Aleesca/Practica_GLP/Proyecto/Datos.md

# Grupo G1-1

## Datos comunes

| Campo | Dato |
|---|---|
| Zona climatica | Leon |
| Temperatura exterior de calculo | Pendiente de fijar con referencia tecnica valida |
| Ubicacion | Parcela catastral `8638004TN8183N` |
| Plano base | `01_Planos/instalacion_GLP.dwg` |
| Enunciado | `00_Info_proporcionada/TAREA 3 calculo instalación GLP.pdf` |

## Consumidores del grupo

| Consumidor | Potencia de calculo | Horas de funcionamiento | Distancias a medir |
|---|---:|---:|---|
| Consumidor 1: Horno secado | 60 kW | 12 h/d | Medir segun parcela y trazado real |
| Consumidor 2: Horno de secado | 60 kW | 12 h/d | Medir segun parcela y trazado real |
| Consumidor 3: Caldera vapor | 500 kW | 10 h/d | Medir segun parcela y trazado real |
| Consumidor 4: Caldera agua caliente | 300 kW | 8 h/d | Medir segun parcela y trazado real |
| Consumidor 5: Horno fusion | 700 kW | 4 h/d | Medir segun parcela y trazado real |
| Consumidor 6: Horno decapado | 1000 kW | 6 h/d | Medir segun parcela y trazado real |

## Uso operativo

- Este documento actua como fuente primaria de datos del grupo.
- La version normalizada para skills se mantiene en `.agents/skills/doc_tecnica_glp/references/datos_grupo_G1-1.md`.
- Las hipotesis derivadas de estos datos deben consolidarse en `Proyecto/Especificaciones/datos-partida.md`.
