Aleesca/Practica_GLP/ZZ_Normativa/normativa_requerida.md

# Normativa Identificada en el Modelo de Proyecto de GLP

A continuación se detallan las normas y reglamentos citados en el documento de referencia para la instalación de almacenamiento de GLP en depósitos fijos.

## 1. Instalaciones de Gas y GLP
*   **Real Decreto 191/2006**: Reglamento técnico de distribución y utilización de combustibles gaseosos.
    *   **ITC-ICG-03**: Instalaciones de almacenamiento de gases licuados del petróleo (GLP) en depósitos fijos.
*   **Norma UNE 60.250 (Abril 2004)**: Instalaciones de suministro de gases licuados del petróleo (GLP) en depósitos fijos para su consumo en instalaciones receptoras.

## 2. Edificación y Estructuras
*   **Real Decreto 314/2006**: Código Técnico de la Edificación (CTE).
    *   **DB-SI**: Seguridad en caso de Incendio.
    *   **DB-HS-3**: Calidad de aire interior.
    *   **DB-SU-8**: Seguridad frente al riesgo relacionado con la acción del rayo.
*   **Real Decreto 2661/1998**: Instrucción de Hormigón Estructural (EHE).

## 3. Instalaciones Eléctricas y Seguridad
*   **Real Decreto 848/2002**: Reglamento Electrotécnico para Baja Tensión (REBT) e Instrucciones Técnicas Complementarias (ITC).
*   **Norma UNE-EN 60.079(10)**: Material eléctrico para atmósferas de gas explosivas.
*   **Real Decreto 486/1997**: Disposiciones mínimas de seguridad y salud en los lugares de trabajo (Iluminación y condiciones ambientales).

## 4. Protección contra Incendios
*   **Real Decreto 1942/1993**: Reglamento de Instalaciones de Protección contra Incendios (RIPCI).
*   **Apartado 7.8 de la ITC-ICG-03**: Requerimientos específicos de protección contra incendios para GLP.

## 5. Otras Normativas
*   **Ley de Catastro Inmobiliario**: Modificación de diciembre de 2006 (BOE 286, de 30/11/2006) relativa a las referencias catastrales en proyectos.
