Aleesca/Practica_GLP/Proyecto/Anotaciones/autonomia_30_dias.md

# Autonomia de 30 dias

Esta nota fija el criterio para dimensionar el almacenamiento de GLP garantizando 30 días de suministro ininterrumpido para el Grupo G1-1.

## Criterio de Diseño
Aunque la recomendación técnica para instalaciones industriales suele ser de 15 días, el enunciado de la **TAREA 3** exige explícitamente una autonomía de **30 días**.

## Datos de Consumo (Grupo G1-1)
- **Energía diaria total:** 17.640 kWh/día.
- **Consumo másico diario:** 17.640 / 13,95 = **1.264,52 kg/día**.
- **Consumo volumétrico (Líquido a 20ºC):** 1.264,52 / 506 = **2,499 m³/día**.

## Cálculo del Volumen Útil y Geométrico
Para asegurar el suministro durante 30 días con una fracción útil del 65% (85% llenado máximo - 20% reserva):

- **Volumen útil necesario:** 2,499 m³/día x 30 días = **74,97 m³**.
- **Volumen geométrico mínimo:** 74,97 / 0,65 = **115,34 m³**.

## Conclusión
El volumen requerido (115,34 m³) obliga a la instalación de una **batería de depósitos**, ya que supera la capacidad individual de los modelos estándar de gran volumen.

---
**Véase también:**
- [Cálculo del volumen del depósito](calculo_volumen_deposito.md)
- [Caudales de consumidores](caudales_consumidores.md)
- [Selección del depósito](seleccion_deposito.md)
- [Distancias de seguridad](distancias_seguridad.md)
- [Memoria: Autonomía de almacenamiento](../Especificaciones/autonomia.md)
- [Memoria: Demanda y caudales de cálculo](../Especificaciones/demanda-consumo.md)
- [Memoria: Selección y dimensionado del depósito](../Especificaciones/deposito.md)
