Aleesca/Practica_GLP/Proyecto/Anotaciones/caudales_consumidores.md

# Caudales de consumidores

Esta nota define el procedimiento para pasar de potencia y régimen de uso a demanda de cálculo de la instalación para el Grupo G1-1.

## Metodología
Se utiliza la potencia nominal de cada equipo y sus horas de funcionamiento previstas para determinar la energía diaria necesaria.

## Tabla Maestra de Consumidores
| Consumidor | Potencia (kW) | Horas (h/d) | Energía (kWh/d) |
|---|---:|---:|---:|
| Horno secado 1 | 60 | 12 | 720 |
| Horno secado 2 | 60 | 12 | 720 |
| Caldera vapor | 500 | 10 | 5000 |
| Caldera agua caliente | 300 | 8 | 2400 |
| Horno fusion | 700 | 4 | 2800 |
| Horno decapado | 1000 | 6 | 6000 |
| **Total** | **2620** | - | **17640** |

## Salidas para el Proyecto
1.  **Potencia Máxima Simultánea:** 2.620 kW (base para el [trazado de red](trazado_red.md)).
2.  **Energía Diaria Total:** 17.640 kWh/d (base para el [cálculo del volumen](calculo_volumen_deposito.md)).

---
**Véase también:**
- [Cálculo del volumen del depósito](calculo_volumen_deposito.md)
- [Trazado de red](trazado_red.md)
- [Vaporización natural](vaporizacion_natural.md)
- [Dimensionado de tuberías GLP](dimensionado_tuberias_glp.md)
- [Memoria: Hipótesis y datos de partida](../Especificaciones/datos-partida.md)
- [Memoria: Demanda y caudales de cálculo](../Especificaciones/demanda-consumo.md)
- [Memoria: Red de distribución y regulación](../Especificaciones/red-distribucion.md)
- [Memoria: Autonomía de almacenamiento](../Especificaciones/autonomia.md)
