Aleesca/Practica_GLP/Proyecto/Anotaciones/criterios_normativos.md

# Criterios normativos

Esta nota recopila la normativa aplicable al proyecto de GLP del Grupo G1-1.

## Normativa Principal
- **UNE 60250:** Almacenamiento de GLP en depósitos fijos.
- **RD 919/2006:** Reglamento técnico de distribución y utilización de combustibles gaseosos.
- **CTE (Código Técnico de la Edificación):** Específicamente DB-SI y DB-SUA.

## Aplicación
Estos criterios justifican las [distancias de seguridad](distancias_seguridad.md) y los cálculos del [trazado de red](trazado_red.md).

---
**Véase también:**
- [Distancias de seguridad](distancias_seguridad.md)
- [Trazado de red](trazado_red.md)
- [Selección del depósito](seleccion_deposito.md)
- [Dimensionado de tuberías GLP](dimensionado_tuberias_glp.md)
- [Memoria: Hipótesis y datos de partida](../Especificaciones/datos-partida.md)
- [Memoria: Implantación y distancias de seguridad](../Especificaciones/implantacion-seguridad.md)
- [Memoria: Instalaciones auxiliares y de seguridad de la estación](../Especificaciones/instalaciones-auxiliares.md)
- [Cálculos justificados: Cálculos de seguridad y auxiliares](../Especificaciones/calculos-auxiliares.md)
