Aleesca/Practica_GLP/Proyecto/Anotaciones/pliego_condiciones_equipos_glp.md

# Pliego de Condiciones Técnicas: Adquisición de Equipos Principales GLP

## 1. Objeto del Documento
El presente pliego establece las condiciones técnicas, normativas y de suministro que regirán la adquisición de la batería de depósitos de Gases Licuados del Petróleo (GLP) y su sistema de vaporización asociado, destinados a la instalación receptora del Grupo G1-1.

## 2. Alcance del Suministro
El adjudicatario / fabricante deberá suministrar, transportar y garantizar los siguientes equipos principales:

1.  **Un (1) Depósito Principal Especial:** Modelo base Lapesa LP46A-22 (Aéreo Horizontal) de 46.200 litros (46,2 m³), modificado en fábrica para incorporar un serpentín de vaporización interna (modelo VIA 150 o equivalente validado).
2.  **Tres (3) Depósitos de Apoyo:** Modelo estándar Lapesa LP26A-22 (Aéreos Horizontales) de 26.300 litros (26,3 m³) cada uno.
3.  **Un (1) Armario de Calefacción:** Modelo Lapesa VPC30C, dimensionado para operar en conjunto con el serpentín interno del depósito principal, garantizando una capacidad de vaporización forzada no inferior a 227 kg/h.
4.  **Valvulería Asociada de Serie:** Todas las válvulas de seguridad (alivio), de llenado, extracción de fase líquida/gas y nivel magnético correspondientes a la homologación de cada depósito.

## 3. Condiciones Técnicas de los Equipos

### 3.1. Depósitos Estáticos (LP46A-22 Especial y LP26A-22)
- **Tipo de Gas:** Propano comercial / GLP.
- **Instalación:** Aérea, sobre cunas de hormigón armado.
- **Presión de Diseño:** Mínimo 20 bar.
- **Materiales:** Chapa de acero al carbono soldada según procedimientos homologados.
- **Tratamiento Exterior:** Granallado SA 2-1/2, imprimación anticorrosiva epoxi-poliamida de alto espesor y acabado exterior con esmalte de poliuretano color blanco, altamente reflectante.
- **Particularidad LP46A-22:** Deberá integrar de fábrica las bridas de conexión y la inserción del intercambiador de calor (serpentín VIA) en la generatriz inferior, asegurando el sellado y certificación conjunta del recipiente a presión.

### 3.2. Sistema de Vaporización (Serpentín VIA + Armario VPC30C)
- **Fluido Caloportador:** Agua glicolada (o fluido térmico especificado por el fabricante) calentada por el armario VPC30C y circulada mediante bomba hasta el serpentín interno.
- **Armario de Calefacción:** Deberá incluir caldera, bomba aceleradora, vaso de expansión, valvulería de corte, termostatos de control y seguridad, y armario de protección intemperie (ATEX si se ubica en Zona 2).
- **Rendimiento:** El sistema en conjunto debe ser capaz de vaporizar en continuo el caudal punta de diseño independientemente de la temperatura ambiente (hasta -10ºC exterior).

## 4. Normativa y Certificaciones Exigibles
El fabricante deberá entregar con el suministro la siguiente documentación, asegurando el cumplimiento normativo:
- **Directiva 2014/68/UE:** Certificado de Evaluación de Conformidad (Marcado CE) para Equipos a Presión.
- **Normas de Diseño:** UNE-EN 12542 (o ASME VIII Div. 1 según proceda por el fabricante).
- **Válvulas de Alivio:** Taradas a 20 bar (±10%), certificadas bajo UNE-EN 14129, incluyendo certificados de precinto.
- Dossier de calidad que incluya certificados de materiales (3.1 según EN 10204), radiografiado de soldaduras y acta de la prueba hidrostática o neumática realizada en fábrica.

## 5. Pruebas y Ensayos
### 5.1. En Fábrica (FAT - Factory Acceptance Tests)
El fabricante realizará las pruebas hidrostáticas a la presión de timbre exigida por la normativa vigente. En el caso del depósito especial LP46A, la prueba de presión deberá realizarse con el serpentín interno ya instalado para garantizar la estanqueidad de las bridas de conexión.

### 5.2. En Obra (SAT - Site Acceptance Tests)
Tras el montaje mecánico, el adjudicatario del montaje (con soporte del fabricante si es necesario) realizará pruebas de estanqueidad con nitrógeno de todo el conjunto y valvulería antes del primer llenado.

## 6. Condiciones de Entrega y Transporte
- **Transporte Especial:** El suministro se considera en condición DDP (Delivered Duty Paid) o franco sobre camión en la obra (Valle de Escombreras / ubicación designada).
- El fabricante será responsable de coordinar el transporte especial por dimensiones (convoy especial) y suministrará los planos de izado (orejetas) con el centro de gravedad marcado para la correcta descarga mediante grúa autopropulsada proporcionada por el contratista principal.
- Los depósitos deberán llegar presurizados con una presión positiva de gas inerte (nitrógeno) para garantizar la ausencia de humedad interna durante el tránsito.

## 7. Garantías
- **Garantía Mecánica y de Estanqueidad:** Mínimo de cinco (5) años contra defectos de fabricación o perforación por corrosión.
- **Garantía de Equipos Auxiliares (Armario VPC):** Mínimo de dos (2) años.
- El fabricante deberá garantizar la compatibilidad absoluta y el rendimiento del conjunto Depósito Principal + Serpentín VIA + Armario Calefacción.

---
**Véase también:**
- [Selección del depósito](seleccion_deposito.md)
- [Recopilación de accesorios y costes](recopilacion_accesorios_costes_glp.md)
- [Vaporización forzada](vaporizacion_forzada.md)
- [Potencia del armario de calefacción](potencia_armario_calefaccion.md)
- [Valvulería y accesorios](valvuleria_accesorios.md)
- [Memoria: Selección y dimensionado del depósito](../Especificaciones/deposito.md)
- [Memoria: Vaporización natural vs. vaporización forzada](../Especificaciones/vaporizacion.md)
- [Memoria: Características de los equipos auxiliares del almacenamiento](../Especificaciones/equipos-auxiliares.md)
- [Especificación: Presupuesto y mediciones](../Especificaciones/presupuesto.md)
