Aleesca/Practica_GLP/Proyecto/Especificaciones/anejos.md

# Cálculos justificados: Índice de anexos e inserción de planos

El presente documento recopila la relación y estructura de los anexos reales del proyecto de almacenamiento y distribución de GLP del Grupo G1-1, así como los planos técnicos integrados. Su función es delimitar qué piezas se incorporan como documentación anexa y qué contenidos deben permanecer dentro del capítulo de **Cálculos justificados**.

---

## 3.1. Índice de Anexos

El proyecto técnico se complementa con los siguientes anexos documentales y gráficos que contienen la información comercial de catálogo, los esquemas de funcionamiento y la documentación auxiliar que respalda el proyecto. Los cálculos mecánicos, térmicos e hidráulicos no se tratan como un anejo independiente: su desarrollo, tablas, resultados intermedios y comprobaciones forman parte del capítulo **Cálculos justificados** de la plantilla LaTeX.

*   **Anexo I: Planos Técnicos.**
    Representación gráfica a escala de la implantación, distancias de seguridad y esquema hidráulico (P&ID) de la instalación de GLP.
*   **Anexo II: Comprobaciones y Tablas Auxiliares.**
    Fichas técnicas y especificaciones comerciales del fabricante Lapesa correspondientes a:
    *   Depósitos de almacenamiento modelos LP46A-22 (Modelo Especial) y LP26A-22.
    *   Serpentín del vaporizador forzado interno modelo VIA 150.
    *   Armario de calefacción exterior y caldera modelo VPC30C.

El desarrollo matemático, el control de trazabilidad y las comprobaciones hidráulicas tramo a tramo para la red de distribución aérea en Media Presión B (1,7 bar relativos) se integran en las subsecciones del capítulo **Cálculos justificados**. Si se incorporan tablas auxiliares de gran formato, se insertarán como piezas editoriales del capítulo, no como un anejo de cálculos.

---

## Capítulo de Planos

El conjunto gráfico del proyecto está conformado por tres planos técnicos fundamentales de diseño, insertados de forma consecutiva e independiente al final de la memoria documental:

1.  **Plano nº 1: Situación y Emplazamiento (`situacion-emplazamiento.pdf`).**
    Representación de la ubicación geográfica de la parcela catastral `8638004TN8183N` en el término municipal de León, indicando la orientación y los viales de comunicación circundantes.
2.  **Plano nº 2: Distancias de Seguridad y Acondicionamiento del Recinto (`Plano_distancias_seguridad.pdf`).**
    Plano a escala del recinto vallado del almacenamiento de categoría A-500. Detalla el replanteo de la cuna y losa de hormigón de los cuatro depósitos, la localización de los muros EI-120 de protección y la verificación geométrica de las distancias de seguridad mínimas admisibles en todas las direcciones radiales.
3.  **Plano nº 3: Esquema de Principio (P&ID) y Conducciones (`plano_Esquema_instalacion.pdf`).**
    Diagrama de flujo hidráulico de la instalación. Muestra la boca de carga rápida, el colector común de fase gaseosa y líquida, el conexionado del vaporizador forzado VIA 150 con el armario VPC30C, la valvulería de seguridad y regulación de primer salto (1,7 bar), el trazado de las tuberías de distribución aérea con sus diámetros y el segundo salto de regulación (37 mbar) a la entrada de cada consumidor.

## Referencias relacionadas
- [Especificación: Capítulo de Cálculos justificados](calculos-justificados.md)
- [Memoria: Selección y dimensionado del depósito](deposito.md)
- [Memoria: Implantación y distancias de seguridad](implantacion-seguridad.md)
- [Memoria: Red de distribución y regulación](red-distribucion.md)
- [Cálculos justificados: Cálculos de seguridad y auxiliares](calculos-auxiliares.md)
- [Pliego de condiciones técnicas: adquisición de equipos principales GLP](../Anotaciones/pliego_condiciones_equipos_glp.md)
- [Implantación y distancias de seguridad](../Anotaciones/distancias_seguridad.md)
