Aleesca/Practica_GLP/Proyecto/Especificaciones/equipos-auxiliares.md

# Memoria: Características de los Equipos Auxiliares del Almacenamiento

## 1. Boca de Carga y Limitador de Llenado
La operación de llenado de propano líquido en los depósitos se realiza de forma centralizada en el colector común de fase líquida mediante una boca de carga única exterior, diseñada para soportar las presiones de trasvase del camión cisterna:
*   **Acoplamiento Rápido:** Se adopta un acoplamiento rápido macho de rosca Acme de **$3\text{''}$** (modelo **RegO 7579C** o equivalente) fabricado en latón de alta resistencia al desgaste mecánico.
*   **Seguridades Antirretorno:** Dispone de una **doble válvula de retención integrada (check valve)** en serie para evitar el escape accidental de gas licuado al desconectar la manguera de llenado.
*   **Válvula de Purga y Cierre:** Se monta una válvula de purga de bola manual de $1/4\text{''}$ para despresurizar de forma segura el espacio entre acoplamientos antes de la desconexión física.
*   **Válvula Limitadora de Llenado al $85\%$:** Cada depósito incorpora una válvula interna automática de boya (limitadora de nivel máximo de llenado) que interrumpe mecánicamente el paso de líquido cuando el nivel del propano alcanza el $85\%$ del volumen geométrico del recipiente.

## 2. Equipos de Regulación de Presión y Válvulas de Corte
Para la estabilidad del flujo y aislamiento de componentes en la estación, se disponen los siguientes equipos:
*   **Regulador de Primer Salto (MPB):** Acoplado directamente a la salida del colector común de fase de gas de los depósitos. Se utiliza un regulador de alta capacidad **RegO 1588V** o **Clesse APS** tarado a **$1,7\text{ bar relativos}$**. Incorpora válvula de seguridad de mínima presión por bloqueo de seguridad (UPS) y filtro de partículas metálicas en la entrada.
*   **Válvulas de Corte General:** Válvulas de esfera de paso total de bronce o acero forjado (clase ANSI 300) con accionamiento manual por palanca e indicación de posición abierta/cerrada, situadas a la salida de cada depósito y en la entrada y salida de cada regulador para permitir el aislamiento completo en labores de mantenimiento.

## 3. Equipo de Trasvase (Bomba)
Para la tipología y demandas operativas de esta planta industrial (donde el GLP fluye por diferencia de presiones gaseosas y por gravedad hacia los vaporizadores), **no se requiere la instalación de una bomba activa de trasvase de líquido** en la estación de almacenamiento. Las operaciones de carga de los depósitos se realizan aprovechando la propia bomba de impulsión de fase líquida del camión cisterna y la línea de retorno de fase de gas (línea de equilibrio de presiones) que une la cisterna con el colector de la estación.

## 4. Válvulas de Seguridad por Sobrepresión
Para proteger los depósitos de almacenamiento frente a sobrepresiones excesivas debidas a la radiación solar estacional o al calor de un incendio cercano, cada depósito está equipado con:
*   **Configuración:** **Dos unidades de válvulas de seguridad independientes** de resorte por depósito (taradas a la misma presión de apertura).
*   **Modelo de Válvula:** Válvula de alivio de presión **RegO RS 3145** (o equivalente de Lapesa) fabricada en bronce y acero inoxidable.
*   **Presión de Tarado:** Apertura completa a **$20\text{ bar relativos}$**, presión inferior a la presión de prueba del recipiente ($25\text{ bar}$) para garantizar que no se supera el límite elástico del acero del depósito en caso de emergencia.
*   **Acoplamiento y Colector de Escape:** Las válvulas se montan sobre colectores de desvío de tres vías (**colectores de acoplamiento CD45**), lo que permite desmontar e inspeccionar periódicamente una de las dos válvulas de seguridad sin necesidad de desgasificar o vaciar el depósito de almacenamiento, garantizando que al menos una de las válvulas de alivio permanece en servicio en todo momento. Las descargas se conducen de forma vertical a la atmósfera mediante tubos deflectores que sobresalen por encima del depósito.

## Referencias relacionadas
- [Memoria: Selección y dimensionado del depósito](deposito.md)
- [Memoria: Vaporización natural vs. vaporización forzada](vaporizacion.md)
- [Memoria: Instalaciones auxiliares y de seguridad de la estación](instalaciones-auxiliares.md)
- [Cálculos justificados: Cálculos de seguridad y auxiliares](calculos-auxiliares.md)
- [Valvulería y accesorios comerciales](../Anotaciones/valvuleria_accesorios.md)
- [Pliego de condiciones técnicas: adquisición de equipos principales GLP](../Anotaciones/pliego_condiciones_equipos_glp.md)
- [Vaporización forzada](../Anotaciones/vaporizacion_forzada.md)
