Aleesca/Practica_GLP/Proyecto/Especificaciones/implantacion-seguridad.md

# Memoria: Implantación y Distancias de Seguridad

## 1. Clasificación Reglamentaria de las Instalaciones y Entorno
El almacenamiento conjunto proyectado cuenta con un volumen geométrico total acumulado de **$124,30\text{ m}^3$** de propano comercial líquido. De acuerdo con lo establecido en la norma **UNE 60250:2008** y el *Reglamento técnico de distribución y utilización de combustibles gaseosos* (RD 919/2006, ITC-ICG 03), la estación de almacenamiento se clasifica como una **instalación del Tipo A-500** al cumplir la condición:

$$ 100\text{ m}^3 < V_{total} \le 500\text{ m}^3 $$

Esta clasificación impone los máximos requisitos de distancias de seguridad y protección contra incendios de la normativa para almacenamientos de GLP de consumo industrial.

## 2. Justificación Geométrica de la Implantación de la Batería
La batería de depósitos se sitúa en paralelo en una zona abierta y despejada del exterior de la parcela catastral **8638004TN8183N**, facilitando la ventilación natural y el acceso del camión cisterna de suministro. 

*   **Separación Mínima entre Depósitos de la Batería:**
    Según la norma UNE 60250, para depósitos aéreos de la misma batería, la distancia mínima de separación entre las paredes de dos tanques contiguos debe ser igual a la mitad del diámetro del depósito mayor, con un límite mínimo absoluto de **$1,0\text{ m}$**. Dado que todos los depósitos seleccionados (LP46A y LP26A) tienen un diámetro común exterior de $2.200\text{ mm}$ ($\phi = 2,2\text{ m}$), la separación mínima reglamentaria resulta:
    $$ D_{separacion} \ge \frac{\phi}{2} = \frac{2,2\text{ m}}{2} = 1,10\text{ m} $$
    Para cumplir con este requisito técnico y permitir un paso desahogado para labores de mantenimiento y evacuación de aguas pluviales de los tanques, se adopta una **separación real de $1,10\text{ m}$ en paralelo** entre los ejes de cunas y paredes de los cuatro depósitos de la batería.

## 3. Verificación de Distancias de Seguridad y Medidas Reductoras
La norma UNE 60250 exige mantener unas distancias de seguridad mínimas desde los orificios de los depósitos (válvulas de seguridad, boca de carga y purgas) y desde las paredes exteriores de los tanques hacia elementos externos de la parcela. Para depósitos de Tipo A-500, la distancia de referencia básica es de **$10\text{ metros}$**.

Dada la colindancia de la parcela catastral con límites de propiedad ajena y viales en sus bordes norte y oeste, no es viable cumplir con los $10\text{ metros}$ de separación natural. Se recurre, por tanto, a la aplicación de las **medidas reductoras** contempladas en la normativa (UNE 60250, apartado de muros):
*   **Instalación de Muros Cortafuegos EI-120:**
    Se proyecta la construcción de dos muros de protección cortafuegos con clasificación de resistencia al fuego **$EI-120$** (estable, estanco e islante térmico al fuego durante al menos 120 minutos), fabricados en hormigón armado con un espesor mínimo de $150\text{ mm}$ y una altura que sobresale un metro sobre el punto más alto del depósito (altura del muro: $3,50\text{ metros}$).
*   **Reducción de Distancias al $50\%$:**
    El uso de estos muros cortafuegos EI-120 permite **reducir al $50\%$** la distancia de seguridad exigida hacia límites de propiedad, locales públicos y focos de ignición no clasificados, reduciéndose la distancia mínima a **$5,0\text{ metros}$** de separación medida alrededor del muro (trayectoria de gas).
*   **Verificación Real en Plano:**
    Las distancias reales medidas en el plano de implantación (`Plano_distancias_seguridad.pdf`), considerando la trayectoria de gas bordeando los muros cortafuegos EI-120, superan en todos los puntos críticos los $5,0\text{ metros}$ reglamentarios, demostrando la viabilidad técnica y legal del emplazamiento elegido.

## 4. Vallado y Cerramiento Perimetral de Seguridad
Para evitar el acceso de personal ajeno a la instalación y prevenir riesgos de sabotaje o manipulación accidental de válvulas, el recinto de la estación de almacenamiento común estará delimitado por un **cerramiento de seguridad perimetral**:
*   **Características del Vallado:** Vallado metálico tipo Hércules o de malla de simple torsión con una altura mínima de **$2,0\text{ metros}$** sobre postes de acero anclados en solera de hormigón. La parte inferior del vallado se cerrará con un zócalo continuo de hormigón para evitar entradas de vegetación o animales.
*   **Puertas de Acceso:** Se dispondrán dos puertas metálicas de salida peatonal en extremos opuestos del recinto, equipadas con barra antipánico y sentido de apertura obligatorio hacia el exterior de la estación. Adicionalmente, se dispondrá de una puerta de doble hoja de $4,0\text{ metros}$ de ancho para el acceso y mantenimiento de componentes grandes, abriéndose siempre hacia fuera y permaneciendo cerrada bajo candado de seguridad industrial.
*   **Señalización de Seguridad:** En las paredes exteriores del vallado se dispondrán carteles normalizados legibles de seguridad con las indicaciones: "Peligro: Materia Inflamable - Propano", "Prohibido Fumar o Encender Fuego" y "Prohibido el Paso a Toda Persona Ajena a la Instalación".

## Referencias relacionadas
- [Memoria: Selección y dimensionado del depósito](deposito.md)
- [Memoria: Instalaciones auxiliares y de seguridad de la estación](instalaciones-auxiliares.md)
- [Memoria: Promotor, plazo de ejecución y accesos](promotor-plazo-accesos.md)
- [Cálculos justificados: Cálculos de seguridad y auxiliares](calculos-auxiliares.md)
- [Implantación y distancias de seguridad](../Anotaciones/distancias_seguridad.md)
- [Criterios normativos](../Anotaciones/criterios_normativos.md)
- [Selección del depósito](../Anotaciones/seleccion_deposito.md)
