Aleesca/Practica_GLP/Proyecto/Especificaciones/intro.md

# Memoria: Introducción, Objeto y Antecedentes

## 1. Objeto del Proyecto
El objeto del presente proyecto es definir, justificar y dimensionar la instalación de almacenamiento y la red de distribución de Gases Licuados del Petróleo (GLP), concretamente propano comercial, para dar suministro energético térmico a una planta industrial situada en la provincia de León. 

El alcance del diseño abarca desde la estación de almacenamiento común —constituida por una batería de depósitos aéreos horizontales y su sistema de vaporización asociado— hasta la regulación secundaria e individual a la entrada de cada uno de los seis puntos de consumo (consumidores industriales). El diseño de la instalación se proyecta bajo premisas estrictas de seguridad industrial, optimización vial y eficiencia técnica, garantizando en todo momento el cumplimiento de la reglamentación y normativa española vigente.

## 2. Antecedentes
La planta industrial requiere de un suministro continuo de calor de alta densidad energética y estabilidad térmica para sus procesos de secado, fusión, vaporización y decapado. Ante la inexistencia de una red de distribución de gas natural en las proximidades de la parcela catastral, se realiza un estudio de alternativas energéticas:
*   **Gasoil o combustibles líquidos:** Descartados debido a su mayor impacto de emisiones contaminantes, costes operativos inestables y requerimientos de mantenimiento más exigentes para los quemadores de hornos de precisión.
*   **Electricidad:** Descartada por su inviabilidad económica para potencias de calefacción agregadas del orden de megavatios.
*   **Propano comercial (GLP):** Seleccionado como la alternativa óptima debido a su elevado Poder Calorífico Superior (PCS = $13,95\text{ kWh/kg}$), su combustión limpia, la facilidad de regulación de la temperatura en los quemadores industriales y su estabilidad de suministro mediante transporte por camión cisterna.

La dirección técnica de la planta industrial ha solicitado la redacción de este proyecto con el propósito de legalizar y ejecutar la instalación común de almacenamiento y la posterior distribución interior de propano, cubriendo los siguientes seis consumidores específicos en la fase de diseño:
1.  **Horno de secado 1 (C1):** $60\text{ kW}$ de potencia nominal.
2.  **Horno de secado 2 (C2):** $60\text{ kW}$ de potencia nominal.
3.  **Caldera de vapor (C3):** $500\text{ kW}$ de potencia nominal.
4.  **Caldera de agua caliente (C4):** $300\text{ kW}$ de potencia nominal.
5.  **Horno de fusión (C5):** $700\text{ kW}$ de potencia nominal.
6.  **Horno de decapado (C6):** $1000\text{ kW}$ de potencia nominal.

La redacción de este documento y sus cálculos hidráulicos y de implantación correspondientes servirán como base técnica para la ejecución material de las obras y su posterior tramitación ante los organismos oficiales de Industria de la Junta de Castilla y León.

## Referencias relacionadas
- [Memoria: Hipótesis y datos de partida](datos-partida.md)
- [Memoria: Demanda y caudales de cálculo](demanda-consumo.md)
- [Memoria: Selección y dimensionado del depósito](deposito.md)
- [Memoria: Red de distribución y regulación](red-distribucion.md)
- [Memoria: Implantación y distancias de seguridad](implantacion-seguridad.md)
- [Criterios normativos](../Anotaciones/criterios_normativos.md)
- [Caudales de consumidores](../Anotaciones/caudales_consumidores.md)
