Aleesca/Practica_GLP/Proyecto/Especificaciones/presupuesto.md

# Especificación: Presupuesto y Mediciones (Secciones 4.1 a 4.5)

## Propósito
Detallar los costes económicos de la instalación de GLP, estructurando las mediciones reales de obra, los cuadros de precios unitarios y descompuestos, y el presupuesto de ejecución final.

## Contenido obligatorio

### Sección 4.1 ÍNDICE DE PRESUPUESTO.
- Estructurar el presupuesto en capítulos lógicos de obra:
  - Capítulo 1: Obra Civil (Excavaciones, cunas de hormigón, losa del vaporizador y vallado perimetral).
  - Capítulo 2: Almacenamiento (Depósitos Lapesa LP46A y LP26A, anclajes y cunas).
  - Capítulo 3: Equipos y Valvulería de la Estación (Vaporizador VIA 150, reguladores Clesse, válvulas de seguridad, colector común, boca de carga).
  - Capítulo 4: Red de Distribución (Tuberías de cobre UNE-EN 1057, accesorios de soldadura, soportes y ménsulas).
  - Capítulo 5: Instalaciones de Seguridad y Auxiliares (Puesta a tierra, red de pulverización de agua, extintores portátiles).
  - Capítulo 6: Ensayos y Certificaciones (Pruebas de presión, dirección de obra, puesta en marcha).

### Sección 4.2 CUADRO DE PRECIOS Nº 1.
- Listar los precios unitarios (en euros) de adquisición de todos los materiales, maquinaria y horas de mano de obra en número y letra:
  - Depósito LP46A, Depósito LP26A, Armario de vaporización VPC30C con VIA 150.
  - Tuberías de cobre por metro lineal ($\phi 54$, $\phi 42$, $\phi 35$, $\phi 28$, $\phi 22$).
  - Válvulas de corte, codos, reguladores y picas de tierra.
  - Oficiales de primera, ayudantes e ingenieros de montaje.

### Sección 4.3 CUADRO DE PRECIOS Nº 2.
- Definir los precios de unidades de obra descompuestos, integrando materiales, mano de obra instaladora, medios auxiliares e imprevistos (indicados en número y letra).

### Sección 4.4 MEDICIONES.
- Exponer el recuento físico exacto de todas las unidades de obra medidas sobre los planos de trazado y esquema base:
  - Longitudes reales de conducción de cobre por diámetro tramo a tramo.
  - Conteo exacto de válvulas de corte Giacomini, reguladores de primera y segunda etapa, codos de $90^\circ$ y derivaciones en te.
  - Volumen de excavación y hormigón estructural para cunas y losa.
  - Recuento de picas y conductor desnudo de tierra, número de rociadores.

### Sección 4.5 PRESUPUESTO.
- Consolidar los importes económicos parciales por capítulos.
- Calcular el Presupuesto de Ejecución Material (PEM) como suma de los capítulos.
- Aplicar los coeficientes legales típicos para obtener el Presupuesto de Ejecución por Contrata (PEC):
  - Gastos Generales ($13\%$).
  - Beneficio Industrial ($6\%$).
  - Impuesto sobre el Valor Añadido ($21\%$ IVA).
- Presentar el Presupuesto de Ejecución por Contrata total en letra y número.

## Estilo de redacción
Tono contable, descriptivo, preciso y formal. Presentación estructurada en tablas claras. Longitud orientativa: 2 a 3 páginas.

## Figuras, tablas y resultados
- **Tablas de precios unitarios y descompuestos:** Columnas de Código, Descripción, Unidad, Importe (en cifra) e Importe en letra.
- **Tabla de Mediciones:** Desglosada por tramos de red y capítulos de la estación.
- **Tabla Resumen del Presupuesto:** Por capítulos, PEM, PEC y Liquidación final.

## Conexiones
- **Alcance:** Requisito 5 (Conducción - mediciones) y Requisito 6 (Estación y esquema - recuentos).
- **Anotaciones:** [Recopilación y coste de accesorios por tramo GLP](../Anotaciones/recopilacion_accesorios_costes_glp.md) (evidencia), [Reporte: catálogos y precios de accesorios GLP](../Anotaciones/reporte_accesorios.md) (evidencia), [Trazado de red](../Anotaciones/trazado_red.md) (decisión).

## Referencias relacionadas
- [Memoria: Red de distribución y regulación](red-distribucion.md)
- [Memoria: Selección y dimensionado del depósito](deposito.md)
- [Memoria: Características de los equipos auxiliares del almacenamiento](equipos-auxiliares.md)
- [Memoria: Instalaciones auxiliares y de seguridad de la estación](instalaciones-auxiliares.md)
- [Recopilación y coste de accesorios por tramo GLP](../Anotaciones/recopilacion_accesorios_costes_glp.md)
- [Reporte: catálogos y precios de accesorios GLP](../Anotaciones/reporte_accesorios.md)
- [Pliego de condiciones técnicas: adquisición de equipos principales GLP](../Anotaciones/pliego_condiciones_equipos_glp.md)
- [Dimensionado de tuberías GLP](../Anotaciones/dimensionado_tuberias_glp.md)

## Criterios de aceptación
- [ ] El presupuesto está estructurado en al menos 6 capítulos lógicos.
- [ ] Los cuadros de precios contienen la descripción en número y letra.
- [ ] Las mediciones coinciden exactamente con los recuentos y metros de los archivos de anotaciones.
- [ ] Se detalla el cálculo completo de PEM a PEC aplicando los porcentajes correspondientes.
