Aleesca/Practica_GLP/Proyecto/Especificaciones/promotor-plazo-accesos.md

# Memoria: Promotor, Plazo de Ejecución y Accesos

## 1. Promotor y Proyectistas de la Instalación
La redacción y diseño técnico del presente proyecto se realiza a petición del promotor institucional y académico, la **Universidad de León (ULE)**, a través de la **Escuela de Ingenierías Industrial, Informática y Aeroespacial** (Grado en Ingeniería Mecánica, asignatura de Instalaciones II).

La autoría y responsabilidad de los cálculos, redacción y planos de la instalación de GLP corresponde al equipo de ingenieros proyectistas que integran el **Grupo G1-1**:
*   **Alberto España Carrete**
*   **Carlos Fernández Palanca**
*   **Rubén Modino López**
*   **Juan Diego Niño González**

El desarrollo del proyecto cuenta con la supervisión y tutorización técnica del profesor **Roberto Getino de la Mano**, en calidad de tutor técnico del proyecto.

## 2. Plazo de Ejecución de las Obras
El plazo estimado de ejecución material para la totalidad de las obras e instalaciones, incluyendo las fases de obra civil, montaje mecánico, pruebas y puesta en servicio, se fija en **$3\text{ meses}$** a partir de la concesión de las licencias municipales de obras e industria pertinentes. 

El cronograma de ejecución se distribuye en las siguientes fases clave:
1.  **Mes 1 (Obra Civil y Cimentaciones):**
    *   Excavación y explanación del terreno para la solera del recinto de almacenamiento.
    *   Construcción de losas de hormigón armado, cunas de apoyo para los cuatro depósitos y soleras para el vaporizador exterior.
    *   Construcción de los dos muros cortafuegos de hormigón armado EI-120 (linderos norte y oeste).
    *   Instalación de las canalizaciones subterráneas para la puesta a tierra.
2.  **Mes 2 (Montaje de Depósitos e Instalación Mecánica):**
    *   Transporte, izado y anclaje de los depósitos Lapesa LP46A y LP26A sobre sus cunas de apoyo.
    *   Montaje e interconexión mecánica del serpentín vaporizador VIA 150 en la brida DN400 del depósito principal.
    *   Instalación del armario de calefacción VPC30C y conexión del circuito de agua caliente.
    *   Montaje de las tuberías aéreas de cobre UNE-EN 1057 de la red general, colectores, soportes, liras de dilatación y válvulas de corte y seguridad.
3.  **Mes 3 (Pruebas, Aislamiento y Tramitación):**
    *   Pruebas de resistencia mecánica e hidrostática/neumática de la red general a la presión reglamentaria de $2,5\text{ bar relativos}$ y pruebas de estanqueidad de las uniones soldadas.
    *   Pintado de color amarillo (RAL 1021) de toda la red exterior e instalación del vallado perimetral con doble puerta de salida.
    *   Montaje de armarios de regulación de segundo salto y contadores en los puntos de consumo.
    *   Pruebas de continuidad eléctrica y verificación de resistencia de puesta a tierra ($R < 20\ \Omega$).
    *   Recepción de certificados de fabricación (Directiva PED 2014/68/UE) y emisión del certificado de fin de obra para la legalización industrial.

## 3. Accesos y Maniobrabilidad del Camión Cisterna
La estación de almacenamiento Tipo A-500 requiere de recargas periódicas mediante un **camión cisterna articulado de transporte de GLP** (longitud típica de $16,5\text{ metros}$ y peso máximo autorizado de $40\text{ toneladas}$). Los accesos a la estación de almacenamiento se diseñan conforme a los siguientes requisitos viales y de seguridad:
*   **Vías de Acceso:** La parcela catastral conecta de forma directa con un vial industrial pavimentado de $8\text{ metros}$ de ancho, lo cual permite la libre maniobra y cruce de vehículos pesados sin interferir con el tráfico exterior.
*   **Radio de Giro:** Se ha verificado que el radio de curvatura de la calzada de acceso y del recinto de aproximación de la estación es superior a **$12,5\text{ metros}$** (medidos en el eje interior), permitiendo la entrada directa y salida en marcha hacia adelante del camión cisterna sin necesidad de maniobras de marcha atrás complejas.
*   **Pendiente Vial:** Las rampas y calzadas del entorno del recinto de almacenamiento presentan pendientes longitudinales inferiores al **$5\%$**, cumpliendo holgadamente el límite reglamentario de la norma UNE 60250 para evitar deslizamientos del vehículo pesado durante la descarga de GLP en condiciones invernales de heladas o nieve en León.
*   **Zona de Descarga:** El camión cisterna se posicionará en paralelo al cerramiento de la estación, en una zona llana y delimitada donde se ubican la boca de carga del colector y las conexiones del camión. El conductor mantendrá visibilidad directa continua sobre los manómetros de los depósitos durante toda la operación de descarga.

## Referencias relacionadas
- [Memoria: Introducción, objeto y antecedentes](intro.md)
- [Memoria: Implantación y distancias de seguridad](implantacion-seguridad.md)
- [Especificación: Presupuesto y mediciones](presupuesto.md)
- [Cálculos justificados: Índice de anexos e inserción de planos](anejos.md)
- [Implantación y distancias de seguridad](../Anotaciones/distancias_seguridad.md)
- [Selección del depósito](../Anotaciones/seleccion_deposito.md)
