Aleesca/Practica_GLP/Proyecto/Planificacion/esquema_memoria.md

# Esquema de la memoria

## 1. Introduccion
- Contexto del trabajo.
- Objetivo general y objetivos especificos.
- Alcance del proyecto.

## 2. Metodologia
La redaccion detallada de este bloque se desarrolla en `Proyecto/Especificaciones/metodologia.md` y se apoya en las anotaciones tecnicas de `Proyecto/Anotaciones/`.

### 2.1 Hipotesis y datos de partida
- Condiciones climaticas y de emplazamiento.
- Datos de consumidores y regimen de uso.
- Propiedades y parametros de calculo adoptados.
- Criterios y simplificaciones asumidas.

### 2.2 Desarrollo de los calculos
#### 2.2.1 Demanda y caudal de calculo
- Potencias de los consumidores.
- Simultaneidad y demanda total.
- Caudal de calculo de la instalacion.

#### 2.2.2 Autonomia de almacenamiento
- Consumo diario equivalente.
- Criterio de autonomia de 30 dias.
- Volumen util requerido.

#### 2.2.3 Vaporizacion natural del deposito
- Condiciones exteriores de calculo.
- Criterio de vaporizacion disponible.
- Comprobacion frente a la demanda.

#### 2.2.4 Seleccion y dimensionado del deposito
- Eleccion de la configuracion de almacenamiento.
- Capacidad nominal y equipos asociados.
- Justificacion de la solucion adoptada.

#### 2.2.5 Red de distribucion
- Planteamiento de la red.
- Criterios de dimensionado.
- Verificacion de presiones y perdidas de carga.

#### 2.2.6 Implantacion y distancias de seguridad
- Ubicacion de la estacion de almacenamiento.
- Distancias reglamentarias y condicionantes del emplazamiento.
- Justificacion de seguridad y accesibilidad.

## 3. Conclusiones
- Sintesis de resultados principales.
- Valoracion de la solucion adoptada.
- Cumplimiento de objetivos.

## 4. Limitaciones
- Limitaciones derivadas de los datos de partida.
- Simplificaciones del modelo de calculo.
- Aspectos fuera del alcance.

## 5. Bibliografia
- Normativa aplicable.
- Catalogos y guias tecnicas consultadas.
- Fuentes de datos del proyecto.

## 6. Anejos
- Anejo I: Planos.
- Anejo II: Comprobaciones y tablas auxiliares.

Los cálculos desarrollados no constituyen un anejo independiente. Su desarrollo numérico, tablas de comprobación y bibliografía propia se integran en el capítulo **Cálculos justificados** del cuerpo principal.
