Aleesca/Practica_GLP/Proyecto/Planificacion/matriz_fuentes.md

# Matriz de Fuentes Técnicas y Trazabilidad (Completada y Normalizada)

Este documento centraliza el contrato de fuentes activo y la trazabilidad del proyecto de GLP para el Grupo G1-1. Mapea la estructura canónica de la memoria LaTeX, el alcance formal del proyecto y las notas técnicas de ingeniería que actúan como evidencia.

---

## 1. Clasificación de Archivos de Anotaciones (`Proyecto/Anotaciones/`)

Se clasifican a continuación las 16 notas técnicas y registros de cálculo de la carpeta de evidencias según las siguientes categorías metodológicas:
- **Cálculo (Calculation):** Desarrollos matemáticos, ecuaciones y memorias de cálculo.
- **Decisión (Decision):** Justificaciones técnicas de alternativas de diseño adoptadas.
- **Evidencia (Evidence):** Datos de partida meteorológicos, catálogos comerciales, fichas técnicas o conteo de componentes.
- **Criterio Normativo (Regulatory criteria):** Requisitos técnicos impuestos por reglamentos y normas UNE.

| Archivo de Anotación | Categoría | Datos Soportados y Contenido Técnico |
| :--- | :--- | :--- |
| [autonomia_30_dias.md](file:///H:/Unidades%20compartidas/Practicas_Inst2/4_GLPs/Proyecto/Anotaciones/autonomia_30_dias.md) | **Cálculo** | Balance diario de propano. Consumo másico diario ($1.264,52 \text{ kg/día}$) y volumétrico líquido ($2,499 \text{ m}^3/\text{día}$). |
| [calculo_volumen_deposito.md](file:///H:/Unidades%20compartidas/Practicas_Inst2/4_GLPs/Proyecto/Anotaciones/calculo_volumen_deposito.md) | **Cálculo** | Desarrollo matemático para obtener el volumen geométrico mínimo ($115,34 \text{ m}^3$) a partir del volumen útil considerando llenado del $85\%$. |
| [caudales_consumidores.md](file:///H:/Unidades%20compartidas/Practicas_Inst2/4_GLPs/Proyecto/Anotaciones/caudales_consumidores.md) | **Cálculo** | Cálculo individual y total del consumo másico ($Q_{\text{kg/h}}$) por equipo según su potencia nominal y horas de operación. Potencia total $2.620 \text{ kW}$. |
| [criterios_normativos.md](file:///H:/Unidades%20compartidas/Practicas_Inst2/4_GLPs/Proyecto/Anotaciones/criterios_normativos.md) | **Criterio Normativo** | Recopilación de reglamentos base de aplicación al proyecto: RD 919/2006, ITC-ICG 03, UNE 60250:2008, CTE DB-SI y DB-SUA. |
| [dimensionado_tuberias_glp.md](file:///H:/Unidades%20compartidas/Practicas_Inst2/4_GLPs/Proyecto/Anotaciones/dimensionado_tuberias_glp.md) | **Cálculo** | Memoria de cálculo completa tramo a tramo de pérdidas de carga (fórmula de Renouard MPB) y velocidades operacionales ($\le 10 \text{ m/s}$). |
| [distancias_seguridad.md](file:///H:/Unidades%20compartidas/Practicas_Inst2/4_GLPs/Proyecto/Anotaciones/distancias_seguridad.md) | **Criterio Normativo** | Clasificación de la instalación (A-500) y verificación reglamentaria de distancias mínimas en la parcela según UNE 60250. |
| [pliego_condiciones_equipos_glp.md](file:///H:/Unidades%20compartidas/Practicas_Inst2/4_GLPs/Proyecto/Anotaciones/pliego_condiciones_equipos_glp.md) | **Criterio Normativo** | Pliego de condiciones técnicas para adquisición de depósitos Lapesa LP46/LP26, intercambiador VIA 150 y armario VPC30C. FAT/SAT y Directiva 2014/68/UE. |
| [potencia_armario_calefaccion.md](file:///H:/Unidades%20compartidas/Practicas_Inst2/4_GLPs/Proyecto/Anotaciones/potencia_armario_calefaccion.md) | **Cálculo** | Justificación del armario de calefacción (caldera de $45\text{ kW}$) debido a la insuficiencia térmica para cubrir la demanda punta. |
| [recopilacion_accesorios_costes_glp.md](file:///H:/Unidades%20compartidas/Practicas_Inst2/4_GLPs/Proyecto/Anotaciones/recopilacion_accesorios_costes_glp.md) | **Evidencia** | Precios unitarios de Salvador Escoda, Lapesa, Giacomini y RegO, incluyendo estimaciones de mano de obra y servicios de ingeniería. |
| [reporte_accesorios.md](file:///H:/Unidades%20compartidas/Practicas_Inst2/4_GLPs/Proyecto/Anotaciones/reporte_accesorios.md) | **Evidencia** | Conteo de codos, válvulas, reguladores y acoplamientos del sistema con sus enlaces a catálogos europeos e identificación ATEX. |
| [seleccion_deposito.md](file:///H:/Unidades%20compartidas/Practicas_Inst2/4_GLPs/Proyecto/Anotaciones/seleccion_deposito.md) | **Decisión** | Evolución del diseño y descarte de depósitos LPVI 59A debido a la longitud de parcela. Selección de batería mixta 1xLP46A-22 + 3xLP26A-22. |
| [temperatura_diseno.md](file:///H:/Unidades%20compartidas/Practicas_Inst2/4_GLPs/Proyecto/Anotaciones/temperatura_diseno.md) | **Evidencia** | Justificación de la temperatura exterior de diseño ($-5 \text{ ºC}$ para León) utilizando el percentil $99,6\%$ climáticos del IDAE. |
| [trazado_red.md](file:///H:/Unidades%20compartidas/Practicas_Inst2/4_GLPs/Proyecto/Anotaciones/trazado_red.md) | **Decisión** | Definición del trazado de cobre aéreo EN 1057 y topología general de cálculo tramo a tramo medido en plano catastral. |
| [valvuleria_accesorios.md](file:///H:/Unidades%20compartidas/Practicas_Inst2/4_GLPs/Proyecto/Anotaciones/valvuleria_accesorios.md) | **Decisión** | Selección comercial de reguladores de presión RegO 1588V / Clesse APS, válvulas de corte Giacomini y válvulas de seguridad RegO RS 3145. |
| [vaporizacion_forzada.md](file:///H:/Unidades%20compartidas/Practicas_Inst2/4_GLPs/Proyecto/Anotaciones/vaporizacion_forzada.md) | **Decisión** | Dimensionado e integración física de serpentín VIA 150 y armario VPC30C en el depósito principal LP46A, y guías para el plano CAD. |
| [vaporizacion_natural.md](file:///H:/Unidades%20compartidas/Practicas_Inst2/4_GLPs/Proyecto/Anotaciones/vaporizacion_natural.md) | **Cálculo** | Balance térmico de la batería mixta. Capacidad máxima de gasificación natural a $-5\text{ ºC}$ ($131,3\text{ kg/h}$), resultando en un déficit de $56,51\text{ kg/h}$. |

---

## 2. Mapeo de Requisitos de Alcance (`Proyecto/Alcance.md`)

Cada requisito estipulado en el documento de alcance del proyecto se asocia de forma directa con los apartados de la memoria LaTeX correspondientes:

1. **Caudal individual y total de cálculo:**
   - `2.4.7 Potencia térmica total de la instalación en KW.`
   - `3.2 CONSUMO Y AUTONOMÍA.`
2. **Autonomía de almacenamiento para 30 días:**
   - `2.4.5 Volumen en m³ de almacenamiento. Clasificación.`
   - `3.2 CONSUMO Y AUTONOMÍA.`
3. **Vaporización natural del depósito o conjunto de depósitos:**
   - `2.13.4 Equipo de vaporización.`
   - `3.3 VAPORIZACIÓN.`
4. **Cálculo del volumen del depósito y de sus características principales:**
   - `2.4.4 Tipo de instalación (aérea o enterrada).`
   - `2.4.5 Volumen en m³ de almacenamiento. Clasificación.`
   - `2.13.1 Depósitos.`
   - `3.2 CONSUMO Y AUTONOMÍA.`
5. **Cálculo de la conducción de distribución, incluyendo diámetros, presiones y pérdidas de carga:**
   - `2.13.2 Canalizaciones.`
   - `3.1 ÍNDICE DE ANEXOS.` (Anejo III - Pérdidas de carga y diámetros)
6. **Esquema de distribución, estación de almacenamiento y comprobación de distancias de seguridad:**
   - `2.11 DESCRIPCIÓN Y SISTEMA ELEGIDO.`
   - `2.12 CLASIFICACIÓN Y DISTANCIAS DE SEGURIDAD.`
   - `3.7 PROTECCIÓN CONTRA INCENDIOS.`
   - `PLANOS` (`plano_Esquema_instalacion.pdf`, `Plano_distancias_seguridad.pdf`)
7. **Elección de la ubicación de la estación de GLP con justificación técnica y reglamentaria:**
   - `2.6 EMPLAZAMIENTO DE LAS INSTALACIONES.`
   - `2.12 CLASIFICACIÓN Y DISTANCIAS DE SEGURIDAD.`
   - `PLANOS` (`situacion-emplazamiento.pdf`)

---

## 3. Matriz Operativa de Trazabilidad y Cobertura

La siguiente tabla presenta la trazabilidad total del proyecto, relacionando la jerarquía de secciones de la plantilla LaTeX (`Practica_GLPs_LaTeX/plantilla.tex`) con sus especificaciones Markdown, los requisitos de alcance cubiertos, las notas técnicas de anotación, los elementos visuales esperados y su estado actual de desarrollo.

| Sección LaTeX | Especificación MD Objetivo | Requisitos de Alcance Cubiertos | Archivos de Anotaciones Conectados (Categoría) | Figuras / Tablas / Resultados Esperados | Estado | Comentarios y Tareas Operativas |
| :--- | :--- | :--- | :--- | :--- | :--- | :--- |
| **PORTADA** | `Directo en LaTeX` | - | - | Membrete institucional de la ULE, título de la instalación, datos del Grupo G1-1. | `completado` | Rellenar autores y tutor en la portada de la plantilla. |
| **ÍNDICE GENERAL** | `Generado por LaTeX` | - | - | Estructura jerárquica canónica del documento. | `completado` | Automático mediante comandos `\tableofcontents`. |
| **2.1 IDENTIFICACIÓN.** | [datos-partida.md](file:///H:/Unidades%20compartidas/Practicas_Inst2/4_GLPs/Proyecto/Especificaciones/datos-partida.md) | - | [temperatura_diseno.md](file:///H:/Unidades%20compartidas/Practicas_Inst2/4_GLPs/Proyecto/Anotaciones/temperatura_diseno.md) (Evidencia) | Temperatura mínima de cálculo ($-5\text{ ºC}$), percentil de diseño ($99,6\%$). | `completado` | Indicar ubicación local y climatología asociada de León (Virgen del Camino). |
| **2.2 OBJETO.** | [intro.md](file:///H:/Unidades%20compartidas/Practicas_Inst2/4_GLPs/Proyecto/Especificaciones/intro.md) | - | [Alcance.md](file:///H:/Unidades%20compartidas/Practicas_Inst2/4_GLPs/Proyecto/Alcance.md) (Evidencia) | Justificación de la necesidad técnica de la planta. | `completado` | Definir el propósito de abastecimiento y la naturaleza industrial de los hornos. |
| **2.3 ANTECEDENTES.** | [intro.md](file:///H:/Unidades%20compartidas/Practicas_Inst2/4_GLPs/Proyecto/Especificaciones/intro.md) | - | [Alcance.md](file:///H:/Unidades%20compartidas/Practicas_Inst2/4_GLPs/Proyecto/Alcance.md) (Evidencia) | Alternativas energéticas, elección de propano comercial. | `completado` | Justificar el uso de propano frente a gas natural o combustibles líquidos. |
| **2.4 RESUMEN DE CARACTERÍSTICAS.** | - | - | - | - | `completado` | Sección contenedora que agrupa los siguientes subapartados (2.4.1 a 2.4.8). |
| **2.4.1 Titular de la instalación.** | [datos-partida.md](file:///H:/Unidades%20compartidas/Practicas_Inst2/4_GLPs/Proyecto/Especificaciones/datos-partida.md) | - | - | Datos fiscales y de propiedad de la planta industrial. | `completado` | Redactar datos representativos para el cliente industrial ficticio. |
| **2.4.2 Emplazamiento.** | [datos-partida.md](file:///H:/Unidades%20compartidas/Practicas_Inst2/4_GLPs/Proyecto/Especificaciones/datos-partida.md) | Requisito 7 (Ubicación) | - | Datos geográficos y referencia catastral. | `completado` | Indicar el polígono industrial y la referencia catastral verificada. |
| **2.4.3 Localidad.** | [datos-partida.md](file:///H:/Unidades%20compartidas/Practicas_Inst2/4_GLPs/Proyecto/Especificaciones/datos-partida.md) | - | - | Término municipal: León. | `completado` | Consolidar descripción del emplazamiento en León (Virgen del Camino). |
| **2.4.4 Tipo de instalación (aérea o enterrada).** | [deposito.md](file:///H:/Unidades%20compartidas/Practicas_Inst2/4_GLPs/Proyecto/Especificaciones/deposito.md) | Requisito 4 (Volumen depósito) | [seleccion_deposito.md](file:///H:/Unidades%20compartidas/Practicas_Inst2/4_GLPs/Proyecto/Anotaciones/seleccion_deposito.md) (Decisión) | Elección de tanques de superficie horizontales. | `completado` | Justificar por qué se eligen aéreos en lugar de enterrados o verticales. |
| **2.4.5 Volumen en m³ de almacenamiento. Clasificación.** | [deposito.md](file:///H:/Unidades%20compartidas/Practicas_Inst2/4_GLPs/Proyecto/Especificaciones/deposito.md), [autonomia.md](file:///H:/Unidades%20compartidas/Practicas_Inst2/4_GLPs/Proyecto/Especificaciones/autonomia.md) | Requisito 2 (Autonomía) y Requisito 4 (Volumen depósito) | [autonomia_30_dias.md](file:///H:/Unidades%20compartidas/Practicas_Inst2/4_GLPs/Proyecto/Anotaciones/autonomia_30_dias.md) (Cálculo), [calculo_volumen_deposito.md](file:///H:/Unidades%20compartidas/Practicas_Inst2/4_GLPs/Proyecto/Anotaciones/calculo_volumen_deposito.md) (Cálculo) | Capacidad geométrica total ($125,1 \text{ m}^3$), Categoría A-500. | `completado` | Justificar la fragmentación de volumen para no colisionar con distancias en parcela. |
| **2.4.6 Instalación receptora. Actividad que utiliza en GLP.** | [datos-partida.md](file:///H:/Unidades%20compartidas/Practicas_Inst2/4_GLPs/Proyecto/Especificaciones/datos-partida.md) | - | - | Suministro térmico a hornos industriales de secado, fusión y decapado. | `completado` | Describir el tipo de actividad fabril. |
| **2.4.7 Potencia térmica total de la instalación en KW.** | [demanda-consumo.md](file:///H:/Unidades%20compartidas/Practicas_Inst2/4_GLPs/Proyecto/Especificaciones/demanda-consumo.md) | Requisito 1 (Caudal de cálculo) | [caudales_consumidores.md](file:///H:/Unidades%20compartidas/Practicas_Inst2/4_GLPs/Proyecto/Anotaciones/caudales_consumidores.md) (Cálculo) | Tabla de demanda de consumidores C1-C6, potencia simultánea de $2.620 \text{ kW}$. | `completado` | Exponer la suma de potencias nominales de los 6 consumidores de G1-1. |
| **2.4.8 Presupuesto total.** | [presupuesto.md](file:///H:/Unidades%20compartidas/Practicas_Inst2/4_GLPs/Proyecto/Especificaciones/presupuesto.md) | - | [recopilacion_accesorios_costes_glp.md](file:///H:/Unidades%20compartidas/Practicas_Inst2/4_GLPs/Proyecto/Anotaciones/recopilacion_accesorios_costes_glp.md) (Evidencia) | Importe del presupuesto total de ejecución por contrata. | `completado` | Citar la cifra final consolidada de la estimación de costes. |
| **2.5 PROMOTOR DE LA INSTALACIÓN.** | [promotor-plazo-accesos.md](file:///H:/Unidades%20compartidas/Practicas_Inst2/4_GLPs/Proyecto/Especificaciones/promotor-plazo-accesos.md) | - | - | Identificación de los ingenieros proyectistas (Grupo G1-1) y tutor. | `completado` | Detallar los autores y promotor institucional (ULE). |
| **2.6 EMPLAZAMIENTO DE LAS INSTALACIONES.** | [datos-partida.md](file:///H:/Unidades%20compartidas/Practicas_Inst2/4_GLPs/Proyecto/Especificaciones/datos-partida.md) | Requisito 7 (Ubicación) | - | Linderos de parcela catastral en León. | `completado` | Detallar la ubicación geográfica exacta elegida dentro de la parcela catastral. |
| **2.7 REGLAMENTACIÓN Y NORMAS TÉCNICAS CONSIDERADAS.** | [datos-partida.md](file:///H:/Unidades%20compartidas/Practicas_Inst2/4_GLPs/Proyecto/Especificaciones/datos-partida.md) | Requisito 7 (Ubicación - justificación reglamentaria) | [criterios_normativos.md](file:///H:/Unidades%20compartidas/Practicas_Inst2/4_GLPs/Proyecto/Anotaciones/criterios_normativos.md) (Criterio Normativo) | Relación de normas UNE, directivas europeas (PED, ATEX) y reglamentos nacionales. | `completado` | Enumerar detalladamente las normas específicas (UNE 60250:2008, ITC-ICG 03, RD 919/2006). |
| **2.8 PLAZO DE EJECUCIÓN.** | [promotor-plazo-accesos.md](file:///H:/Unidades%20compartidas/Practicas_Inst2/4_GLPs/Proyecto/Especificaciones/promotor-plazo-accesos.md) | - | - | Plazo físico de implantación de la obra civil y puesta en servicio. | `completado` | Establecer y justificar un plazo razonable (ej. 3 meses) y hitos principales. |
| **2.9 CARACTERÍSTICAS DEL GAS SUMINISTRADO.** | [datos-partida.md](file:///H:/Unidades%20compartidas/Practicas_Inst2/4_GLPs/Proyecto/Especificaciones/datos-partida.md) | - | [temperatura_diseno.md](file:///H:/Unidades%20compartidas/Practicas_Inst2/4_GLPs/Proyecto/Anotaciones/temperatura_diseno.md) (Evidencia) | Tabla de especificaciones de propano comercial (densidad, PCS, tensiones de vapor). | `completado` | Definir parámetros de propano comercial y base térmica de cálculo ($13,95\text{ kWh/kg}$). |
| **2.10 ACCESOS.** | [promotor-plazo-accesos.md](file:///H:/Unidades%20compartidas/Practicas_Inst2/4_GLPs/Proyecto/Especificaciones/promotor-plazo-accesos.md) | Requisito 7 (Ubicación - accesos) | [criterios_normativos.md](file:///H:/Unidades%20compartidas/Practicas_Inst2/4_GLPs/Proyecto/Anotaciones/criterios_normativos.md) (Criterio Normativo) | Dimensionamiento vial para camiones articulados cisterna (radios, pendientes $<5\%$). | `completado` | Justificar la maniobra del camión cisterna en la estación. |
| **2.11 DESCRIPCIÓN Y SISTEMA ELEGIDO.** | [red-distribucion.md](file:///H:/Unidades%20compartidas/Practicas_Inst2/4_GLPs/Proyecto/Especificaciones/red-distribucion.md) | Requisito 6 (Esquema de distribución) | [trazado_red.md](file:///H:/Unidades%20compartidas/Practicas_Inst2/4_GLPs/Proyecto/Anotaciones/trazado_red.md) (Decisión) | Topología general de la red aérea, colectores comunes y regulación de primer salto. | `completado` | Resumen general de la arquitectura tecnológica adoptada para el almacenamiento y la red. |
| **2.12 CLASIFICACIÓN Y DISTANCIAS DE SEGURIDAD.** | [implantacion-seguridad.md](file:///H:/Unidades%20compartidas/Practicas_Inst2/4_GLPs/Proyecto/Especificaciones/implantacion-seguridad.md) | Requisito 6 (Distancias) y Requisito 7 (Ubicación) | [distancias_seguridad.md](file:///H:/Unidades%20compartidas/Practicas_Inst2/4_GLPs/Proyecto/Anotaciones/distancias_seguridad.md) (Criterio Normativo) | Tabla de distancias de seguridad A-500 a linderos, focos, cerramientos. Medidas reductoras. | `completado` | Justificar distancias de paso de orificios ($D_o$) y paredes ($D_p$) bajo UNE 60250. |
| **2.13 CARACTERÍSTICAS DE LOS EQUIPOS.** | - | - | - | - | `completado` | Sección contenedora que agrupa la descripción de componentes (2.13.1 a 2.13.7). |
| **2.13.1 Depósitos.** | [deposito.md](file:///H:/Unidades%20compartidas/Practicas_Inst2/4_GLPs/Proyecto/Especificaciones/deposito.md) | Requisito 4 (Características principales) | [seleccion_deposito.md](file:///H:/Unidades%20compartidas/Practicas_Inst2/4_GLPs/Proyecto/Anotaciones/seleccion_deposito.md) (Decisión), [pliego_condiciones_equipos_glp.md](file:///H:/Unidades%20compartidas/Practicas_Inst2/4_GLPs/Proyecto/Anotaciones/pliego_condiciones_equipos_glp.md) (Criterio Normativo) | Dimensiones de LP46A y LP26A, chapa de acero, recubrimiento anticorrosión, cunas. | `completado` | Describir constructivamente los depósitos, marcando la brida DN400 del "Modelo Especial". |
| **2.13.2 Canalizaciones.** | [red-distribucion.md](file:///H:/Unidades%20compartidas/Practicas_Inst2/4_GLPs/Proyecto/Especificaciones/red-distribucion.md) | Requisito 5 (Conducción de distribución) | [dimensionado_tuberias_glp.md](file:///H:/Unidades%20compartidas/Practicas_Inst2/4_GLPs/Proyecto/Anotaciones/dimensionado_tuberias_glp.md) (Cálculo) | Tubería de cobre UNE-EN 1057 en barra, diámetros exteriores y espesores. | `completado` | Describir el material, trazado aéreo protegido, y criterios de velocidad admisible ($\le 10\text{ m/s}$). |
| **2.13.3 Boca de carga.** | [equipos-auxiliares.md](file:///H:/Unidades%20compartidas/Practicas_Inst2/4_GLPs/Proyecto/Especificaciones/equipos-auxiliares.md) | Requisito 4 (Características principales) | [valvuleria_accesorios.md](file:///H:/Unidades%20compartidas/Practicas_Inst2/4_GLPs/Proyecto/Anotaciones/valvuleria_accesorios.md) (Decisión) | Tipo de acoplamiento rápido (RegO 7579C), doble válvula de retención y purga. | `completado` | Especificar las características de la boca de carga y el limitador de llenado. |
| **2.13.4 Equipo de vaporización.** | [vaporizacion.md](file:///H:/Unidades%20compartidas/Practicas_Inst2/4_GLPs/Proyecto/Especificaciones/vaporizacion.md) | Requisito 3 (Vaporización forzada) | [vaporizacion_forzada.md](file:///H:/Unidades%20compartidas/Practicas_Inst2/4_GLPs/Proyecto/Anotaciones/vaporizacion_forzada.md) (Decisión), [potencia_armario_calefaccion.md](file:///H:/Unidades%20compartidas/Practicas_Inst2/4_GLPs/Proyecto/Anotaciones/potencia_armario_calefaccion.md) (Cálculo) | Intercambiador VIA 150 y Armario VPC30C ($45\text{ kW}$ de caldera). Losa de hormigón. | `completado` | Especificar el funcionamiento del circuito cerrado de agua y la ubicación física en parcela. |
| **2.13.5 Equipos de regulación y medida.** | [equipos-auxiliares.md](file:///H:/Unidades%20compartidas/Practicas_Inst2/4_GLPs/Proyecto/Especificaciones/equipos-auxiliares.md) | Requisito 5 (Conducción - regulación) | [valvuleria_accesorios.md](file:///H:/Unidades%20compartidas/Practicas_Inst2/4_GLPs/Proyecto/Anotaciones/valvuleria_accesorios.md) (Decisión), [reporte_accesorios.md](file:///H:/Unidades%20compartidas/Practicas_Inst2/4_GLPs/Proyecto/Anotaciones/reporte_accesorios.md) (Evidencia) | Regulador primer salto RegO 1588V / Clesse APS, llaves de corte individuales. | `completado` | Definir las características de los armarios de regulación y contadores si los hubiera. |
| **2.13.6 Equipo de trasvase.** | [equipos-auxiliares.md](file:///H:/Unidades%20compartidas/Practicas_Inst2/4_GLPs/Proyecto/Especificaciones/equipos-auxiliares.md) | - | - | Justificación de no requerirse bomba de trasvase activo en consumo simple. | `completado` | Declarar formalmente en especificaciones que no aplica trasvase para esta tipología. |
| **2.13.7 Válvulas de seguridad.** | [equipos-auxiliares.md](file:///H:/Unidades%20compartidas/Practicas_Inst2/4_GLPs/Proyecto/Especificaciones/equipos-auxiliares.md) | Requisito 4 (Características principales) | [valvuleria_accesorios.md](file:///H:/Unidades%20compartidas/Practicas_Inst2/4_GLPs/Proyecto/Anotaciones/valvuleria_accesorios.md) (Decisión) | Dos unidades RegO RS 3145 por depósito, tarado de apertura a $20\text{ bar}$. | `completado` | Describir el modelo, su acoplamiento CD45 y justificación comercial. |
| **2.14 INSTALACIÓN ELÉCTRICA.** | [instalaciones-auxiliares.md](file:///H:/Unidades%20compartidas/Practicas_Inst2/4_GLPs/Proyecto/Especificaciones/instalaciones-auxiliares.md) | Requisito 3 (Vaporización forzada - parte eléctrica) | [vaporizacion_forzada.md](file:///H:/Unidades%20compartidas/Practicas_Inst2/4_GLPs/Proyecto/Anotaciones/vaporizacion_forzada.md) (Decisión) | Acometida para cuadro de control VPC30C, clasificación de áreas ATEX (Zonas 1, 2). | `completado` | Crear especificación para justificar el alumbrado de la estación y canalizaciones eléctricas. |
| **2.15 INSTALACIONES DE PROTECCIÓN CONTRAINCENDIOS.** | [instalaciones-auxiliares.md](file:///H:/Unidades%20compartidas/Practicas_Inst2/4_GLPs/Proyecto/Especificaciones/instalaciones-auxiliares.md) | Requisito 6 (Esquema y distancias - PCI) | [distancias_seguridad.md](file:///H:/Unidades%20compartidas/Practicas_Inst2/4_GLPs/Proyecto/Anotaciones/distancias_seguridad.md) (Criterio Normativo) | Red de pulverización de agua fría, extintores portátiles de polvo seco (21A-113B). | `completado` | Crear la especificación que describa el sistema activo de extinción y extintores del recinto. |
| **2.16 PUESTA A TIERRA.** | [instalaciones-auxiliares.md](file:///H:/Unidades%20compartidas/Practicas_Inst2/4_GLPs/Proyecto/Especificaciones/instalaciones-auxiliares.md) | Requisito 6 (Esquema y distancias - puesta a tierra) | [criterios_normativos.md](file:///H:/Unidades%20compartidas/Practicas_Inst2/4_GLPs/Proyecto/Anotaciones/criterios_normativos.md) (Criterio Normativo) | Picas de cobre y conductores desnudos para depósitos y tuberías. Resistencia $< 20\ \Omega$. | `completado` | Especificar las características de las picas, conexiones de equipotencialidad y normativa. |
| **3.1 ÍNDICE DE ANEXOS.** | [anejos.md](file:///H:/Unidades%20compartidas/Practicas_Inst2/4_GLPs/Proyecto/Especificaciones/anejos.md) | - | - | Estructura de anejos en el documento final. | `completado` | Definir la inclusión de la memoria hidráulica como Anejo III en el documento LaTeX. |
| **3.2 CONSUMO Y AUTONOMÍA.** | [autonomia.md](file:///H:/Unidades%20compartidas/Practicas_Inst2/4_GLPs/Proyecto/Especificaciones/autonomia.md), [demanda-consumo.md](file:///H:/Unidades%20compartidas/Practicas_Inst2/4_GLPs/Proyecto/Especificaciones/demanda-consumo.md) | Requisito 1 (Caudal) y Requisito 2 (Autonomía) | [autonomia_30_dias.md](file:///H:/Unidades%20compartidas/Practicas_Inst2/4_GLPs/Proyecto/Anotaciones/autonomia_30_dias.md) (Cálculo), [calculo_volumen_deposito.md](file:///H:/Unidades%20compartidas/Practicas_Inst2/4_GLPs/Proyecto/Anotaciones/calculo_volumen_deposito.md) (Cálculo), [caudales_consumidores.md](file:///H:/Unidades%20compartidas/Practicas_Inst2/4_GLPs/Proyecto/Anotaciones/caudales_consumidores.md) (Cálculo) | Ecuaciones matemáticas y cálculos detallados de consumos, volumen útil y geométrico. | `completado` | Desarrollo del cálculo paso a paso justificando la batería de 125.100 litros. |
| **3.3 VAPORIZACIÓN.** | [vaporizacion.md](file:///H:/Unidades%20compartidas/Practicas_Inst2/4_GLPs/Proyecto/Especificaciones/vaporizacion.md) | Requisito 3 (Vaporización natural) | [vaporizacion_natural.md](file:///H:/Unidades%20compartidas/Practicas_Inst2/4_GLPs/Proyecto/Anotaciones/vaporizacion_natural.md) (Cálculo), [vaporizacion_forzada.md](file:///H:/Unidades%20compartidas/Practicas_Inst2/4_GLPs/Proyecto/Anotaciones/vaporizacion_forzada.md) (Decisión), [potencia_armario_calefaccion.md](file:///H:/Unidades%20compartidas/Practicas_Inst2/4_GLPs/Proyecto/Anotaciones/potencia_armario_calefaccion.md) (Cálculo) | Ecuaciones de balance térmico, determinación de déficit ($56,51\text{ kg/h}$) y potencia caldera. | `completado` | Justificar la potencia del armario de calefacción ($17,5\text{ kW}$ mínima exigida, $45\text{ kW}$ adoptada). |
| **3.4 VÁLVULAS DE SEGURIDAD.** | [calculos-auxiliares.md](file:///H:/Unidades%20compartidas/Practicas_Inst2/4_GLPs/Proyecto/Especificaciones/calculos-auxiliares.md) | Requisito 4 (Características principales) | [valvuleria_accesorios.md](file:///H:/Unidades%20compartidas/Practicas_Inst2/4_GLPs/Proyecto/Anotaciones/valvuleria_accesorios.md) (Decisión) | Cálculo de caudal de descarga mínimo requerido frente a incendio y tarado a 20 bar. | `completado` | Escribir el desarrollo matemático de descarga de aire equivalente según UNE 60250. |
| **3.5 PUNTO MÁXIMO LLENADO: LONGITUD TUBO SONDA.** | [calculos-auxiliares.md](file:///H:/Unidades%20compartidas/Practicas_Inst2/4_GLPs/Proyecto/Especificaciones/calculos-auxiliares.md) | Requisito 4 (Características principales) | - | Cálculo de la cota física de la sonda para limitar el llenado al $85\%$. | `completado` | Escribir las ecuaciones geométricas para determinar la longitud de la sonda. |
| **3.6 PROTECCIÓN CATÓDICA.** | [calculos-auxiliares.md](file:///H:/Unidades%20compartidas/Practicas_Inst2/4_GLPs/Proyecto/Especificaciones/calculos-auxiliares.md) | Requisito 4 (Características principales) | - | Justificación de la inaplicabilidad de protección catódica por ser tanques aéreos. | `completado` | Redactar la nota técnica donde se descarte por no haber tuberías ni tanques enterrados. |
| **3.7 PROTECCIÓN CONTRA INCENDIOS.** | [calculos-auxiliares.md](file:///H:/Unidades%20compartidas/Practicas_Inst2/4_GLPs/Proyecto/Especificaciones/calculos-auxiliares.md) | Requisito 6 (Esquema y distancias - PCI) | [distancias_seguridad.md](file:///H:/Unidades%20compartidas/Practicas_Inst2/4_GLPs/Proyecto/Anotaciones/distancias_seguridad.md) (Criterio Normativo) | Dimensionamiento del caudal de agua de refrigeración ($3\ \text{l/min}\cdot\text{m}^2$) para los depósitos. | `completado` | Calcular el caudal de agua total y el número de rociadores necesarios para la batería. |
| **4.1 ÍNDICE DE PRESUPUESTO.** | [presupuesto.md](file:///H:/Unidades%20compartidas/Practicas_Inst2/4_GLPs/Proyecto/Especificaciones/presupuesto.md) | - | - | Estructura de capítulos del presupuesto. | `completado` | Crear la especificación que organice las partidas de obra. |
| **4.2 CUADRO DE PRECIOS Nº 1.** | [presupuesto.md](file:///H:/Unidades%20compartidas/Practicas_Inst2/4_GLPs/Proyecto/Especificaciones/presupuesto.md) | - | [recopilacion_accesorios_costes_glp.md](file:///H:/Unidades%20compartidas/Practicas_Inst2/4_GLPs/Proyecto/Anotaciones/recopilacion_accesorios_costes_glp.md) (Evidencia) | Precios unitarios de materiales y equipos (tubería, válvulas, reguladores, caldera, tanques). | `completado` | Definir las tablas de precios de compra de materiales principales en euros. |
| **4.3 CUADRO DE PRECIOS Nº 2.** | [presupuesto.md](file:///H:/Unidades%20compartidas/Practicas_Inst2/4_GLPs/Proyecto/Especificaciones/presupuesto.md) | - | [recopilacion_accesorios_costes_glp.md](file:///H:/Unidades%20compartidas/Practicas_Inst2/4_GLPs/Proyecto/Anotaciones/recopilacion_accesorios_costes_glp.md) (Evidencia) | Precios unitarios descompuestos que integren mano de obra e imprevistos. | `completado` | Definir la estimación del coste de instalación y mano de obra por tramos. |
| **4.4 MEDICIONES.** | [presupuesto.md](file:///H:/Unidades%20compartidas/Practicas_Inst2/4_GLPs/Proyecto/Especificaciones/presupuesto.md) | - | [recopilacion_accesorios_costes_glp.md](file:///H:/Unidades%20compartidas/Practicas_Inst2/4_GLPs/Proyecto/Anotaciones/recopilacion_accesorios_costes_glp.md) (Evidencia), [reporte_accesorios.md](file:///H:/Unidades%20compartidas/Practicas_Inst2/4_GLPs/Proyecto/Anotaciones/reporte_accesorios.md) (Evidencia) | Tabla de mediciones detalladas (metros lineales de cobre y recuento de codos y válvulas). | `completado` | Importar el recuento y longitudes reales obtenidas de los archivos de anotaciones. |
| **4.5 PRESUPUESTO.** | [presupuesto.md](file:///H:/Unidades%20compartidas/Practicas_Inst2/4_GLPs/Proyecto/Especificaciones/presupuesto.md) | - | [recopilacion_accesorios_costes_glp.md](file:///H:/Unidades%20compartidas/Practicas_Inst2/4_GLPs/Proyecto/Anotaciones/recopilacion_accesorios_costes_glp.md) (Evidencia) | Presupuesto por capítulos, PEM, Presupuesto de Contrata y Liquidación Final. | `completado` | Consolidar el coste total estimado de la instalación. |
| **PLANOS** | [anejos.md](file:///H:/Unidades%20compartidas/Practicas_Inst2/4_GLPs/Proyecto/Especificaciones/anejos.md) | Requisito 6 (Esquema y distancias) y Requisito 7 (Ubicación de la estación) | [vaporizacion_forzada.md](file:///H:/Unidades%20compartidas/Practicas_Inst2/4_GLPs/Proyecto/Anotaciones/vaporizacion_forzada.md) (Decisión), [distancias_seguridad.md](file:///H:/Unidades%20compartidas/Practicas_Inst2/4_GLPs/Proyecto/Anotaciones/distancias_seguridad.md) (Criterio Normativo) | Inserción de planos PDF (`situacion-emplazamiento.pdf`, `Plano_distancias_seguridad.pdf`, `plano_Esquema_instalacion.pdf`). | `completado` | Definir la inserción de planos mediante el paquete LaTeX `pdfpages` respetando la rotación. |
| **BIBLIOGRAFÍA** | `Proyecto/Planificacion/mapa_citas.md` | - | [criterios_normativos.md](file:///H:/Unidades%20compartidas/Practicas_Inst2/4_GLPs/Proyecto/Anotaciones/criterios_normativos.md) (Criterio Normativo) | Referencias bibliográficas formateadas. | `completado` | Asegurar la correspondencia de las claves de citación en el documento final. |
| **ANEXOS / APÉNDICE** | [anejos.md](file:///H:/Unidades%20compartidas/Practicas_Inst2/4_GLPs/Proyecto/Especificaciones/anejos.md) | - | - | Portadas de anexos técnicos. | `completado` | Consolidar la sección de anejos en el documento compilado final. |

---

## 4. Notas Adicionales sobre la Planificación de Brechas

Para la resolución de las brechas documentales identificadas (marcadas con estado `completado` en la matriz), se estructuró el trabajo en la creación de los siguientes archivos Markdown bajo `Proyecto/Especificaciones/` (todos creados y normalizados):

1. **`promotor-plazo-accesos.md`:** Cubre las secciones LaTeX `2.5` (Promotor), `2.8` (Plazo) y `2.10` (Accesos).
2. **`equipos-auxiliares.md`:** Cubre las secciones LaTeX `2.13.3` (Boca de carga), `2.13.5` (Regulación y medida), `2.13.6` (Trasvase) y `2.13.7` (Válvulas de seguridad).
3. **`instalaciones-auxiliares.md`:** Cubre las secciones LaTeX `2.14` (Instalación eléctrica), `2.15` (Protección contraincendios) y `2.16` (Puesta a tierra).
4. **`calculos-auxiliares.md`:** Cubre las secciones LaTeX `3.4` (Cálculo válvulas de seguridad), `3.5` (Cálculo tubo sonda), `3.6` (Protección catódica) y `3.7` (Cálculo protección contra incendios).
5. **`presupuesto.md`:** Cubre todo el bloque de presupuesto (secciones `4.1` a `4.5`).
