Aleesca/Practica_GLP/Proyecto/Planificacion/manifiesto_figuras_memoria.md

# Manifiesto de figuras y planos

## Inventario base

| Artefacto | Tipo | Apartado | Uso | Estado |
| --- | --- | --- | --- | --- |
| `Proyecto/image.png` | Imagen base del enunciado | `Proyecto/Alcance.md` | Apoyo visual del alcance actual | `existente` |
| `01_Planos/instalacion_GLP.dwg` | Plano CAD | `2.2.5`, `2.2.6`, `6` | Soporte de trazado e implantacion | `existente` |
| Plano general de implantacion exportado | Plano derivado | `6` | Anejo I | `pendiente` |
| Esquema de distribucion | Esquema derivado | `2.2.5`, `6` | Explicacion de la red | `pendiente` |
| Cuadro de distancias de seguridad | Tabla/figura derivada | `2.2.6`, `6` | Verificacion reglamentaria | `pendiente` |
