Aleesca/Practica_GLP/Proyecto/Planificacion/manifiesto_tablas_metodologia.md

# Manifiesto de tablas de metodologia

## Inventario base

| Apartado | Tabla esperada | Archivo objetivo | Estado |
| --- | --- | --- | --- |
| `2.1` | Datos de partida y simbolos | `Proyecto/Especificaciones/datos-partida.md` | `pendiente` |
| `2.2.1` | Consumidores, demanda y caudal de calculo | `Proyecto/Especificaciones/demanda-consumo.md` | `pendiente` |
| `2.2.2` | Consumo diario y autonomia | `Proyecto/Especificaciones/autonomia.md` | `pendiente` |
| `2.2.3` | Demanda frente a vaporizacion natural | `Proyecto/Especificaciones/vaporizacion.md` | `pendiente` |
| `2.2.4` | Alternativas y seleccion de deposito | `Proyecto/Especificaciones/deposito.md` | `pendiente` |
| `2.2.5` | Tramos, diametros, perdidas y presiones | `Proyecto/Especificaciones/red-distribucion.md` | `pendiente` |
| `2.2.6` | Distancias reglamentarias verificadas | `Proyecto/Especificaciones/implantacion-seguridad.md` | `pendiente` |
