Aleesca/Practica_GLP/Proyecto/Planificacion/mapa_citas.md

# Mapa de Citas y Bibliografia Operativa

Este documento cierra la trazabilidad `fuente externa -> clave bibliografica -> seccion de memoria` para la bibliografia operativa del proyecto.

## Nucleo bibliografico activo

| Fuente externa | Clave | Secciones donde debe citarse | Uso principal |
| :--- | :--- | :--- | :--- |
| `00_Info_proporcionada/TAREA 3 calculo instalación GLP.pdf` | `ule-glp-enunciado` | `1`, `2.1`, `2.2.1` a `2.2.6` | Enunciado y alcance del caso |
| `00_Info_proporcionada/DATOS GRUPOS-2026.xlsx` | `ule-glp-datos-grupos` | `2.1`, `2.2.1`, `2.2.2` | Datos de consumidores y grupo |
| `00_Info_proporcionada/Modelo proyecto depositos fijos GLP.doc` | `ule-glp-modelo-proyecto` | `1`, `2`, `6` | Referencia de estructura y entregable esperado |
| `01_Planos/instalacion_GLP.dwg` | `plano-glp-base` | `2.2.5`, `2.2.6`, `6` | Trazado, distancias y soporte grafico |
| `.agents/skills/doc_tecnica_glp/references/formulario.md` | `glp-formulario-base` | `2.1`, `2.2.1` a `2.2.6` | Formulario y criterios base de calculo |
| `.agents/skills/doc_tecnica_glp/references/doc_map.md` | `glp-doc-map` | `2`, `5` | Mapa de fuentes tecnicas del proyecto |
| `.agents/skills/doc_tecnica_glp/references/datos_grupo_G1-1.md` | `glp-g11-datos-normalizados` | `2.1`, `2.2.1`, `2.2.2` | Datos del grupo en formato operativo |
| `ZZ_Normativa/normativa_requerida.md` | `glp-normativa-indice` | `2.1`, `2.2.4`, `2.2.6`, `5` | Indice y seleccion normativa del proyecto |

## Convencion minima de citacion

- Cada seleccion de equipo debe citar su catalogo o guia tecnica.
- Cada criterio normativo no obvio debe enlazarse con su documento de referencia.
- Cada tabla derivada de datos del grupo debe citar su fuente original o su version normalizada operativa.
- Las figuras y tablas auxiliares heredaran la cita de su fuente madre; no crean una clave independiente salvo necesidad expresa.
