Aleesca/Practica_GLP/Proyecto/skills/doc_tecnica_glp/skill.md

---
name: doc_tecnica_glp
description: "Espejo temporal de la skill tecnica de GLP. No debe gobernar el sistema activo."
---

# Espejo temporal: Documentacion Tecnica de GLP

Este directorio replica la estructura de `.agents/skills/doc_tecnica_glp/` como apoyo documental. La ubicacion operativa real permanece en `.agents/skills/doc_tecnica_glp/`.
