Aleesca/Practica_GLP/.agents/skills/doc_tecnica_glp/references/datos_grupo_G1-1.md

# Datos normalizados del grupo G1-1

## Datos comunes

- Zona climatica de referencia: Leon.
- Temperatura exterior de calculo: pendiente de fijar con referencia tecnica valida.
- Parcela catastral: `8638004TN8183N`.

## Consumidores

| Consumidor | Potencia de calculo | Horas de funcionamiento |
| --- | ---: | ---: |
| Horno secado 1 | 60 kW | 12 h/d |
| Horno secado 2 | 60 kW | 12 h/d |
| Caldera vapor | 500 kW | 10 h/d |
| Caldera agua caliente | 300 kW | 8 h/d |
| Horno fusion | 700 kW | 4 h/d |
| Horno decapado | 1000 kW | 6 h/d |

## Observaciones

- Las distancias exactas de red y seguridad deben medirse sobre el plano y la parcela.
- Este documento normaliza la informacion de `Proyecto/Datos.md` para uso operativo de skills.
