Aleesca/Practica_GLP/Proyecto/skills/doc_tecnica_glp/references/datos.md

# Espejo temporal de datos normalizados del grupo G1-1

La fuente operativa real de este contenido es `.agents/skills/doc_tecnica_glp/references/datos_grupo_G1-1.md`.
