Aleesca/Practica_GLP/Proyecto/skills/doc_tecnica_glp/references/doc_map.md

# Espejo temporal del mapa de documentacion tecnica GLP

La fuente operativa real de este contenido es `.agents/skills/doc_tecnica_glp/references/doc_map.md`.
