Aleesca/Practica_GLP/00_Info_proporcionada/Teoria/3_Depositos_GLP-II.pdf

Universidad de León

# BLOQUE V.GLP

## Depósitos GLP-2

Alberto España Carrete

Escuela de Ingenierías Industrial Informática y Aeroespacial

Alberto España Carrete | BLOQUE V.GLP | 1 / 105

# NOMOGRAMAS

### 1.3.7.3 Nomograma para GLP en fase líquida

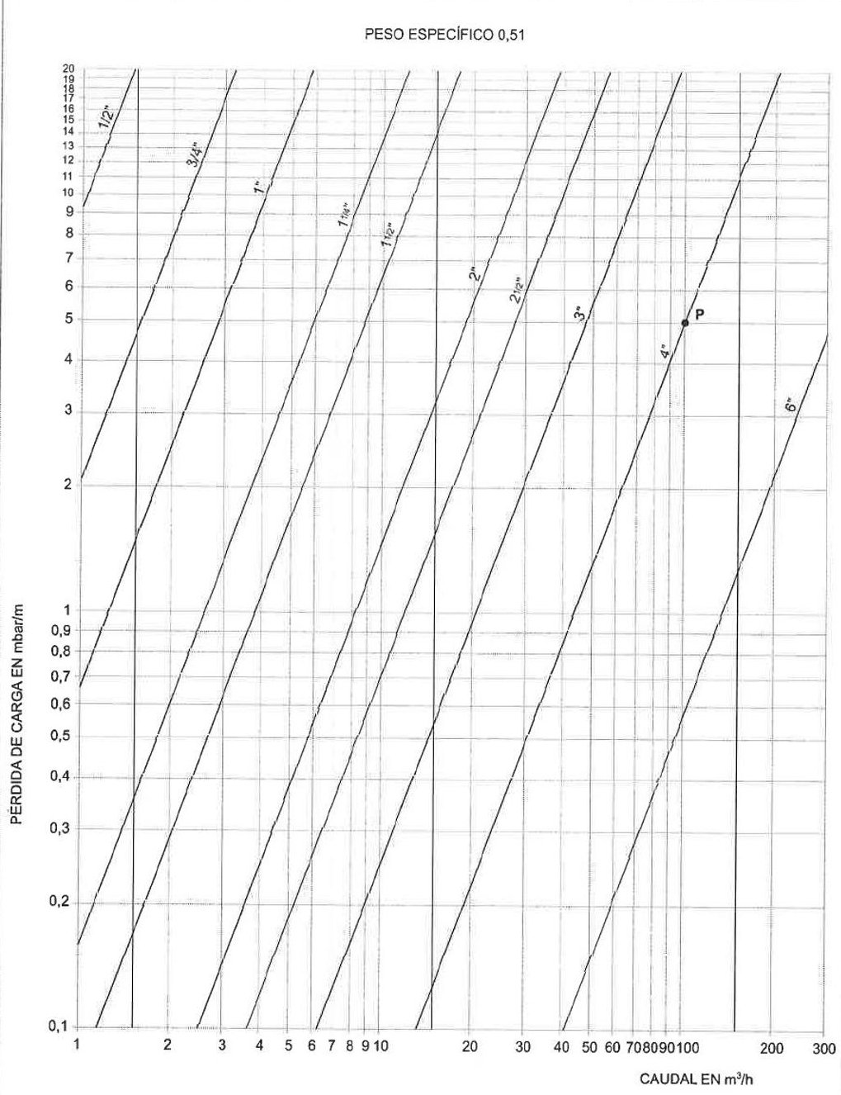
[picture p26: figure]

Ejemplo de lectura: Para un caudal de 100 m³/h y una tubería de 4 pulgadas (4”), la pérdida de carga es de 5 mbar/m (por metro de conducción).

### 1.3.7.4 Nomograma para GLP en instalaciones de botellas de propano con

presión inicial de 0,8 bar y presión final de 0,6 bar

Tratándose de instalaciones de botellas en caseta exterior, en donde el inversor automático tiene una presión de reserva de 0,8 bar y el segundo regulador tiene una presión mínima de 0,6 bar.

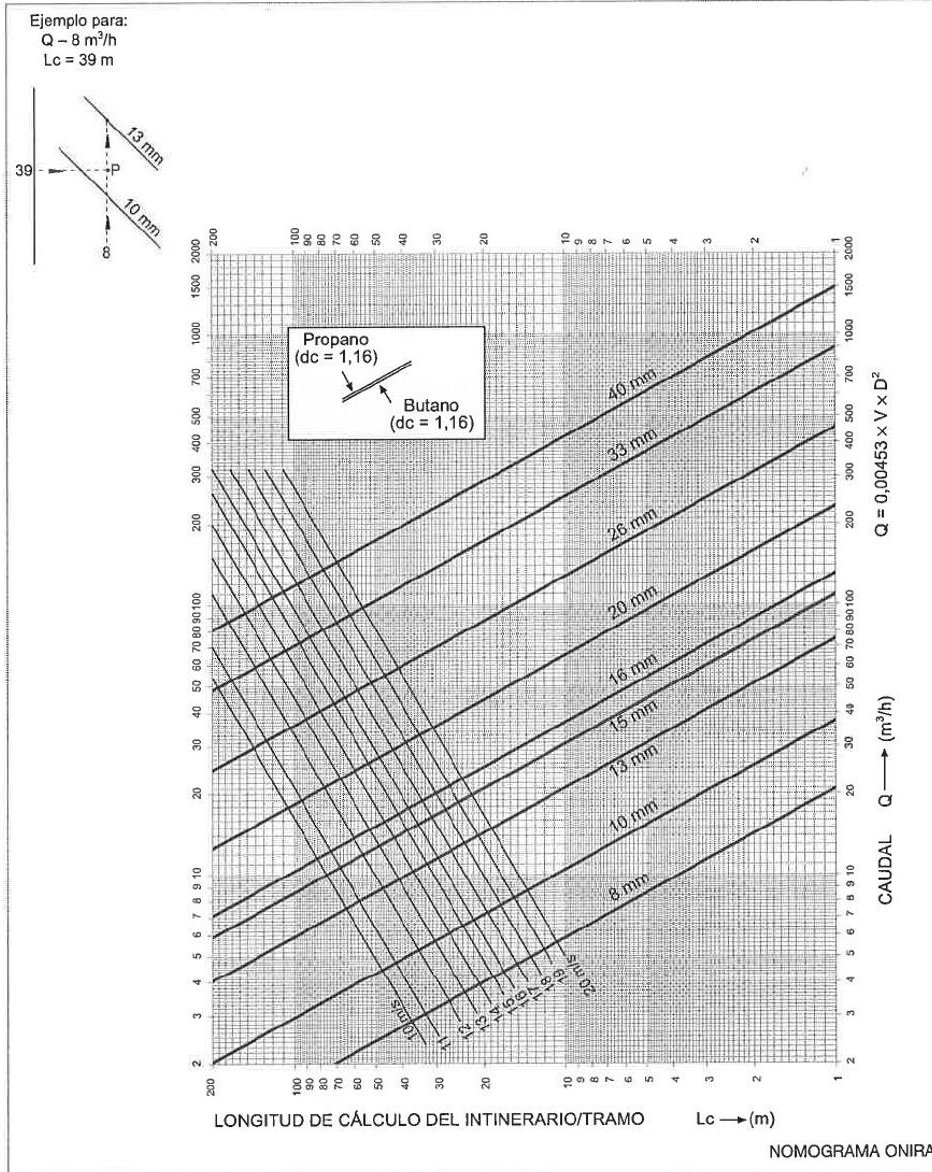
[picture p27: figure]

Ejemplo de cálculo: Sea un tramo Lc = 39 m y Q = 8 m³/h. En el punto A (tubo teórico < 13 mm) → se elige el inmediato superior: 13 mm. Con el tubo de 13 mm se puede atender un tramo de hasta 54 m de longitud de cálculo.

TABLAS PARA OBTENCION DE DI ´ | AMETROS (I) ´

### 1.3.7.5 Tablas para la obtención de diámetros interiores (BP)

Tablas para obtener los diámetros interiores de conducciones de butano y propano a BP. Se deberán aplicar solo en tramos simples (los que empiezan en el regulador y terminan en el aparato de consumo).

BUTANO BP: 28 mbar
Lc\Q | 1 | 2 | 3 | 4 | 5 | 7 | 9 | 11 | 14 | 18 | 20
2 | 10 | 15 | 15 | 20 | 20 | 20 | 25 | 25 | 30 | 30 | 30
4 | 15 | 15 | 20 | 20 | 20 | 25 | 25 | 30 | 30 | 30 | 40
6 | 15 | 20 | 20 | 20 | 25 | 25 | 30 | 30 | 30 | 40 | 40
8 | 15 | 20 | 20 | 25 | 25 | 30 | 30 | 40 | 40 | 40 | 40
10 | 15 | 20 | 20 | 25 | 25 | 30 | 30 | 40 | 40 | 40 | 50
15 | 15 | 20 | 25 | 25 | 30 | 30 | 40 | 40 | 40 | 50 | 50
20 | 20 | 20 | 25 | 30 | 30 | 40 | 40 | 40 | 50 | 50 | 50
25 | 20 | 25 | 25 | 30 | 30 | 40 | 40 | 40 | 50 | 50 | 50
30 | 20 | 25 | 25 | 30 | 40 | 40 | 40 | 50 | 50 | 50 | 65
35 | 20 | 25 | 30 | 30 | 40 | 40 | 40 | 50 | 50 | 65 | 65

PROPANO BP: 37 mbar
Lc\Q | 1 | 2 | 3 | 4 | 5 | 7 | 9 | 11 | 14 | 18 | 20
2 | 10 | 15 | 15 | 15 | 20 | 20 | 20 | 25 | 25 | 30 | 30
4 | 10 | 15 | 15 | 20 | 20 | 25 | 25 | 25 | 30 | 30 | 40
6 | 15 | 15 | 20 | 20 | 20 | 25 | 25 | 30 | 30 | 40 | 40
8 | 15 | 15 | 20 | 20 | 25 | 25 | 30 | 30 | 40 | 40 | 40
10 | 15 | 20 | 20 | 20 | 25 | 25 | 30 | 30 | 40 | 40 | 40
15 | 15 | 20 | 20 | 25 | 25 | 30 | 30 | 40 | 40 | 40 | 40
20 | 15 | 20 | 25 | 25 | 25 | 30 | 40 | 40 | 40 | 50 | 50
25 | 15 | 20 | 25 | 25 | 30 | 30 | 40 | 40 | 40 | 50 | 50
30 | 20 | 20 | 25 | 30 | 30 | 40 | 40 | 40 | 50 | 50 | 50
40 | 20 | 25 | 25 | 30 | 30 | 40 | 40 | 50 | 50 | 50 | 50

TABLAS PARA OBTENCION DE DI ´ | AMETROS (II) ´

Ejemplo de lectura: Se trata de una instalación de propano a 37 mbar. La longitud de cálculo de la conducción es de 9 m. El caudal es de 4, 6 m³/h. En la columna de longitudes se elige la línea de 10 m y en la de caudales se elige 5 m³/h. El tubo a seleccionar es el de 25 mm.

PROPANO BP: 50 mbar

Lc\Q | 1 | 2 | 3 | 4 | 5 | 7 | 9 | 11 | 14 | 18 | 20
2 | 10 | 15 | 15 | 15 | 20 | 20 | 20 | 25 | 25 | 25 | 30
4 | 10 | 15 | 15 | 20 | 20 | 20 | 25 | 25 | 30 | 30 | 30
6 | 15 | 15 | 20 | 20 | 20 | 25 | 25 | 30 | 30 | 40 | 40
8 | 15 | 15 | 20 | 20 | 25 | 25 | 30 | 30 | 30 | 40 | 40
10 | 15 | 20 | 20 | 20 | 25 | 25 | 30 | 30 | 40 | 40 | 40
15 | 15 | 20 | 20 | 25 | 25 | 30 | 30 | 40 | 40 | 40 | 40
20 | 15 | 20 | 25 | 25 | 25 | 30 | 30 | 40 | 40 | 40 | 50
25 | 15 | 20 | 25 | 25 | 30 | 30 | 40 | 40 | 40 | 50 | 50
30 | 15 | 20 | 25 | 25 | 30 | 40 | 40 | 40 | 40 | 50 | 50
35 | 20 | 20 | 25 | 30 | 30 | 40 | 40 | 40 | 50 | 50 | 50

CALCULO DE LA VAPORIZACI ´ | ON´

### 1.4 Cálculos de vaporización. Fórmulas y tablas

Los GLP se transportan y almacenan en recipientes, en estado líquido, pues en este estado ocupan un volumen unas 250 veces menor que en el gaseoso. En los recipientes, la fase líquida ocupa la parte inferior y el vapor, la superior a modo de burbuja, coexistiendo en equilibrio de presiones.
Como el consumo de GLP se hace, en general, en estado gaseoso, es necesario que los GLP pasen al estado de vapor antes de que lleguen al aparato. La vaporización puede ser natural o forzada:
1 | Vaporización natural: Cuando el gas sale directamente del recipiente que lo contiene, al abrir la llave que éste lleva en su parte superior.
2 | Vaporización forzada: Se produce cuando se calienta de forma artificial la fase líquida para provocar la vaporización. La vaporización forzada puede ser necesaria en algunos casos: Cuando el caudal de gas requerido en la instalación es superior al que se puede obtener con vaporización natural. Cuando las temperaturas ambientales son muy bajas, lo que impide que se vaporice lo suficiente. Cuando se requiere una mezcla constante del GLP, ya que en la vaporización natural se provoca un cierto enriquecimiento de las fracciones pesadas (C4) en la parte que va quedando en el depósito.

CALCULO DE LA VAPORIZACI ´ | ON´

Vaporización natural. En un depósito coexisten como se ha dicho, las dos fases o estados, esto es, líquido y vapor. Cuando del depósito vamos extrayendo gas para su consumo, se va reduciendo la presión de la fase vapor rompiéndose el equilibrio entre las dos fases. Como consecuencia de ello, se produce la vaporización natural de la base líquida para tender a recuperar el equilibrio perdido.
La presión de equilibrio es la llamada tensión de vapor, expresada en bar abs., por debajo de la cual el líquido se evapora (al realizarse una toma o al enfriarse) y por encima, el gas se condensa y se vuelve líquido (al calentarse o aumentar la presión). La tensión de vapor varía directamente con la temperatura a la que se encuentra el gas.
Para que se produzca la vaporización del líquido se necesita calor. A ese calor se le llama calor latente de vaporización (CLV).
La vaporización natural del GLP en el recipiente se produce primero absorbiendo calor del propio líquido y del exterior después, a través de las paredes del propio envase y precisamente de las paredes mojadas por el líquido. Al enfriarse el líquido, éste roba calor a las paredes que moja.
Realizándose una toma de gas moderada, el líquido mantiene su temperatura pues todo el calor necesario para la vaporización se va tomando del exterior. En el caso de que se solicitara del recipiente un caudal excesivo, el enfriamiento del líquido no podrá ser compensado por el calor procedente del exterior que resultará insuficiente. Si la toma de gas es de larga duración, la fase líquida puede enfriarse tanto que la presión del gas que salga del recipiente, resulte inferior a la presión mínima del regulador situado a la salida del mismo, y como consecuencia de ello se producirá un mal funcionamiento de la instalación.

LA VAPORIZACION NATURAL DEPENDE DE: ´

La superficie exterior del depósito, aumentando a mayor superficie.

La superficie mojada por el líquido, aumentando a mayor superficie.

CALCULO DE LA VAPORIZACI ´ | ON´

La temperatura exterior, aumentando con esta.

La temperatura del GLP, aumentando a mayor temperatura.

El tipo de GLP utilizado y la mezcla comercial que usemos.

A igualdad de capacidad, los depósitos de menor diámetro vaporizan más que los mayores porque con un mismo resto de gas, la superficie mojada es mayor.
La vaporización se ve afectada también por el tipo de depósito. Los depósitos enterrados absorben el calor de la tierra que los rodea que suele estar más caliente en invierno que el aire ambiental, pero en cambio, cuando enfrían la tierra forman hielo y aíslan el depósito dificultando la vaporización.
FORMULAS DE VAPORIZACI ´ | ON NATURAL ´
Para realizar los cálculos de vaporización natural, se ha de tener en cuenta si el calor de vaporización se extrae mayoritariamente del propio gas licuado o del exterior. Tratándose de depósitos, se considera el segundo caso mencionado (el calor se extrae mayoritariamente del exterior) porque las tomas de gas son de larga duración.
Para determinar el caudal que un depósito puede vaporizar de forma natural, se utiliza la siguiente fórmula:

Q = P · S · K

(Te − Tg)
CLV

donde:
| Q caudal másico de vaporización en kg/h.
| P Porcentaje de superficie del depósito en contacto con el líquido mojada. Para un 20 % de llenado se toma: a = 0,336 y para un 30 % vale 0,397.

CALCULO DE LA VAPORIZACI ´ | ON´

S Superficie del depósito en m²

K Coeficiente de transmisión de calor a través de las paredes del depósito. Depende de la humedad relativa ambiental y del viento. Para situación normal y viento en calma se obtiene un valor de K = 0,014 kW/m²

◦C. Ahora bien,
como valor promedio de diferentes situaciones se toma para depósitos aéreos K = 0,0116 kW/m²

◦C y para depósitos
enterrados se toma K = 0,0086 kW/m²

◦C.

Te Temperatura exterior mínima media prevista, del ambiente en el que está instalado el depósito. (5◦C para depósitos enterrados).

Tg Temperatura de equilibrio líquido-gas del gas en el interior del depósito. Depende de la temperatura de vaporización que se corresponde con la presión de servicio de la red. Se han tomado los valores incluidos en la cabecera de las tablas.
CLV Calor latente de vaporización del propano. Se toma un valor de 0,11 kWh/kg (94 kcal/kg).

TABLAS DE VAPORIZACION NATURAL ´
Utilizando la fórmula vista en el punto anterior, se han confeccionado unas tablas (origen LAPESA), para calcular el caudal obtenible por vaporización natural. Estas tablas se incluyen a continuación.
El significado de cada concepto utilizado en la tabla es el siguiente:

Diámetro. Se refiere al diámetro del depósito cilíndrico.
Volumen: Es el volumen geométrico del depósito. No confundir con la capacidad. Esta será como máximo el 85 % ´ de su volumen.

CALCULO DE LA VAPORIZACI ´ | ON´

Carga: La masa del GLP líquido contenido en el depósito (la de la fase gaseosa no se considera), con un grado de llenado del 85 % (carga máxima). Se calcula teniendo en cuenta una masa en volumen del propano de 506 kg/m³ .
El fabricante no menciona capacidades.

Carga = 0, 85 × V × ρ = 0, 85 × 506 × V = 430, 1 × V

(Nota: La fórmula original indica 5, 284 × V)

Superficie: Es la superficie exterior total del depósito, valor indicado por el fabricante. No se debe confundir con la superficie mojada por el líquido del interior. La superficie mojada por el líquido corresponde al 20 % de llenado (a), pero no al 20 % de la superficie total mencionada.

Presión: Presión de salida del regulador situado a la salida del depósito. Se escogerá entre las cuatro presiones indicadas.
A las presiones indicadas: → 1, 2 1, 5 1, 7 2, 0
les corresponde una temperatura Tg → −26◦C | − 22◦C | − 20◦C | − 17◦C

Temperaturas: En el caso de depósito aéreo se incluyen 5 temperaturas (−10◦, −5

| | ◦, 0 | ◦, 5 ◦ y 10◦C), mientras que
en el enterrado consideraremos solamente 5◦C. Las primeras corresponden a la temperatura ambiente mínima de la localidad donde se encuentra el depósito. Se tomará la más aproximada inferior. Por ejemplo, si la temperatura mínima media de Madrid es de −3

◦C, se tomará la columna correspondiente a −5

| | ◦C.

El caudal dado por la tabla corresponde a una reserva del 20 % del depósito. Para cualquier contenido superior al 20 %, se podrá obtener un caudal mayor al tabulado. Los valores para una reserva del 30 % se obtienen multiplicando los tabulados por 1,18.

CALCULO DE LA VAPORIZACI ´ | ON´

Determinación del caudal suministrable: Para un determinado depósito elegido, (por diámetro, por volumen o por carga máxima), una determinada presión regulada de salida y para una temperatura exterior mínima media, (si es un depósito enterrado, directamente a la columna de enterrado), se lee el caudal que en esas condiciones puede vaporizar en kg/h.

Determinación del depósito necesario: Partiendo de la temperatura exterior mínima media o de su ubicación enterrada y de la presión de salida del regulador, se busca el caudal deseado por exceso, obteniéndose el volumen, y el diámetro.

# TABLAS DE VAPORIZACION NATURAL ´

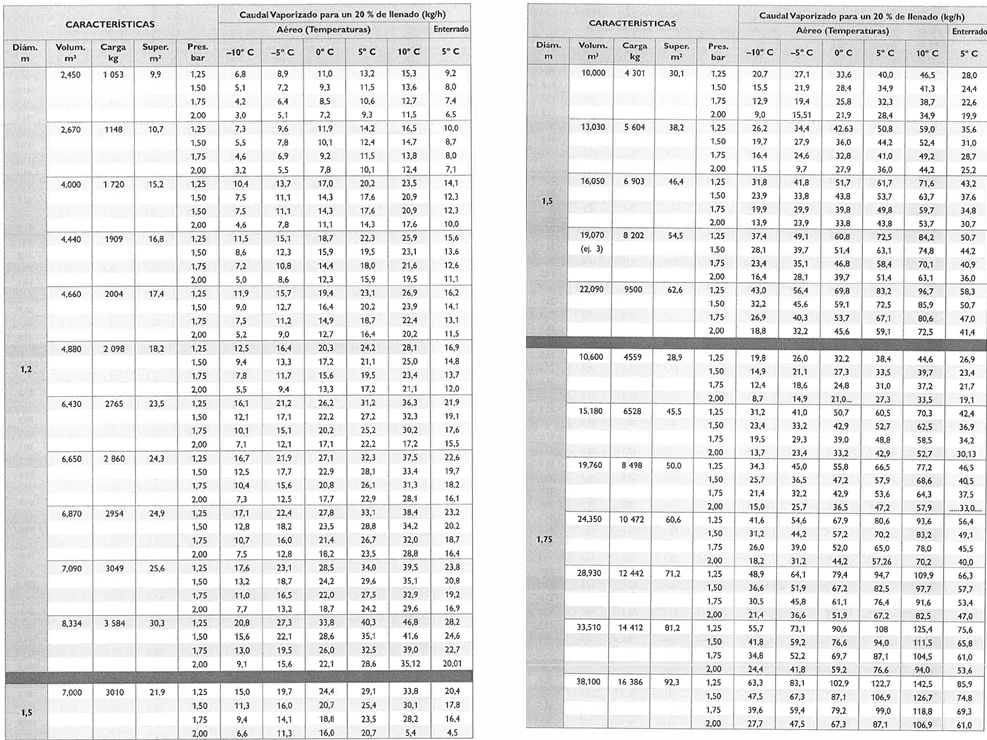
[picture p28: figure]

# TABLAS DE VAPORIZACION NATURAL ´

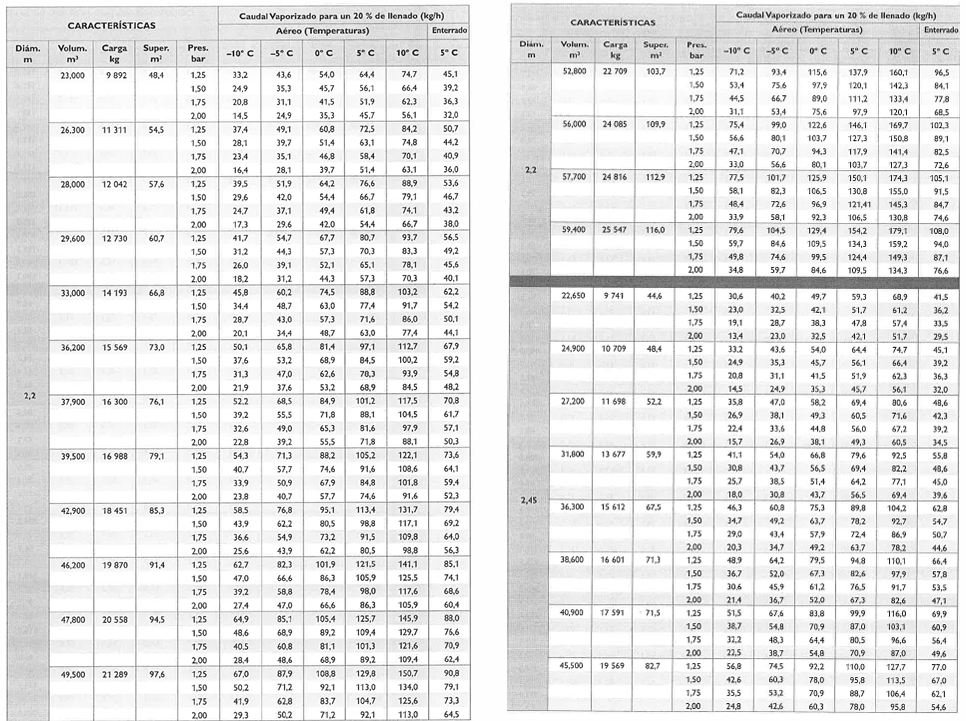
[picture p29: figure]

# TABLAS DE VAPORIZACION NATURAL ´

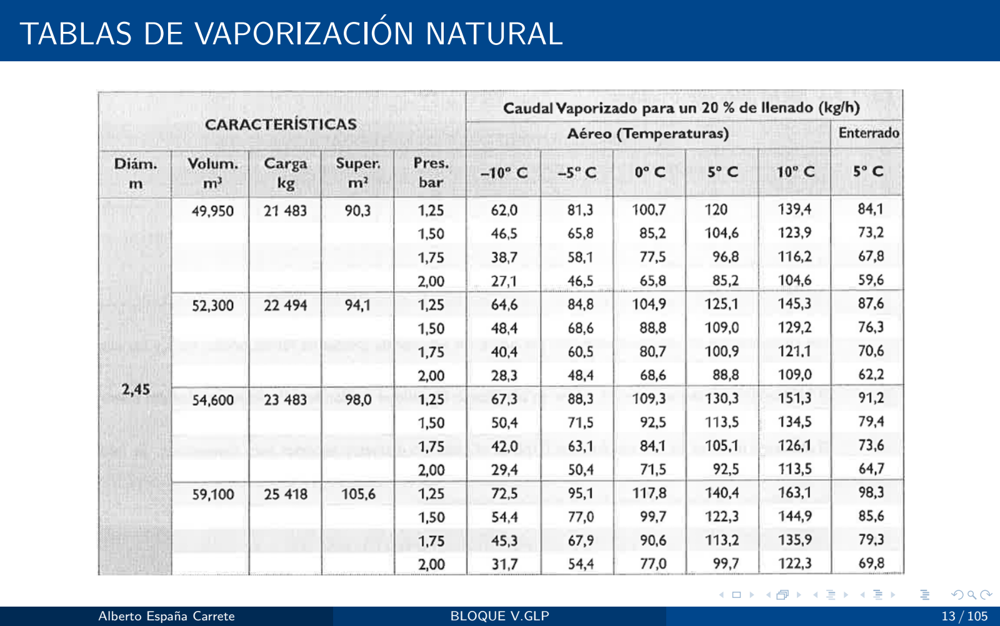
[picture p30: page 13]

# MATERIALES (I)

NORMATIVA SOBRE INSTALACIONES A CUMPLIR

Alm. dep. fijos | Reglamento GLP | RDF
Bot. ind. | Normas DM ¿ 15kg | NDM
Bot. dom. | Cond. Técn. Básicas | CTB
Redes dist.
Regl. Redes y Acom. RRA Acometidas Est. reg/med
Est. compr.
Recept. dom.
Recept. col. | Regl. Inst. Gas | RIGLO
Recept. com.
Recept. ind. | Normas básicas | NIGE

Resistencia mecánica (UNE 19 002)
Presión máx. serv. | MPB | MPA | BP
Resist. mín. | PN6 | PN4 | PN4

Presión máxima de servicio (Pmxs):

Pmxs = PN/Cs

# MATERIALES (II)

MATERIALES AUTORIZADOS EN INSTALACIONES DE GLP

MATERIALES AUTORIZADOS
| Material | BP | MPA | MPB | APA | APB
1.5.1.1 | Acero al carbono | Sí | Sí | Sí | Sí | Sí
1.5.1.2 | Acero inoxidable | Sí | Sí | Sí
1.5.1.3 | Cobre (Cu-DHP) | Sí | Sí | Sí
1.5.1.4 | PE (SDR11, MD) | Sí | Sí | Sí
1.5.1.5 | Tubos flexibles | Según naturaleza

Los componentes de una instalación son los tubos, los accesorios (piezas de forma, bridas, etc.), y los elementos auxiliares (llaves, filtros, limitadores de presión, etc.).
El fabricante suministrará con los tubos un certificado de calidad en donde se indique: calidad del material, controles de calidad, y procedimiento de fabricación (acero) o dimensiones (cobre).
El diámetro nominal de una conducción (DN) es el calibre o diámetro exterior para conexiones. Se mide en mm o en pulgadas.

# MATERIALES (III)

MATERIALES UTILIZADOS EN LA PRACTICA ´

En la práctica, se vienen utilizando los siguientes materiales:

MATERIALES UTILIZADOS
Fase gas | Fase líquida
General | Boca de carga
| Acero al carbono estirado y sin soldadura (UNE 19 040) | Acero al carbono estirado y s/s (UNE 19 040) St 33.2
| Acero inoxidable (UNE 19049) | NO AUTORIZADO
| Cobre duro estirado sin soldadura (EN 1057) | NO AUTORIZADO
| | Acc. de soldar de acero ANSI B.16.9 material A-234 WPB

Aéreas

Accesorios acero SWE 3000 Libras (1)
Enterrada
PE de media densidad SDR-11 (UNE 53 333) | NO AUTORIZADO
Acero al carbono, estirado y sin soldadura (ASTM-A-106 Gr B / API 5L Gr B) (2)
| Acc. de soldar de acero ANSI B.16.9 material A-234 WPB Accesorios acero SW 3000 Libras (1)
(1) SW = Socket Weld end 3000 psi (lb/in²) “extremo para soldar por enchufe”. Para soldaduras no radiografiadas.
(2) Protección catódica para longitudes mayores de 10 m.

EJEMPLO CALCULO DE INSTALACI ´ | ON DE GLP CON DEP ´ | OSITO ´

# PARA CHALET

EJEMPLO 1.- DATOS DE PARTIDA

Chalet ubicado en zona climática con temperatura de cálculo de −3

◦C

Instalación de un depósito de GLP a granel para abastecer servicios de cocina, calefacción y ACS

Potencia cocina referida al PCS : Pc= 6 kW

Potencia caldera mixta (ACS+calefacción), referida al PCS: Pc = 28,5 kW, la mayor de los dos servicios.

ESQUEMA

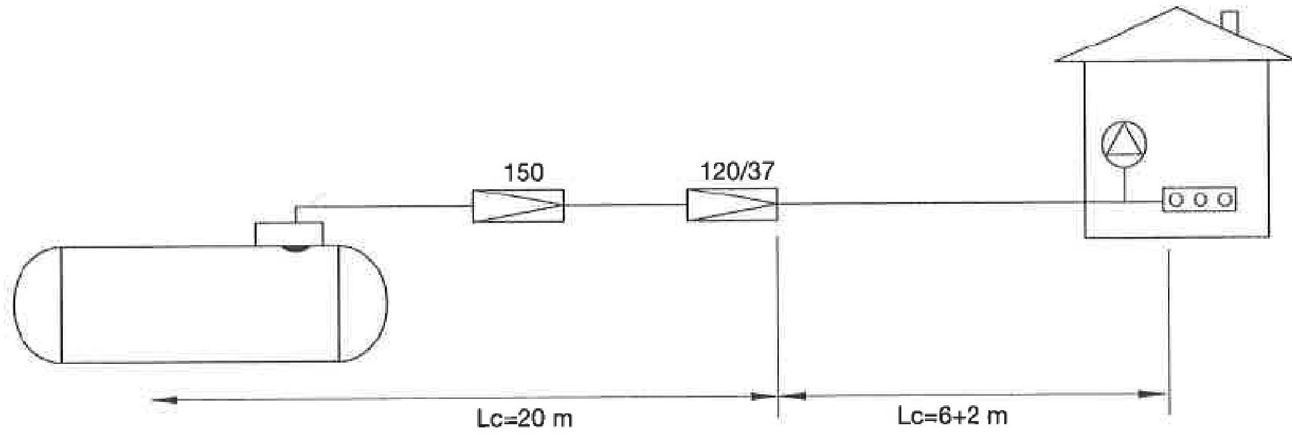
[picture p31: figure]

EJEMPLO CALCULO DE INSTALACI ´ | ON DE GLP CON DEP ´ | OSITO ´

# PARA CHALET

Grado de gasificación (GG): A partir de las potencias de cálculo de los aparatos se puede obtener la potencia de diseño, que es la nominal de utilización simultánea (Psi) de la instalación individual, según se determinó en el Tema 1:3.3.

Psi = PA + PB +

PC + PD + . . . PN
3

Psi = PCALDERA + PCOCINA = 28, 5 + 6 = 34, 5 kW

El valor de la potencia nominal de utilización simultánea es inferior a 70 kW pero mayor de 30 kW, por lo que a la instalación le corresponde un grado de gasificación GG 2.
Caudal de cada aparato (Q): Según se indicó en el punto 4.1, el caudal es el cociente entre la potencia de cálculo (superior) y el poder calorífico superior (no olvidar expresarlo en volumen; lo necesitaremos después para el cálculo del diámetro de las conducciones).

Q =

Ps
Hs

Qcoc =

Pcoc
Hs

=

6 kW
29, 23 kWh/m³ = 0, 21 m³
/h

Qcal =

Pcal
Hs

=

28, 5 kW
29, 23 kWh/m³ = 0, 98 m³
/h

EJEMPLO CALCULO DE INSTALACI ´ | ON DE GLP CON DEP ´ | OSITO ´

# PARA CHALET

Caudal de utilización simultánea individual: según se vio en el punto T1: 3.2, el caudal simultáneo individual es la suma representada en la igualdad siguiente:

Qsi = QA + QB +

QC + QD + . . . QN
2

Qsi = QCAL + PCOC = 0, 98 + 0, 21 = 1, 19 m³ /h

Tiempo de funcionamiento diario de los aparatos: Cada aparato es utilizado un diferente número de horas al día, dependiendo del número de integrantes de la familia, de su nivel de confort y de las costumbres de cada uno. Podemos considerar un valor medio de la utilización diaria, según la tabla siguiente: (en cada caso se podrá elegir el valor más conveniente):

Cocina TDIARIO = 1 hora por día

Agua caliente TDIARIO = 2, 5 horas por día

Calefacción TDIARIO = 6 horas por día

EJEMPLO CALCULO DE INSTALACI ´ | ON DE GLP CON DEP ´ | OSITO ´

# PARA CHALET

Consumo diario (CDIARIO): El consumo diario de gas de cada aparato se obtiene multiplicando el caudal que consume por el tiempo de funcionamiento diario. No interviene la simultaneidad

CDIARIO = Q × T

en m³
por día

CDIARIO−COC = QCOC × TDIARIO = 0, 21 m³

/h × 1 h/día = 0, 21 m³
/día

CDIARIO−CAL = QCAL × TDIARIO = 0, 98 m³

/h × 6 h/día = 5, 88 m³
/día

CDIARIO−ACS = QACS × TDIARIO = 0, 98 m³

/h × 2, 5 h/día = 2, 45 m³ /día

Obteniéndose así el caudal diario de gas: CDIARIO =

PQ × T = 8, 54 m³/día
Autonomía: Para una autonomía de 30 días, el contenido mínimo del depósito será:

Contenido = CDIARIO · N

◦
de días = 8, 54 m³

/día · 30 días = 256, 2 m³ de fase gaseosa

Cantidad equivalente a 256, 2 × 2, 095 = 536, 7 kg Esta cantidad ocupará en fase líquida un volumen de:
536,7 / 506 = 1,06 m³
(2,095 y 506 son la masa en volumen del propano en fase gas y líquida respectivamente) (al vaporizarse 1 m³ de líquido, se obtienen 506/2,095 = 241,5 m³ de gas)

EJEMPLO CALCULO DE INSTALACI ´ | ON DE GLP CON DEP ´ | OSITO ´

# PARA CHALET

EJEMPLO 1
Volumen del depósito. Autonomía resultante: Considerando que ha de quedar, por ejemplo, un 20 % de propano de reserva en el depósito, los 1,06 m³ de líquido deberán ocupar el 0,85 V - 0,20 V = 65 % de V, luego el volumen del depósito será:

1, 06 = 0, 65 · V , despejando V, queda:

V = 1, 06/0, 65 = 1, 63 m³

El depósito habrá de ser llenado la primera vez con el 65 % (1,06 m³ = 536,7 kg) más el 20 % de reserva, que hace un total del 85 % de V:

1, 63 × 0, 85 = 1, 38 m³
, equivalentes a 1, 38 × 506 = 698, 3 kg

Estos valores quedan resumidos en la siguiente tabla: (cálculo aproximado pues no se tiene en cuenta el gas que no se licúa, el que ocupa el 15 % del depósito) (Figura 1.6.1b).

EJEMPLO CALCULO DE INSTALACI ´ | ON DE GLP CON DEP ´ | OSITO ´

# PARA CHALET

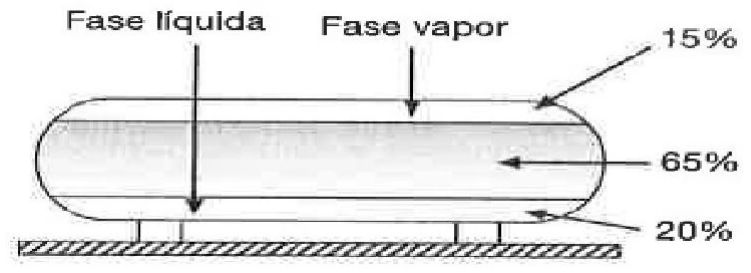
[picture p32: figure]

Figura: Figura 1.6.1b

| FASE GASEOSA | FASE LÍQUIDA
(m³ ) | (kg) | (m³ )
15 % | no tenido en cuenta
65 % | 256,2 | 536,7 | 1,06
20 % | | 161,6 | 0,32
85 % | | 698,3 | 1,38
100 % | | | V=1,63(*)
| m³ gas × 2,095 → kg ← m³ liquido × 506

EJEMPLO CALCULO DE INSTALACI ´ | ON DE GLP CON DEP ´ | OSITO ´

# PARA CHALET

(*) Cálculo directo: Partiendo del Contenido mínimo en fase gas necesario para alcanzar la autonomía deseada, se obtiene el volumen mínimo del depósito multiplicando dicho volumen gaseoso por 0,00637.
En este caso: 256, 2 m³ × 0, 00637 = 1, 63 m³ de depósito.
Más rápidamente se puede obtener mediante:
Volumen del depósito = Consumo diario x número de días de autonomía x 0,00637
En esta instalación se puede utilizar, al no existir un depósito de 1,63 m³, el inmediato superior, el depósito de V = 2, 45 m³ que proporcionará una autonomía (A) real de:

A =

V · 0, 65 · ρliq

CDIARIO · ρgas

=

V m³

- 0, 65 · 506 kg/m³
CDIARIO m³/día · 2, 095 kg/m³ =

157 · V

CDIARIO

EJEMPLO 1
En nuestro caso, 157 × V/CDIARIO = 157 × 2, 45/8, 54 = 45 días
Comprobación de la vaporización natural del depósito: El caudal de vaporización del depósito elegido, en las peores condiciones (a la temperatura de −5

◦C y estando con la reserva del 20 %), ha de ser igual o mayor que el caudal máximo probable (Qsi) requerido por la instalación en cuestión.
En nuestro ejemplo:
Qsi = 1, 19 m³/h, que expresado en masa es: 1, 19 m³/h · 2, 095 kg/m³ = 2, 49 kg/h
El depósito escogido, aéreo, según la tabla de vaporización natural en el punto 1.7.2, considerando que el regulador está ajustado a una presión de 1,25 bar, proporciona un caudal de vaporización natural mínimo de 8,9 kg/h (al encontrarse a

EJEMPLO CALCULO DE INSTALACI ´ | ON DE GLP CON DEP ´ | OSITO ´

# PARA CHALET

temperatura de cálculo de −3

◦C, se toma en la tabla −5

◦C). Por tanto, el depósito vaporiza lo suficiente. Si la presión de salida del regulador fuera mayor, el caudal suministrable por el depósito disminuiría, llegando a ser de 5,1 kg/h, siempre por encima del necesario.
Cálculo de los diámetros de la conducción: El caudal de gas máximo a suministrar será el de utilización simultánea, calculado anteriormente: Qsi = 1,19 m³/h
Se han de diferenciar las dos zonas existentes: la de MP (desde la llave de salida del almacenamiento hasta el regulador MP/BP) y la de BP. La primera es un tramo de 20 m y la segunda, está compuesta de tres tramos. Los escalonamientos de presión se determinan teniendo en cuenta el punto 1.6.5. Pérdida de carga admisible (Figura 1.6.1c).

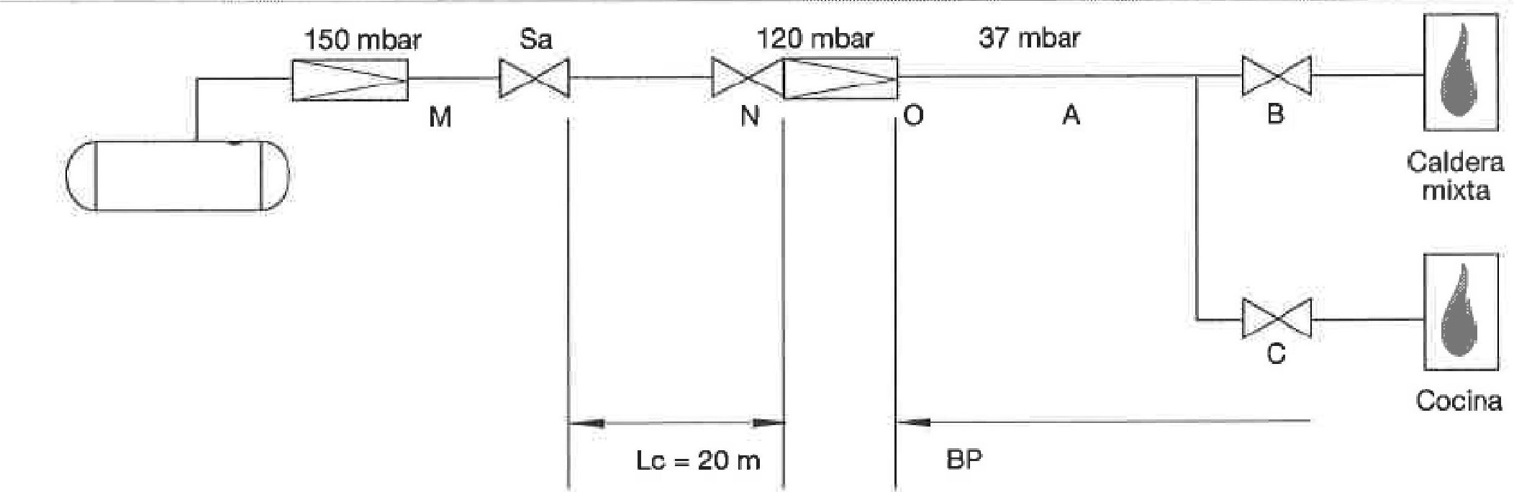
[picture p33: figure]

Figura: Figura 1.6.1c. Fuente: Elaboración propia.

Para evitar exceso de presión, esta se limita en la salida del depósito (150 mbar). La reducción a BP puede ser mediante regulador común (Caso A) o individual (Caso B):

EJEMPLO CALCULO DE INSTALACI ´ | ON DE GLP CON DEP ´ | OSITO ´

# PARA CHALET

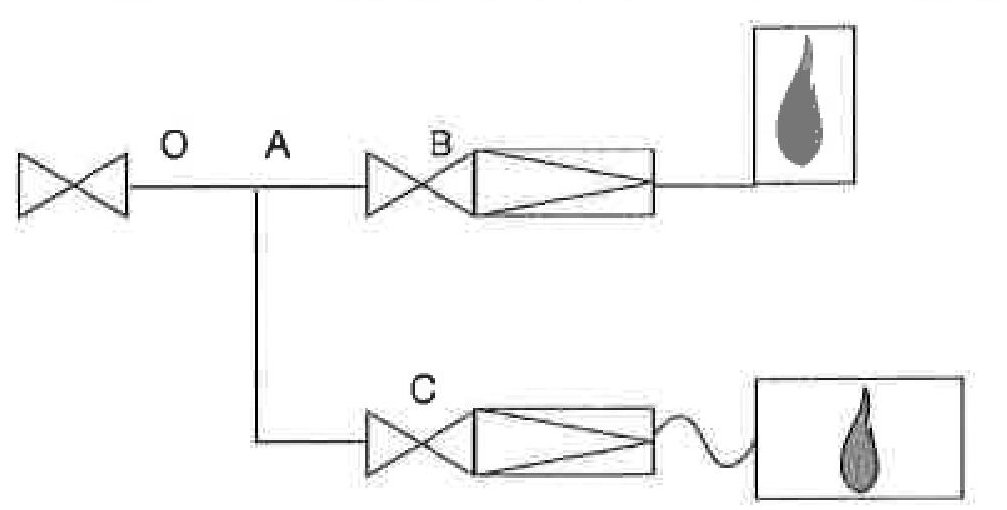
[picture p34: figure]
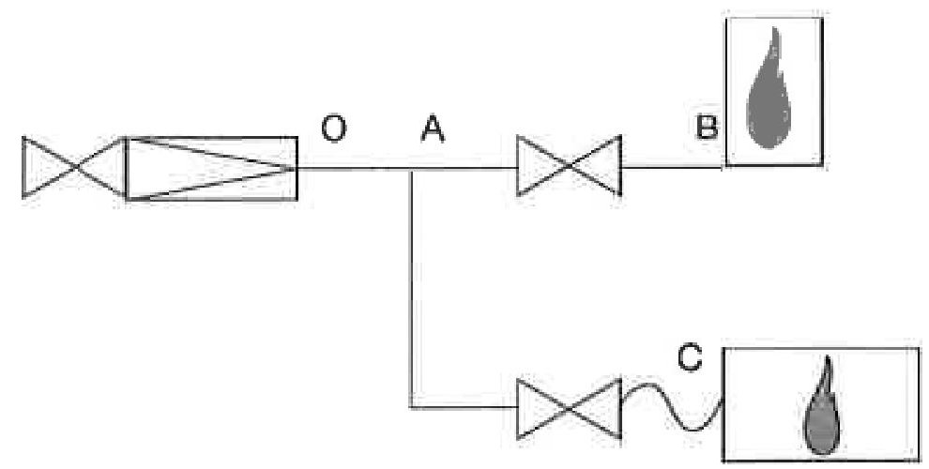
[picture p35: figure]

Figura: Figura 1.1.c. Casos A y B. Fuente: Elaboración propia.

Para el dimensionado de este tramo en Media Presión A (MPA), se consideran los siguientes parámetros fundamentales de diseño que garantizan la estabilidad del suministro:
Naturaleza del gas: Propano comercial (dc = 1, 16).

Rango de operación: Presiones comprendidas en MPA (100 mbar < P ≤ 400 mbar).

Criterio de cálculo: Pérdida de carga admisible según la presión mínima de entrada al regulador de segunda etapa.

EJEMPLO CALCULO DE INSTALACI ´ | ON DE GLP CON DEP ´ | OSITO ´

# PARA CHALET

Cálculo del tramo en MPA: El tramo entre reguladores tiene una longitud de cálculo de Lc = 20 m obtenida al multiplicar la geométrica por 1,2 (Lc = 1,2 x L). El caudal es de 1,19 m³/h
La presión a la salida del almacenamiento se elige dentro de la MPA (150 mbar) y la presión final del tramo es la mínima necesaria para funcionamiento correcto del regulador final (120 mbar) (Figura 1.6.1e).

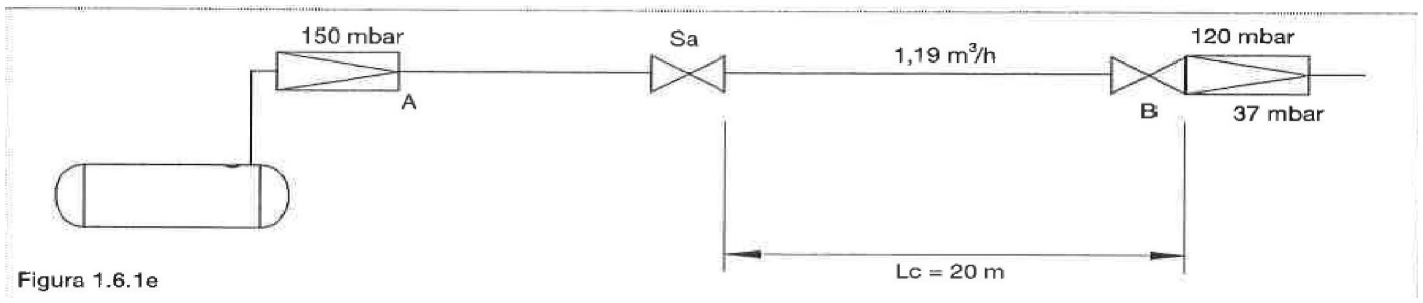
[picture p36: figure]

Figura: Figura 1.6.1e

EJEMPLO CALCULO DE INSTALACI ´ | ON DE GLP CON DEP ´ | OSITO ´

# PARA CHALET

Se ha de utilizar la fórmula correspondiente a MP: P

2
A − P

2
B = 51, 5 · dc · Lc ·

Q

1,82
D⁴,82 , en donde dc vale 1,16. Recordemos que las presiones se han de expresar en valores absolutos (por tratarse de MP). Despejando el valor del diámetro: D⁴,82 = 59, 74 × Lc × Q¹,82/(P

2
A − P

2
B

)
Sustituyendo valores, se obtiene:

D

4,82 = 59, 74 × 20 × 1, 19¹,82/

(0, 15 + 1, 01325)² − (0, 12 + 1, 01325)²
= 1194, 8 × 1, 3724466/0, 068895 = 23301, 4

Extrayendo la raíz, queda: D = 8,09 mm
Como diámetro comercial podemos elegir el de 10 mm puesto que el de 8 mm se considera demasiado reducido.
Veremos más adelante, en el cálculo de los tramos en BP, que para los diámetros se obtienen valores mayores que 10 mm. La razón de que salga para MPA un diámetro inferior a los calculados en tramos posteriores, se debe a que en este tramo la presión disponible es mayor.
Comprobación de la velocidad: Aplicando la fórmula del Tema 3:1.2:

v = 378, 04 ×

Q
P × D²

En este caso se obtiene un valor de: v = 378, 04 × 1, 19/{(1, 01325 + 0, 12) × 10²} = 3, 97 m/s, valor aceptado por ser menor que 10.

EJEMPLO CALCULO DE INSTALACI ´ | ON DE GLP CON DEP ´ | OSITO ´

# PARA CHALET

Cálculo mediante nomogramas (MPA)
Estos cálculos se simplifican empleando el NOMOgrama ONIRA-15 del punto T3: 1.3.7.2 (Figura 1.6.1f). La J

c en este caso vale: P

2
A − P

2
B

/Lc = 0, 068895/20 = 0, 00344475
Para un caudal de 1,19 m³/h y la J

c calculada, se obtiene el punto P que nos indica como más idóneo el diámetro de 10 mm (no se acepta el de 8 mm por la razón antes expuesta).

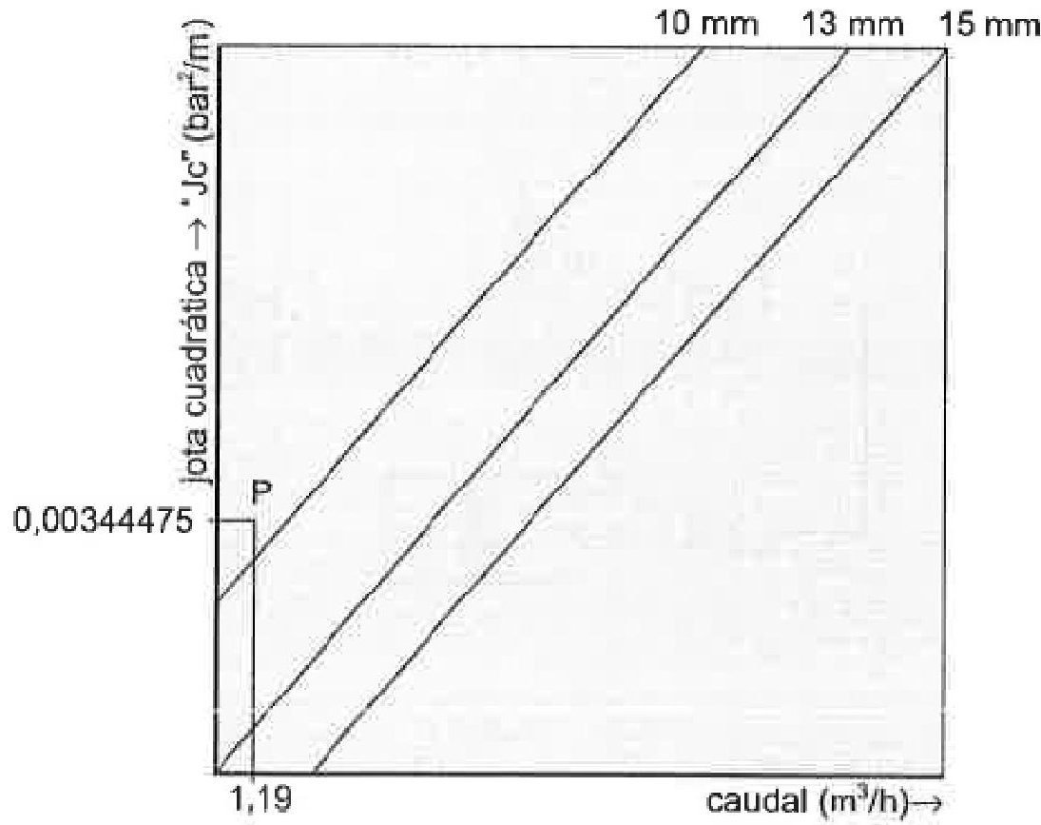
[picture p37: figure]

Figura: Figura 1.6.1f

EJEMPLO CALCULO DE INSTALACI ´ | ON DE GLP CON DEP ´ | OSITO ´

# PARA CHALET

Cálculo de los tramos en BP: Calculemos previamente los tramos correspondientes al esquema “A”.
En el esquema “A” existen dos cursos o itinerarios (conducción a calcular, entre el regulador y el aparato). El principal corresponde al aparato más alejado (OAB) y el secundario al otro (OAC).
La longitud de cálculo (Lc) de la conducción (ver punto T3: 1.3.4), será la geométrica (L) incrementada en un 20 %, resultando: Lc = 1,2 x L.
Sean las longitudes de cálculo resultantes de cada tramo: OA = 6 m; AB = 2 m; y AC = 1 m. (Recordemos que todas las longitudes a utilizar se han de expresar en valores de cálculo.)
La presión inicial a la salida del regulador MPA/BP, en O es de 37 mbar; y admitiendo una pérdida de carga del 5 %. Para el itinerario principal resultará una pérdida de carga disponible de:

PCd = 0, 05 × 37 mbar = 1, 85 mbar.

Este sistema se emplea porque no existen en el mercado reguladores que proporcionen una presión de salida algo mayor que 37 mbar para compensar la pérdida de carga de los tramos en BP (recordemos que para gas natural si se tiene en cuenta y se dispone en el mercado de reguladores con presión de salida de 22, 24 mbar, etc., por ejemplo.

Admitiendo esta situación, la presión a la entrada del aparato resultará ser de 37-1,85=35,15 mbar (la potencia del aparato queda en principio ligeramente reducida pues le llega el gas a presión inferior a la nominal) (Figuras 1.6.1g y 1.6.1h).

EJEMPLO CALCULO DE INSTALACI ´ | ON DE GLP CON DEP ´ | OSITO ´

# PARA CHALET

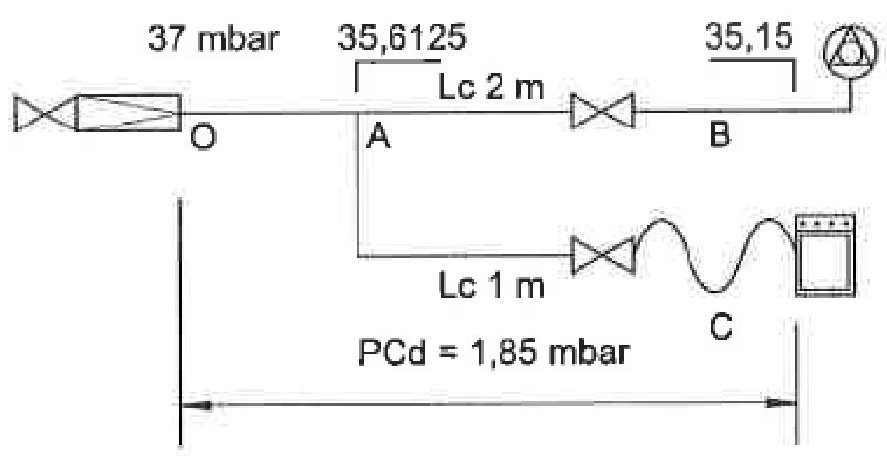
[picture p38: figure]

LOA = 6 m; LAB = 2 m; LAC = 1 m

Figura: Figura 1.6.1g

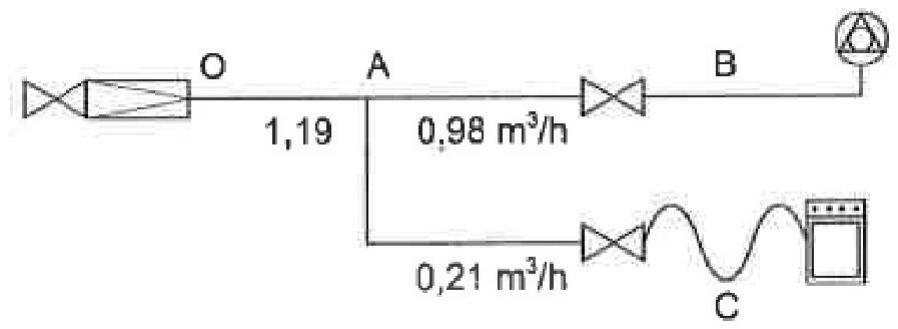
[picture p39: figure]

Figura: Figura 1.6.1h

EJEMPLO CALCULO DE INSTALACI ´ | ON DE GLP CON DEP ´ | OSITO ´

# PARA CHALET

Sistema de la “J”: Para determinar la presión en el nudo intermedio A se ha de emplear el sistema de la “J” consistente en el reparto de la PCd en función de la longitud de cálculo de los tramos.
Para ello se determina la pérdida de carga lineal (por metro de conducción de cálculo):

J =

PCd
Lc

La Longitud de cálculo considerada es la correspondiente al curso o itinerario principal (es más largo). En nuestro caso: J = 1,85 / (6+2) = 0,23125 mbar/m.

Al tramo OA de 6 m le corresponderá 6 × J, esto es, 6 × 0, 23125 = 1, 3875 mbar,

Al tramo AB, de longitud 2 m, le corresponderá 2 x J, esto es, 2 x 0,23125 = 0,4625 mbar

Al tramo AC también le corresponderá la misma PCd = 0,4625 mbar

EJEMPLO CALCULO DE INSTALACI ´ | ON DE GLP CON DEP ´ | OSITO ´

# PARA CHALET

Comprobación: 1,3875 + 0,4625 = 1,85 mbar

La presión en el nudo intermedio A valdrá: 37-1,3875=35,6125 mbar. Aplicando la fórmula de Renouard para BP

PA − PB = 25076 · dc · Lc ·

Q¹,82

D⁴,82

en donde dc para el propano y conducción de cobre vale 1,16 . La expresión 25 076 x 1,16 vale 29 088. Las presiones son relativas.
Despejando el diámetro:

D

4,82 = 29088, 16 × Lc × Q

1,82/ (Pi − Pf )

Aplicando esta fórmula al Tramo OA de 6 m de longitud de cálculo, por donde pasa un caudal de 1,19 m³/h:

D

4,82 = 29 088, 16 × 6 × 1, 19¹,82/1, 387 5 = 174 528, 96 × 1, 372 446 6/1, 387 5 = 172 635, 45

Extrayendo la raíz, se obtiene un diámetro teórico de D = 12,2 mm, por lo que se elige el diámetro comercial inmediato superior: 13 mm.
Comprobación de la velocidad resultante: Aplicando la fórmula para BP (Tema 3: 1.2):

v = 360 ×

Q
D²

EJEMPLO CALCULO DE INSTALACI ´ | ON DE GLP CON DEP ´ | OSITO ´

# PARA CHALET

se obtienen el valor v = 360 × 1, 19/13² = 2, 5 m/s inferior a 10 m/s y por lo tanto válido.
La comprobación puede realizarse directamente empleando el nomograma incluido en el punto T3: 1.3 (Nomo-12). Para el caudal 1.19 m³/h y un diámetro de 13 mm para 37 mbar, se obtiene el punto A = 2,5 m/s

Repitiendo las operaciones para cada uno de los tramos restantes, se obtienen los siguientes valores tabulados:

TRAMO | CAUDAL | Q1.82 | Pr. Inic. | PCd | Pr. final | Lc | D4.82 | D | Dc | velocid.
OA | 1.19m³ /h | 1.3724466 | 37mbar | 1.3875 | 35.6125 | 6m | 172635.45 | 12.2 | 13 | 2.5
AB | 0.98m³ /h | 0.9638988 | 35.6125 | 0.4625 | 35.15 | 2m | 121245.58 | 11.3 | 12 | 2.4
AC | 0.21m³ /h | 0.0584035 | 35.6125 | 0.4625 | 35.15 | 1m | 3673.19 | 5.5 | 10 | 0.7

Para el tramo AB se considera el caudal de 0,98 m³/h correspondiente a la caldera mixta. La presión inicial será la determinada para el nudo “A”. La pérdida de carga disponible será la total 1,85 menos la adjudicada al tramo anterior. Un cálculo más exacto se realiza aplicando la PCd que no fue utilizada en el tramo OA, (se ha elegido un diámetro mayor que el de cálculo, que ofrece una menor pérdida de carga), a los tramos siguientes. De esta forma se puede conseguir para dichos segundos tramos una reducción de los diámetros ya que con este procedimiento se aumenta su PCd.
Para el tramo AC se seguirá el mismo procedimiento.

EJEMPLO CALCULO DE INSTALACI ´ | ON DE GLP CON DEP ´ | OSITO ´

# PARA CHALET

Cálculo mediante nomogramas (BP) La utilización de los nomogramas facilita y aligera los cálculos. Para BP se emplea el nomograma ONIRA-12 (Fig. 1.6.1i).

Tramo OA:
Q = 1, 19 m³/h

J = 1, 3875/6 = 0, 23125 mbar/m

El punto A se halla entre las líneas de 10 y 13 mm. Se elige el diámetro mayor: 13 mm.

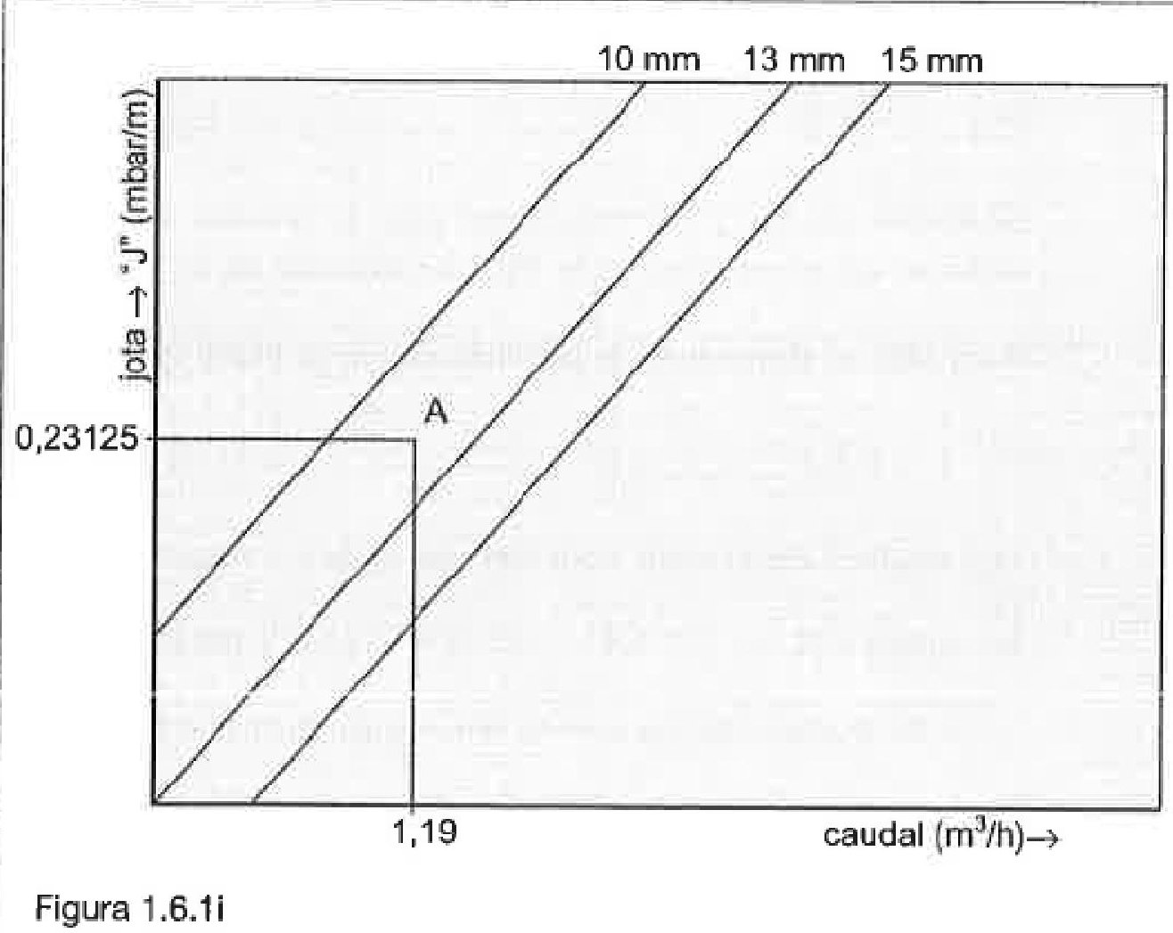
[picture p40: figure]

Tramo AB: Para Q = 0, 98 m³/h y J = 0, 23125, el punto B se sitúa entre 10 y 13 mm. Se elige: 13 mm.

Tramo BD: Para Q = 0, 21 m³/h y J = 0, 4625, el punto D se sitúa sobre la línea de 10 mm.

CALCULO DE INSTALACI ´ | ON DE GLP - DEP ´ | OSITO EN AZOTEA ´

DATOS DE PARTIDA
Edificio situado en una zona climática con una temperatura exterior de cálculo de 1◦C

5 Plantas, 10 viviendas con servicios de cocina, ACS y calefacción

Depósito de GLP en azotea

Potencia PCS cocina: 6 kW

Potencia PCS caldera : 20 kW

ESQUEMA

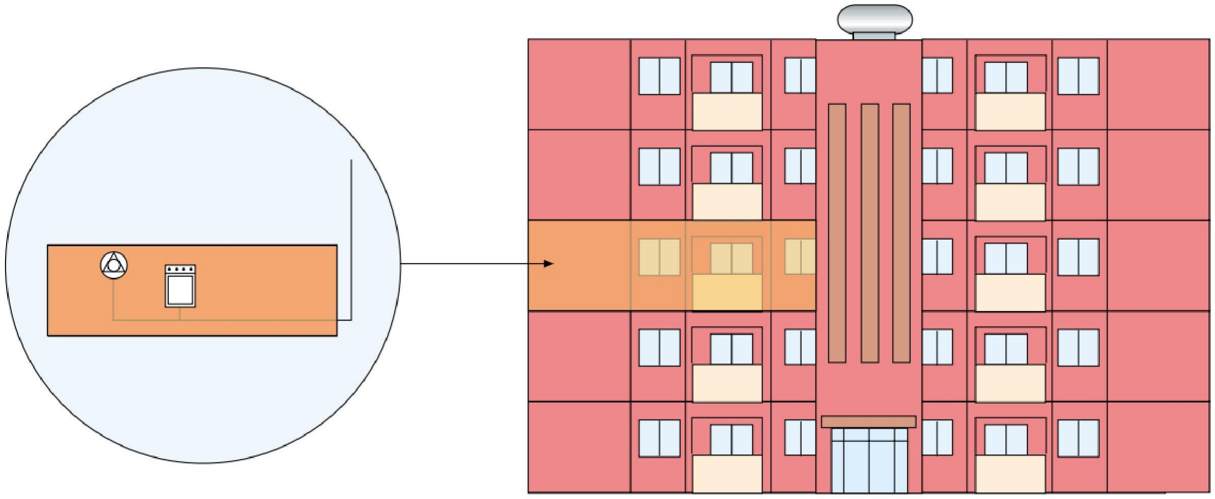
[picture p41: figure]

CALCULO DE INSTALACI ´ | ON DE GLP - DEP ´ | OSITO EN AZOTEA ´

Grado de gasificación (GG): A partir de las potencias de diseño de los aparatos se puede obtener la potencia nominal de utilización simultánea, (Psi) de la instalación individual, según se determinó en el punto 1.4.3.

Psi = PCALENTADOR + PCOCINA = 20 + 6 = 26 kW

La potencia nominal de utilización simultánea resulta de valor inferior a 30 kW, (GG 1), por lo que escogeremos la potencia de utilización simultánea igual a 30 kW.
Caudal de utilización simultánea individual: El caudal de simultaneidad individual será el correspondiente a una potencia de 30 kW y no a la suma de los caudales de cada aparato (no obstante los calculamos también):

Qsi =

Pt
Hs

=

30 kW
29, 23 kWh/m³ = 1, 03 m³
/h

Caudal de cada aparato: El caudal se obtiene de la división de la potencia de cálculo y el poder calorífico superior.

Qcoc =

Pcoc
Hs

=

6 kW
29, 23 kWh/m³ = 0, 21 m³
/h

Qcal =

Pcal
Hs

=

20 kW
29, 23 kWh/m³ = 0, 68 m³
/h

Caudal máximo probable para la instalación común: Al tratarse de bloques de viviendas, el volumen del depósito se puede calcular por métodos estadísticos. Como son 10 viviendas, el caudal máximo probable de la instalación común dependerá

CALCULO DE INSTALACI ´ | ON DE GLP - DEP ´ | OSITO EN AZOTEA ´

del factor de simultaneidad que tomaremos del tema 1. En el ejemplo, no existe calefacción por lo que a 10 viviendas corresponde un coeficiente de 0,25. (tendremos en cuenta que existen Comunidades Autónomas donde se han modificado algunos valores de los factores).

Qsc = S ×

XQsi = 0, 25 × 10 × 1, 03 m³ /h = 2, 58 m³
/h

Cálculo del depósito: Para obtener el volumen del depósito necesario, previamente hay que obtener el consumo anual por tablas experimentales (punto T3: 1.6) y luego reducirlo a consumo máximo diario.
Consumo de energía anual: La localidad donde se instalará el depósito se encuentra situada en la zona climática B (ver punto T3: 1.6), a la que le corresponde unos coeficientes de 1 para cocina y 0.88 para a.c.s.
El consumo anual para cocina y a.c.s. por vivienda, será:

CANUAL(C+ACS) = 1100 + 1520 × 0, 88 = 2438 kWh/año

Consumo diario: El consumo energético diario se obtiene dividiendo el anual por el número de días que se estima que se utilizarán al año estos aparatos. Sea una estimación de 260 días por año.

Qd(C+ACS) =

CANUAL(C+ACS)

260

=

2438
260

= 9, 38 kWh/día

El consumo en masa diario, necesario para saber qué depósito podremos necesitar, será el que resulte de dividir el energético por el Poder Calorífico Superior (Hs) del Propano (29,23 kWh/m³
)

CdV =

CD(C+ACS)

Hs

=

9, 38 kWh/día
29, 23 kWh/m³ = 0, 32 m³
gas/día

CALCULO DE INSTALACI ´ | ON DE GLP - DEP ´ | OSITO EN AZOTEA ´

Para las 10 viviendas tendremos el consumo en volumen total diario igual a:

CdV = 10 × 0, 32 m³

/día = 3, 2 m³
gas/día, para el bloque

Volumen del depósito y autonomía resultante: Si imponemos una autonomía de A = 30 días, el depósito necesario tendrá un volumen de: (ρ = 506 kg/m³
es la masa en volumen del propano en fase líquida) (punto T3: 1.6).

V =

CdV · A
0, 65

En nuestro caso,
Los 3,2 m³ gas/día equivalen a 3, 2 × 2, 095/506 = 0, 01328 m³ liq/día

V = CdV × A/0, 65 = 0, 01328 × A/0, 65 = 0, 01328 m³

liq/día × 30 días/0, 65 = 0, 613 m³

Se puede elegir el depósito más pequeño, el de V = 2, 45 m³ que dará una autonomía real de:

A =

0, 65 · V

CdV

En nuestro caso: A = 0, 65 V
CdV

= 0, 65 2,45
0,01328 = 120 días
Comprobación de la vaporización natural del depósito: El caudal máximo probable de las 10 viviendas, 2,58 m³/h, en expresión másica, es el siguiente:

CALCULO DE INSTALACI ´ | ON DE GLP - DEP ´ | OSITO EN AZOTEA ´

Qsc = 2, 58 m³

/h × 2, 095 kg/m³ = 5, 4 kg/h

El caudal de vaporización natural del depósito elegido, en las condiciones más desfavorables (a la temperatura de 0◦C y estando con la reserva del 20 %) y considerando que el regulador suministra una presión de 1,7 bar, es de 8,5 kg/h (ver tabla en puntoT3: 1.4.2), mayor que el máximo probable de las 10 viviendas Qs = 5,4 kg/h, luego es aceptado.
Si la presión de salida del regulador fuera menor; el caudal suministrable por el depósito se incrementaría.
Cálculo de los diámetros de la conducción. A la salida del depósito se instala un regulador con presión de salida de 1,7 bar (punto A). A la entrada del recinto de contadores (centralizados en la azotea), se sitúa un regulador con presión de salida de 150 mbar (presión mínima a la entrada de 1,2 bar). La presión disponible en el tramo AB es, por tanto de 500 mbar. El regulador individual de BP se sitúa a la entrada de cada vivienda; su presión de salida es de 37 mbar y la mínima de entrada para correcto funcionamiento con el caudal previsto es de 70 mbar.

CALCULO DE INSTALACI ´ | ON DE GLP - DEP ´ | OSITO EN AZOTEA ´

Cálculo del tramo común entre el regulador del depósito (1, 7 bar) y la entrada al recinto de contadores (150 mbar).

Parámetros de diseño:
Caudal: Qsc = 2, 58 m³/h

Densidad: dc = 1, 16
PA = 1, 7 bar/PB = 1, 0 bar

Instalación individual: Esquema a partir de la llave de abonado (Ab). Regulador BP común para ambos aparatos (Vi
: llave
vivienda; Ap: llaves aparatos).

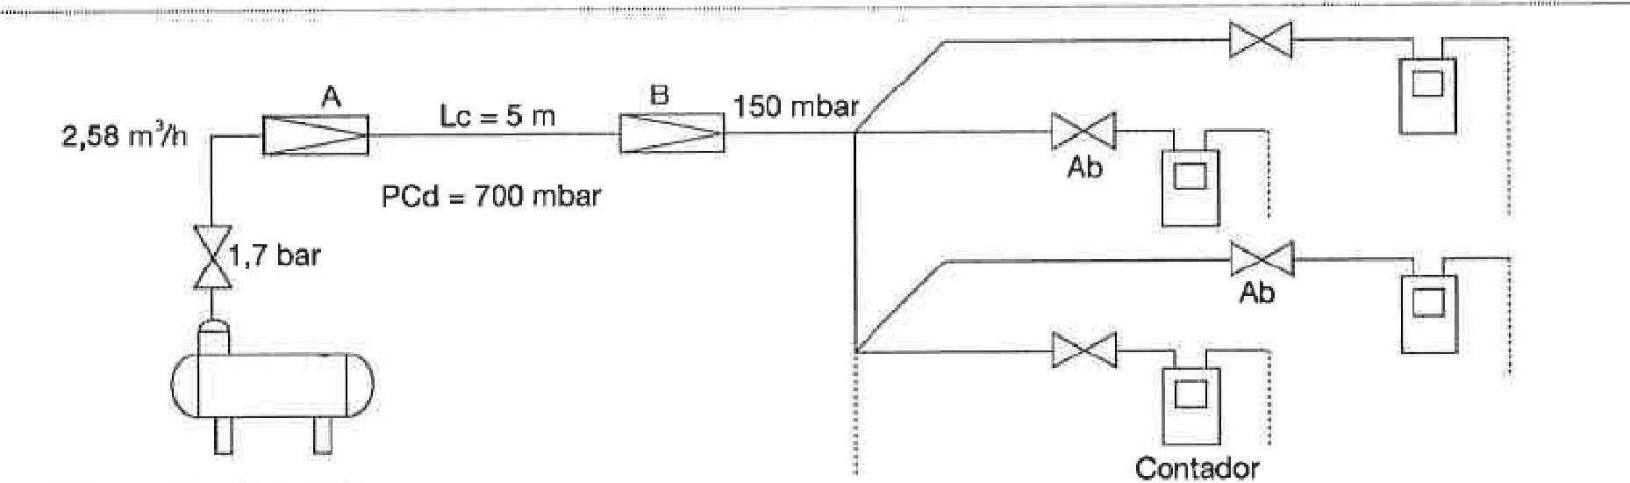
[picture p42: figure]

Figura: Fig. 1.6.2a. Común.

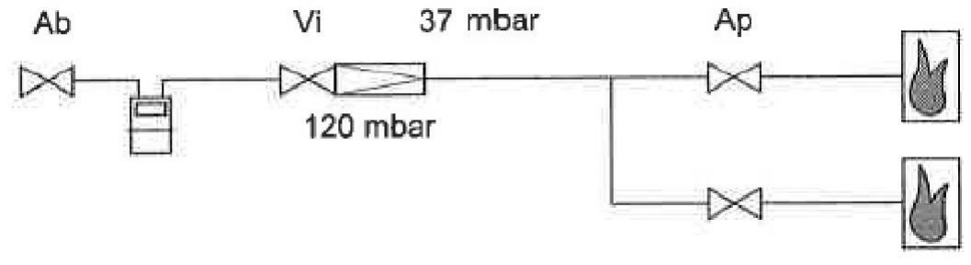
[picture p43: figure]

Figura: Fig. 1.6.2b. Individual.

Cálculo del tramo en MPB: Para una longitud de cálculo (Lc) del tramo entre reguladores de 5 m y aplicando Renouard, se tiene:
P

2
A − P

2

B = 51, 5 · dc · Lc · Q¹,82/D⁴,82, sustituyendo valores: 2, 71² − 2, 01² = 51, 5 · 1, 16 · 5 · 2, 58¹,82/D⁴,82 Realizando las operaciones indicadas: 3, 304 = 298, 7 · 5, 612/D⁴,82; o lo que es lo mismo:

CALCULO DE INSTALACI ´ | ON DE GLP - DEP ´ | OSITO EN AZOTEA ´

3, 304 = 1676, 3/D

4,82

Despejando: D⁴,82 = 507, 35/2, 464 = 205, 9. Se obtiene un diámetro D = 205, 9

1/4,82 = 3 mm
El diámetro comercial (Dc) inmediato superior para el tramo entre reguladores es de 10 mm, según lo convenido. Comprobación de la velocidad: Recordemos que ha de ser inferior a 10 m/s

v = 378, 04 × Q/(P × D

2

) = 378, 04 × 2, 58/[(1, 01325 + 1, 0) × 10² ] = 975, 3/201, 3 = 4, 8 m/s < 10 m/s

Para realizar el cálculo mediante nomograma se necesita conocer la J c cuadrática: (Nomograma ONIRA-15 del punto T3: 1.3.7.2).

JC =

P

2
A − P

2
B
Lc

En nuestro caso, vale: J

c = [(1, 7 + 1, 01325)² − (1 + 1, 01325)² ] × 5 = 0, 66 bar/m (Figura 1.6.2.c).

CALCULO DE INSTALACI ´ | ON DE GLP - DEP ´ | OSITO EN AZOTEA ´

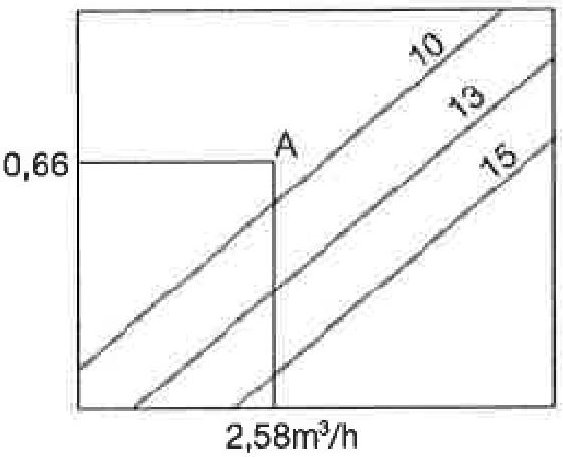
[picture p44: figure]

Figura: Figura 1.6.2c

Para un caudal de 2,58 m³/h y una Jc de 0,66, se obtiene el punto A sobre la línea correspondiente al diámetro 10 mm por lo que se elige este.
Cálculo del tramo en MPA: La instalación en MPA consiste en un tramo corto común, varios comunes para parte de los contadores, y de conducciones individuales en donde se incluyen los respectivos contadores. Termina a la entrada de los reguladores de BP individuales situados a la entrada de las respectivas viviendas. Se determinarán las presiones en los nudos intermedios utilizando el sistema de la “J” visto en el ejemplo num. 1 (punto 1.6.1).
Considerando que la distancia entre forjados es de 3 m, y que existe una conducción de 2 m en la parte superior, resulta una longitud geométrica para el itinerario individual más largo (la vivienda de la primera planta) de
Lg = 5 × 3 + 2 = 17 m y una longitud de cálculo de Lc = 1, 2 × Lg = 1, 2 × 17 = 20, 4 m (Figura 1.6.2d).

CALCULO DE INSTALACI ´ | ON DE GLP - DEP ´ | OSITO EN AZOTEA ´

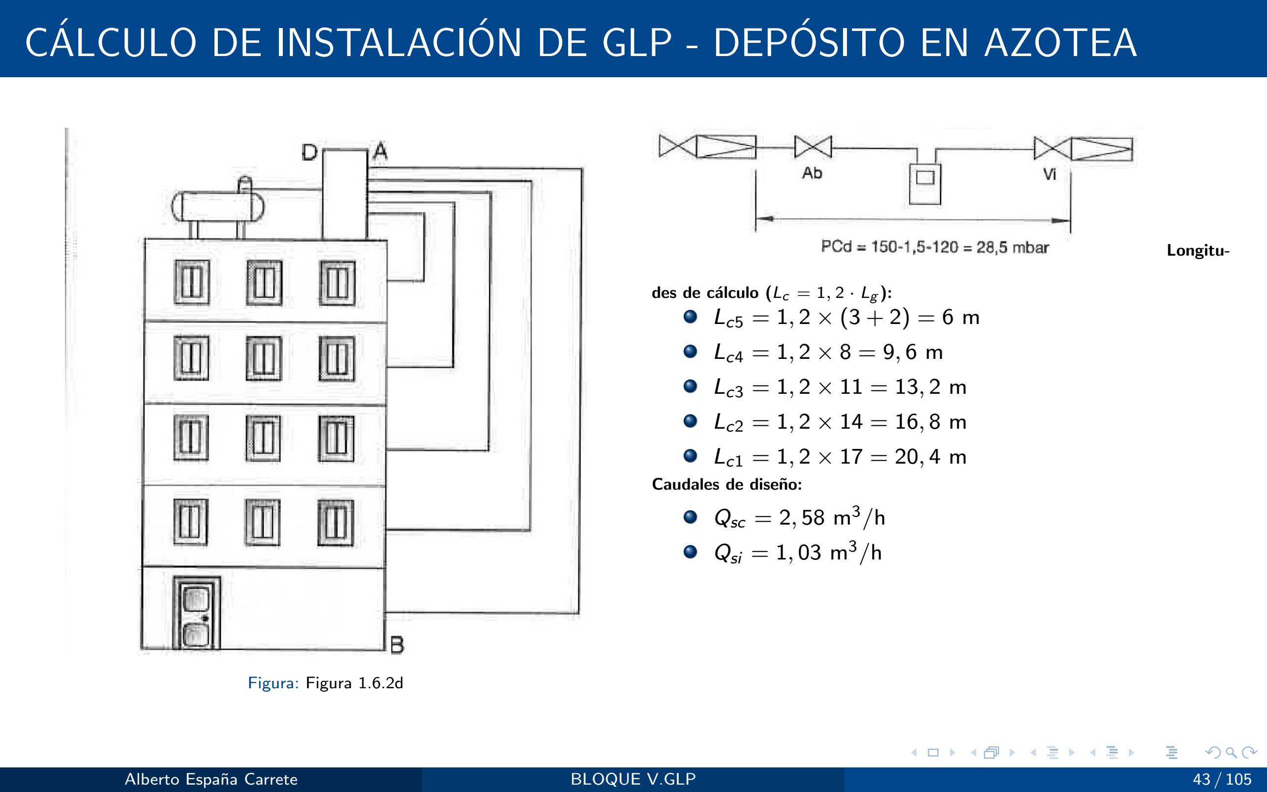
[picture p45: page 43]

Figura: Figura 1.6.2d

Longitu-

des de cálculo (Lc = 1, 2 · Lg ):
Lc5 = 1, 2 × (3 + 2) = 6 m

Lc4 = 1, 2 × 8 = 9, 6 m

Lc3 = 1, 2 × 11 = 13, 2 m

Lc2 = 1, 2 × 14 = 16, 8 m

Lc1 = 1, 2 × 17 = 20, 4 m

Caudales de diseño:
Qsc = 2, 58 m³/h

Qsi = 1, 03 m³/h

CALCULO DE INSTALACI ´ | ON DE GLP - DEP ´ | OSITO EN AZOTEA ´

Densidad de cálculo del propano : dc = 1,16
Presión inicial (salida del regulador de MPA): Pa = 150 mbar
Presión final (entrada del regulador de BP): Pb = 120 mbar
Se desprecia la ganancia de presión por altura:
PC del contador: no suele sobrepasar de 1,5 mbar (consultar la documentación del fabricante). Pérdida de carga disponible PCd = PA − PB − PCc = 150 − 120 − 1, 5 = 28, 5 mbar.
Este valor de PCd se utilizará para determinar la “J” en el cálculo de presiones intermedias. Aplicando Renouard para MP: P

2
A − P

2
B = 51, 5 · dc · Lc · Q¹,82/D⁴,82

El primer miembro valdrá: (1, 013 25 + 0, 15)² − (1, 013 25 + 0, 12)² = 1, 353 − 1, 284 = 0, 069

El segundo miembro valdrá: 51, 5 · 1, 16 · 20, 4 · 1, 03¹,82/D⁴,82 = 1 218, 7 · 1, 055/D⁴,82 = 1 285, 7/D⁴,82

Igualando los miembros: 0, 069 = 1 285, 729/D⁴,82
Despejando el valor del diámetro: D⁴,82 = 1 285, 729/0, 069 = 18 633, 75
De donde se obtiene el valor: D = 18 633, 75¹/4,82 = 7, 69 mm
El diámetro comercial inmediato por exceso es el de 8 mm (se elige el de 10 mm). Comprobación de la velocidad: El valor de la velocidad con este diámetro será:
v = 378, 04 × Q/(P × D²

) = 378, 04 × 1, 03/[(1, 013 25 + 0, 12) × 10² )] = 3, 4 m/s, aceptable por ser inferior a 10 m/s. El diámetro de los tramos comunes se pueden calcular directamente empleando la fórmula de la velocidad, para v = 10: v = 378, 04 × Q/(P × D²

). Despejando el diámetro: D² = 378, 04 × Q/(v × P). Sustituyendo valores: D² = 378, 04 × 2, 58/[10 × (1, 013 25 + 0, 15)] = 975, 34/(10 × 1, 16) = 975, 34/11, 6 = 84 Extrayendo la raíz:. D = 9, 2 mm. El diámetro comercial inmediato superior es el de 10 mm.
El resto de las conducciones bajantes se calcularán de la misma manera. Al ser más cortas que la calculada y tener que transportar el mismo caudal, podrán ser del mismo diámetro.
La instalación individual se calculará como en el ejemplo anterior.

CALCULO DE INSTALACI ´ | ON DE GLP - DEP ´ | OSITO EN AZOTEA ´

Cálculo mediante nomogramas (MP)
Para realizar el cálculo mediante nomograma, se necesita conocer la “Lc” cuadrática de cada tramo. En el tramo de MPB, vale: J

c = [(1, 7 + 1, 01325)² − (1 + 1, 01325)²
]/5 = 3, 308/5 = 0, 66171
Para un caudal de 2,58 y una J

c de 0,66171, se obtiene el punto A sobre la línea correspondiente al diámetro 10 mm. Se elige el inmediato superior, el de 10 mm, por lo que se elige este diámetro. Para cada bajante, cuyo caudal es 1,03, le corresponde una

J

c =

(1, 01325 + 0, 15)² − (1, 01325 + 0, 12)²
/20, 4 = (1, 35315 − 1, 28425)/20, 4 = 0, 0689/20, 4 = 0, 003377

En el nomograma para MP (punto T3: 1.3.7.2) se obtiene el punto M al que le corresponde el diámetro 10 mm.

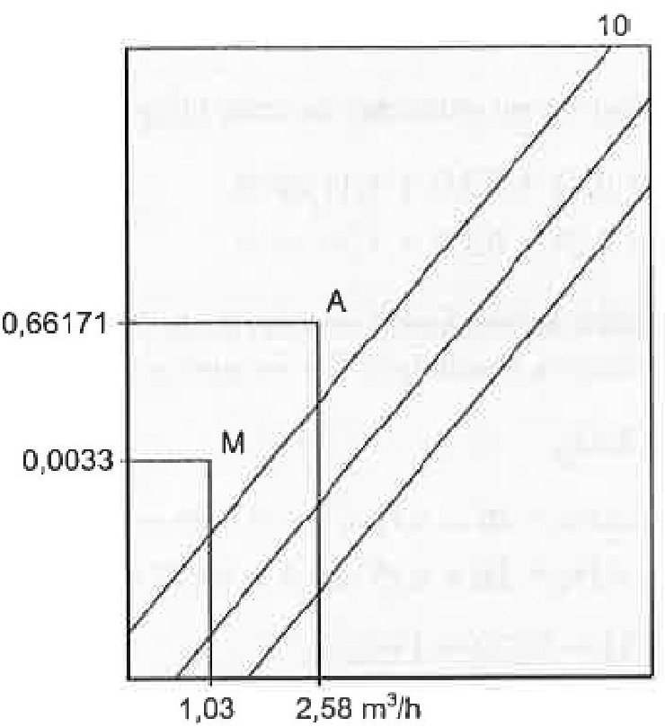
[picture p46: figure]

Figura: Figura 1.6.2e

INSTALACION DE GLP CANALIZADO - URBANIZACI ´ | ON´

EJEMPLO 3
Se trata de dos bloques de viviendas con 20 viviendas cada uno. Se encuentran ubicados en Zona climática C con temperatura de cálculo 0◦C. En cada una de las viviendas se instalarán los siguientes aparatos (Figura 1.6.3):

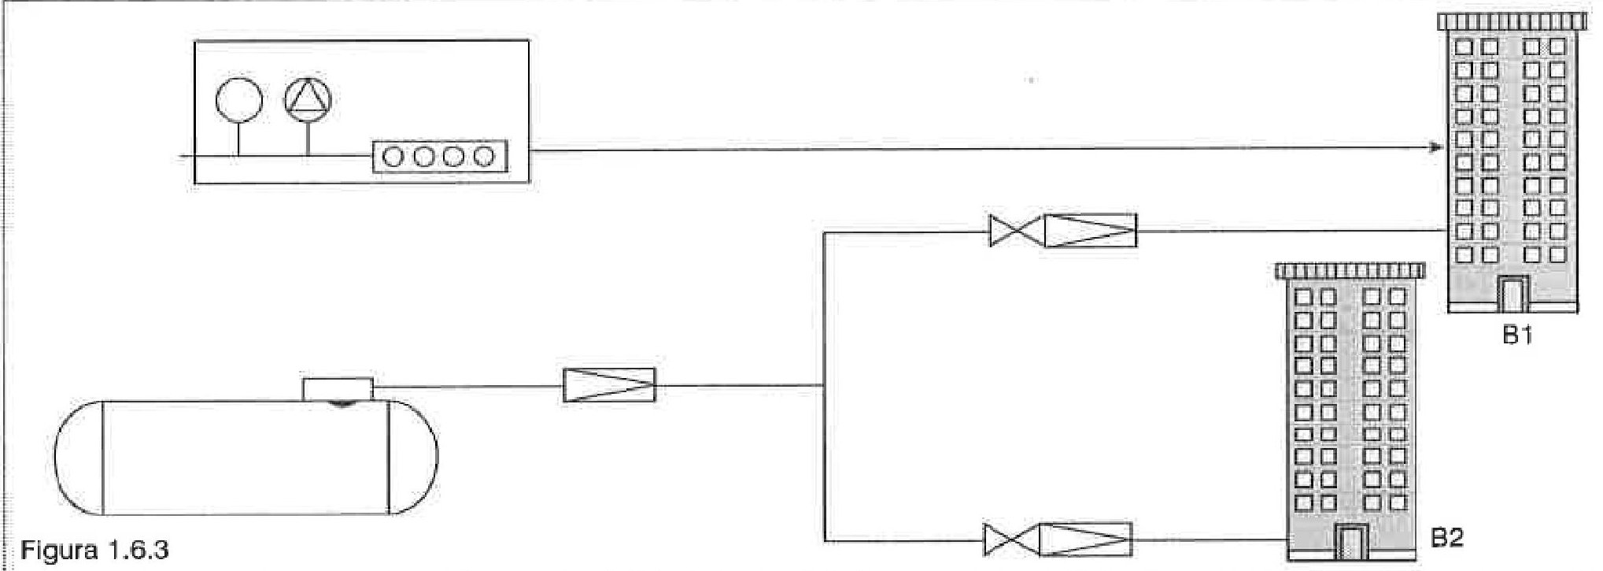
[picture p47: figure]

BLOQUE 1 | BLOQUE 2
Cocina | 6kW | Cocina | 6kW
ACS | 20kW | ACS | 20kW
Caldera de calefacción | 10kW | Caldera de calefacción | 15kW

La potencia de cálculo (nominal de utilización simultánea) de cada una de las viviendas será:

Psi= | Psi=
PACS+PCALEF+1/2PCOC=20+10+1/2(6)=33kW | PACS+PCALEF+1/2PCOC=20+15+1/2(6)=38kW

INSTALACION DE GLP CANALIZADO - URBANIZACI ´ | ON´

Lo que significa un grado de gasificación 2 para ambos bloques (por ser 70 ¿ Psi ¿ 30 kW). Los caudales de los aparatos resultan ser: Q = Pc (kW) /Hs

kWh/m³
BLOQUE 1 | BLOQUE 2
QACS 29,23 = 0,68 m³/h 20 | QACS 29,23 = 0,68 m³/h 20
QCALEF 29,23 = 0,34 m³/h 10 | QCALEF 29,23 = 0,51 m³/h 15
29,23 = 0,20 m³/h 6 QCOC | QCOC 29,23 = 0,20 m³/h 6

Los caudales de simultaneidad de las viviendas de cada bloque serán:
Bloque 1◦: Qsi=0,68+0,34+0,2/2=1,12 m³/h
Bloque 2◦: Qsi=0,68+0,51+0,2/2=1,29 m³/h
El caudal máximo probable para la instalación común, al ser 20 viviendas, dependerá del factor de simultaneidad, a tomar del punto T1, con calefacción, resultando 0,4 en ambos bloques.
Para cada bloque: QsC = S

PQsI
Para el Bloque 1: S × QsI−1 × N1 = 20 × 1, 12 × 0, 4 = 8, 96 m³/h Para el Bloque 2: S × QsI−2 × N2 = 20 × 1, 29 × 0, 4 = 10, 32 m³/h Para el conjunto: Qsc = 8, 96 + 10, 32 = 19, 28 m³/h

INSTALACION DE GLP CANALIZADO - URBANIZACI ´ | ON´

Cálculo del depósito: Para obtener el volumen del depósito necesario, considerando un mínimo de 30 días de autonomía, previamente hay que obtener el consumo anual por tablas experimentales (punto T3: 1.6) y luego reducirlo a consumo máximo diario, siguiendo el sistema descrito en el ejemplo núm. 2.
Consumo anual por cocina y a.c.s.: se calcula como en el ejemplo num. 2. Al encontrarse la instalación en zona climática C, los coeficientes zonales son 1 y 1: Las necesidades anuales por vivienda serán: (Consultar Zonas climáticas y coeficientes zonales del punto 1.6).

CANUAL(COC+ACS) = 1100 + 1520 × 1 = 2620 kWh/año

Consumo diario individual por cocina y a.c.s.: Se obtiene al dividir el consumo anual entre los días de utilización previstos (260 días):

CDIARIO =

CANUAL
260

=

2620
260

= 10, 1 kWh/día

Consumo diario individual por calefacción: Para calcular el consumo diario en calefacción se emplea la fórmula dada en el punto T3: 1.6:

CCALEF = 0, 043 × S × Ft × ∆t

siendo:
S = Superficie de la vivienda. Tomaremos 120 m² en el ejemplo
Ft = Factor tipo. Se toma 1 al tratarse de un bloque de categoría normal. ∆t = Salto térmico para el día más frío. En nuestro caso, 15◦ − 0
- = 15◦C.
Aplicado a nuestro caso, obtendremos un consumo diario por calefacción de:

INSTALACION DE GLP CANALIZADO - URBANIZACI ´ | ON´

CCALEF = 0, 043 × S × Ft × ∆t = 0, 043 × 120 × 1 × 15 = 77, 4 kWh/día

Consumo diario total por vivienda: Sumando los consumos de cocina y a.c.s con los de calefacción, y dividiéndolo por el poder calorífico superior (Hs), se obtiene el consumo másico diario por vivienda:

CDIA−V =

(10, 1 + 77, 4) kWh/día
29, 23 kWh/m³ = 2, 99 m³
/día, por vivienda

Para 40 viviendas se tendrá un consumo total diario de:

CTOTAL−V = 40 × 2, 99 = 119, 74 m³
| /día para los dos bloques

INSTALACION DE GLP CANALIZADO - URBANIZACI ´ | ON´

Volumen del depósito y autonomía resultante: Para determinar el depósito necesario imponemos la autonomía mínima de A = 30 días. (ρ = 506 kg/m³
, es la masa en volumen del propano en fase líquida). (Ver punto T3: 1.6.) Los 119,74 m³/día equivalen a 119, 74 × 2, 095/506 = 0, 496 m³
liq./día.

VDEPO =

CTOTAL × A
0, 65

=

0, 496 m³/día × 30 días

0, 65

= 22, 9 m³

El depósito comercial más próximo por exceso es el de 24,35 m³
, de 1,75 m de diámetro.
La autonomía real de este depósito se obtiene al aplicar la fórmula:

A =

0, 65 · VDEPO

CdV

En nuestro caso, A = 0,65 × 24,35 /0,496 = 31,9 días
Comprobación de la vaporización natural del depósito: El depósito elegido de 24,35 m³ en las condiciones más desfavorable (para t = 0◦C) y presión de salida 2 bar vaporiza 44,2 kg/h. (ver punto T3: 1.4.2). Si se reduce la presión de salida del regulador hasta 1,25 bar, el caudal pasa a ser de 67,9 kg/h.

INSTALACION DE GLP CANALIZADO - URBANIZACI ´ | ON´

El caudal máximo probable de la instalación común es:

Qsc = 19, 28 m³

/h × 2, 095 kg/m³ = 40, 39 kg/h,

en cualquier caso, inferior al suministrable por el depósito, por lo que el depósito de 24,35 m³
se acepta, con una
autonomía de: A = 31,9 días.
Si el caudal de vaporización del depósito elegido fuera insuficiente para las necesidades punta que se pudieran tener, habría que tomar alguna de las soluciones siguientes:

Mantener el depósito instalado e incorporar un vaporizador para elevar el caudal.

Elegir un depósito más grande.

Reducir la presión de salida del regulador para incrementar el caudal.

Para el cálculo de los diámetros de las conducciones, seguir lo indicado en los ejemplos anteriores.

CALCULO DE INSTALACI ´ | ON INDUSTRIAL DE GLP ´

En este último ejemplo abordamos una instalación industrial con varios tipos de aparatos. Se encuentra ubicada en zona climática B con temperatura de cálculo de 2◦C (Figura 1.6.4a).

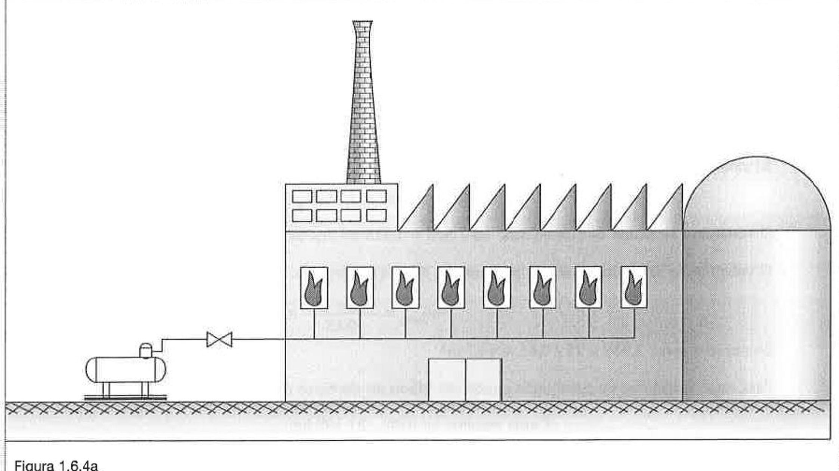
[picture p48: figure]

Dispondremos de dos hornos de secado, una caldera para agua caliente, una caldera de calefacción y cuatro hornos de fusión cuyas potencias de cálculo son las siguientes:

Horno de secado 42 kW × 2 = 84 kW Caldera para A.C.S. 35 kW × 1 = 35 kW Caldera de calefacción 230 kW × 1 = 230 kW Horno de fusión 700 kW × 2 = 1400 kW Total: 1749 kW

Grado de gasificación: El grado de gasificación será 3, debido a que la suma de las potencias de cálculo supera los 70 kW.

CALCULO DE INSTALACI ´ | ON INDUSTRIAL DE GLP ´

El caudal de simultaneidad o caudal máximo probable (QTOTAL), será la suma de todos los caudales.

QHS =

42
29, 23

= 1, 44 m³

/h → QHS = 1, 44 × 2 = 2, 88 m³ /h

QACS =

35
29, 23

= 1, 20 m³

/h → QACS = 1, 20 m³
/h

QCAL =

230
29, 23

= 7, 87 m³

/h → QCAL = 7, 87 m³
/h

QHF =

700
29, 23

= 23, 94 m³

/h → QHF = 23, 94 × 2 = 47, 88 m³ /h

QTOTAL = 2, 88 + 1, 20 + 7, 87 + 47, 88 = 59, 83 m³ /h

Valor equivalente en masa: QTOTAL = 59, 83 m³/h × 2, 095 kg/m³ = 125, 34 kg/h
Para el cálculo del volumen del depósito necesario impondremos una autonomía mínima de A = 15 días.

CALCULO DE INSTALACI ´ | ON INDUSTRIAL DE GLP ´

Tiempo de funcionamiento diario de los aparatos: Los tiempos estimados son los siguientes: Horno de secado
TDIARIO = 6 h/día

Caldera para A.C.S.
TDIARIO = 4 h/día

Caldera de calefacción
TDIARIO = 8 h/día

Horno de fusión
TDIARIO = 8 h/día

Consumo diario: el consumo diario de cada aparato (producto del caudal por el tiempo de funcionamiento), y por consiguiente el total, será:
Horno de secado
Cd−HS = 2, 88 m³

/h × 6 h/día = 17, 28 m³
/día

Caldera para A.C.S
Cd−ACS = 1, 20 m³

/h × 4 h/día = 4, 80 m³
/día

Caldera de calefacción
Cd−CAL = 7, 87 m³

/h × 8 h/día = 62, 96 m³
/día

Horno de fusión
Cd−HF = 47, 88 m³/h × 8 h/día = 383, 04 m³/día CTOTAL = 468, 08 m³/día

CALCULO DE INSTALACI ´ | ON INDUSTRIAL DE GLP ´

Su valor másico será:

CM = 468, 08 m³

/día × 2, 095 kg/m³ = 981 kg/día

El volumen que ocupa en fase líquida: 981/506 = 1,938 m³ liq./día
El volumen de depósito necesario para quince días de Autonomía, será:

VDEPO =

Cliq−V · A
0, 65

m³

En nuestro caso: 1,938 x 15/0,65 = 44,7 m³
Para estas exigencias de autonomía puede ser válido un depósito de 49,5 m³ cuyas características principales son: Carga máxima (al 85 %) 21289kg
Superficie exterior 97,6 m²
Diámetro del cilindro 2,2 m

Comprobación de la vaporización natural del depósito: Las necesidades de caudal de la instalación, en unidades másicas, calculadas anteriormente, son:

QM−TOTAL = 59, 83 m³

/h × 2, 095 kg/m³ = 125, 34 kg/h

El caudal de vaporización natural que nos ofrece el depósito elegido dependerá de la presión de salida del regulador y de la temperatura mínima del lugar de emplazamiento. Estos valores se toman de la tabla facilitada por el fabricante del depósito y que se encuentra en el punto T3: 1.4.2.

CALCULO DE INSTALACI ´ | ON INDUSTRIAL DE GLP ´

Para una temperatura de cálculo de 0◦C (inmediata inferior a 2◦C), los valores del caudal de vaporización están dados en la tabla siguiente donde se encuentran las características básicas de los volúmenes superiores:

CARACTERÍSTICAS BASICAS DE LOS DEP ´ | OSITOS ´
Volumen | 49,5m³ | 52,8m³ | 56m³ | 57,7m³
Carga máxima(al 85 %) | 21289kg | 22709kg | 24085kg | 24816kg
Superficie exterior | 97,6m² | 103,7m² | 109,9m² | 112,9m²
Diámetro del cilindro | 2,2m | 2,2m | 2,2m | 2,2m
Caudales | 108,8 y 71,2kg/h | 115,6 y 75,6kg/h | 122,6 y 80,1kg/h | 125,9 y 82,3kg/h

En nuestro caso, el valor de 125,34 kg/h empieza a ser cubierto a partir del depósito de 57,7 m³
Si no se desea disponer un depósito tan grande, se estudiará la incorporación de un vaporizador. El caudal obtenible con el vaporizador (Qv ) (ver T3: 2.21), deberá ser un 30 % mayor que el de las necesidades másicas:

Qv = 1, 3 × QM−TOTAL = 1, 3 × 125, 34 = 163 kg/h

La potencia de la caldera que al vaporizador deberá tener una potencia de: (ver punto 2.16 sobre de vaporizadores).

PCALEF =

Qv × 0, 11
0, 8

=

163 × 0, 11
0, 8

= 22, 41 kW

siendo 0,11 kWh/kg, el calor latente de vaporización del propano y 0,8 el rendimiento considerado.

Cálculo de la conducción: En las instalaciones industriales, los reguladores de BP se sitúan a la entrada de cada aparato. El cálculo de los diámetro mínimos necesarios para la instalación se realiza por tramos (Figura 1.6.4b).

CALCULO DE INSTALACI ´ | ON INDUSTRIAL DE GLP ´

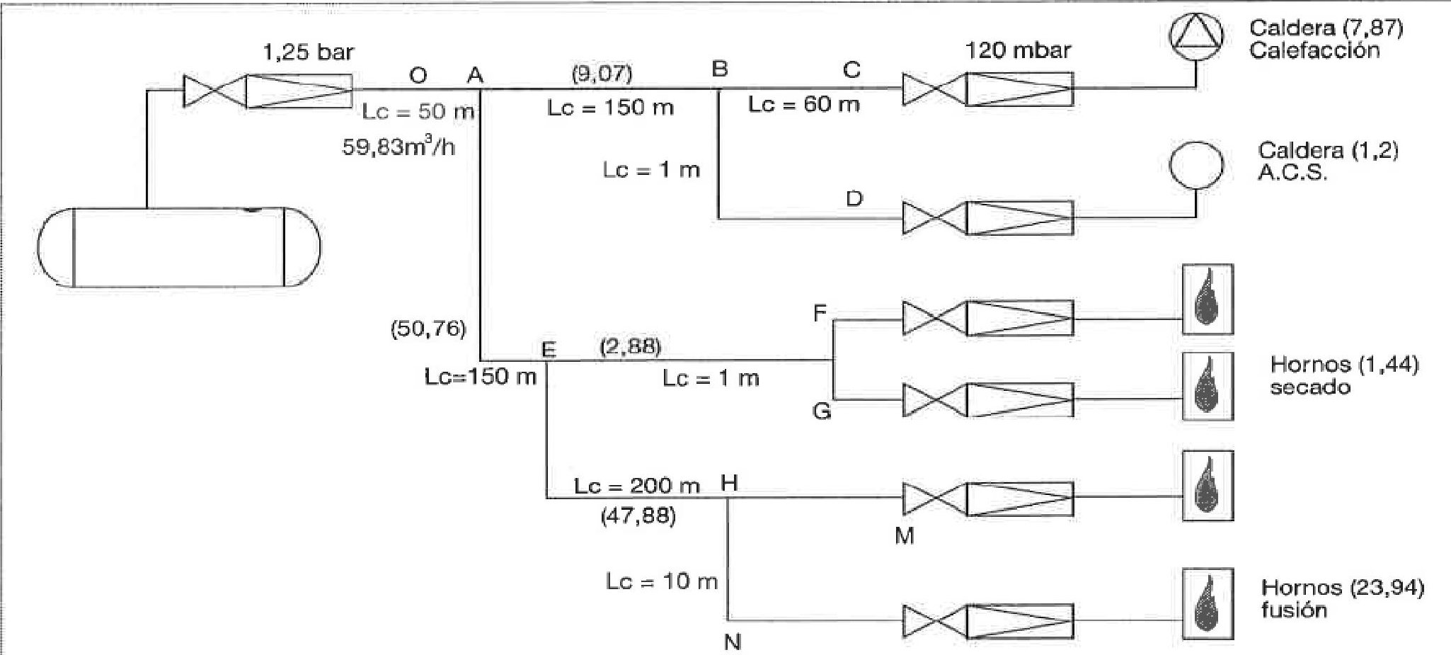
[picture p49: figure]

Figura: Figura 1.6.4b. Esquema de una instalación industrial.

CALCULO DE INSTALACI ´ | ON INDUSTRIAL DE GLP ´

En el esquema de la instalación se encuentran anotadas las longitudes de cálculo (se obtiene al multiplicar por 1,2 las longitudes geométricas) de los tramos entre la salida del regulador del depósito y la entrada de los reguladores de aparatos. La presión de salida del regulador del depósito es de 1,25 bar. Al ser instalación industrial no se limitan las presiones como es el caso del gas canalizado, por lo que el diseño se simplifica con solo dos escalonamientos: El primero impuesto por la vaporización deseada, y el segundo mediante reguladores de BP a 37 mbar, cuya presión mínima a la entrada es de 120 mbar.

Esto hace que la pérdida de carga disponible en los tramos de MP será de PCd = 1,25-0,12 = 1,13 bar.
Las presiones en los nudos intermedios se han de elegir aplicando el sistema de la “J”, consistente en hacer un reparto de la pérdida de carga disponible proporcionalmente entre las longitudes de cálculo de los tramos.
Las longitudes de los cuatro cursos (itinerarios) están dadas en la tabla siguiente:

LONGITUD DE TRAMOS
CURSOS | OA | AB | BC | BD | AE | EFG | EH | HN
VOABC=50+150+60=260m | 50 | 150 | 60
OABD=50+150+1=201m | 50 | 150 | | 1
OAEG=50+150+1=201m | 50 | | | | 150 | 1
OAEHN=50+150+200+10=410m | 50 | | | | 150 | | 200 | 10
CAUDALES m³ /h | 59,83 | 9,07 | 7,87 | 1,2 | 50,76 | 2,88 | 47,88 | 23,94

CALCULO DE INSTALACI ´ | ON INDUSTRIAL DE GLP ´

El curso o itinerario principal es el OAEHN cuya longitud es Lc = 50 + 150 + 200 + 10 = 410 m

Cálculo del primer itinerario principal: Se elige el itinerario principal, el de mayor pérdida de carga, que en este caso será el OAEHN, cuya longitud es Lc = 410 m.
La “J” (pérdida de carga disponible por metro de conducción) del itinerario principal será:

J = 1, 13 bar/410 m = 0, 002756 bar/m

Al tramo OA, de 50 m de longitud, le corresponderán 50 “J” de pérdida de carga, por lo tanto 50 × 0, 002756 = 0, 1378 bar. La presión al final del tramo será: 1,250-0,1378=1,1122 bar
Al resto de los tramos, les corresponderá lo indicado en la siguiente tabla, en donde se incluyen los caudales previstos y las longitudes de cálculo de cada tramo:
TRAMO | CAUDAL | LONGITUD DE CALCULO(Lc) ´ | PERDIDA DE CARGA ADMISIBLE(PCd) ´ | PRESION INICIAL ´ | PRESION FINAL ´

ITINERARIO OAEHN

m³
| /h | Lc | PCd=J×Lc | Pi | Pf=Pi-PCd
OA | 59,83 | 50m | 0,1378bar | 1,25bar | 1,1122bar
AE | 50,76 | 150m | 0,4134bar | 1,1122bar | 0,7086bar
EH | 47,88 | 200m | 0,5512bar | 0,7086bar | 0,1574bar
HM | 23,94 | 1 | 0,0027bar | 0,1574bar | 0,1546bar
HN | 23,94 | 10 | 0,0027bar | 0,1574bar | 0,1546bar

CALCULO DE INSTALACI ´ | ON INDUSTRIAL DE GLP ´

Cálculo del segundo itinerario: Para el siguiente itinerario, el OABC, se calcula nuevamente la “J”: El tramo OA ya está calculado, por lo que se calcula la “J” para el resto: ABC.
La pérdida de carga disponible será (1,1122-0,12) = 0,9922
La “J” valdrá: 0,9922/(150+60) = 0,00472 bar/m
TRAMO | CAUDAL | LONGITUD DE CALCULO(Lc) ´ | PERDIDA DE CARGA ADMISIBLE(PCd) ´ | PRESION INICIAL ´ | PRESION FINAL ´

ITINERARIO ABC

Q | Lc | PCd=J×Lc | Pi | Pf=Pi-PCd
AB | 9.07m³
/h | 150m | 0.708bar | 1.1122bar | 0.4042bar
BC | 7.87m³
/h | 60m | 0.2832bar | 0.4042bar | 0.121bar
Las presiones aquí manejadas son valores relativos mientras que para aplicar la fórmula de Renouard se han de convertir en absolutas (por tratarse de gas a MP). Para ello se deberá añadir el valor de la presión atmosférica normal = 1,01325 bar. Las presiones en los nudos quedan reflejadas en el esquema.
La fórmula usada es la de Renouard para MP:

P

2
A − P
| 2
B = 51, 5 · 1, 16 · Lc · Q

1,82/D

4,82
, en donde 51, 5 × 1, 16 = 59, 74

Los pasos a realizar se simplifican reuniéndolos en una hoja de cálculo:

TRAMO | Pi abs. | Pi² | Pf abs. | Pf | Pi² -Pf=P | Q 1,82 | Lc | R=59.74·Lc·Q 1,82 | R/P | D=(R/P)¹/4,82
OA | 2,26325 | 5,12230 | 2,12075 | 4,49758 | 0,62472 | 1713.93 | 50 | 5119509 | 8194886 | 27.2(30)
AE | 2,12075 | 4,49758 | 1,69325 | 2,86709 | 1,63049 | 1270.72 | 150 | 11386922 | 6983742 | 26.3(30)
EH | 1,69325 | 2,86709 | 1,12325 | 1,26169 | 1,60540 | 1142.56 | 200 | 13651306 | 8503367 | 27.4(30)
AB | 2,12075 | 4,49758 | 1,38683 | 1,92329 | 2,57429 | 55,315 | 150 | 95677 | 192549 | 12.5(15)
BC | 1,38683 | 1,92329 | 1,09325 | 1,19519 | 0,72810 | 42.72 | 60 | 153126 | 210309 | 12.7(15)
BD | 1,38683 | 1,92329 | 1,09325 | 1,19519 | 0,72810 | 1.39 | 1 | 83 | 114 | 2.6(15)
EF/G | 1,69325 | 2,86709 | 1,09325 | 1,19519 | 1,6719 | 6.86 | 1 | 409 | 244.6 | 3.1(15)
HM | 1,17025 | 1,3695 | 1,13325 | 1,28425 | 0,08525 | 23.94 | 1 | 19331.7 | 226765 | 12.9(15)
HN | 1,17025 | 1,3695 | 1,13325 | 1,28425 | 0,08525 | 23.94 | 10 | 193317.5 | 2267653 | 20.8(20)

CALCULO DE INSTALACI ´ | ON INDUSTRIAL DE GLP ´

En los tres primeros tramos se eligen tuberías de 30 mm. de diámetro interior, como mínimo. En los dos últimos, se seleccionan de 15 mm (Figura 1.6.4c).

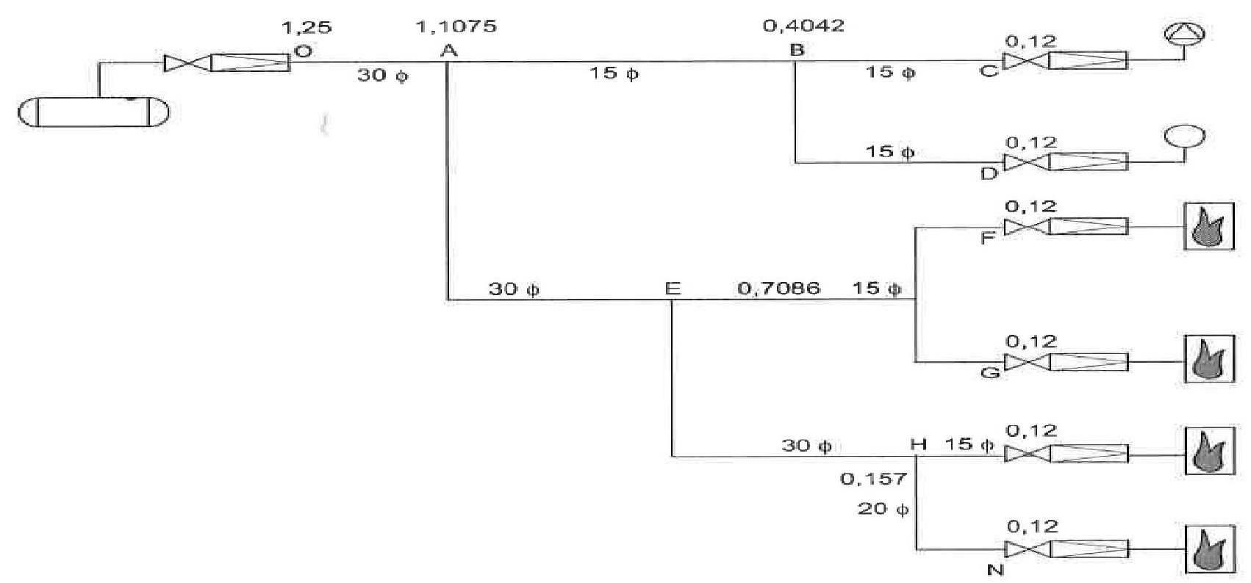
[picture p50: figure]

Figura: Figura 1.6.4c

# CENTROS DE ALMACENAMIENTO

Un centro de almacenamiento se compone por el conjunto o parte de los siguientes elementos (Figura 2a):

Boca de carga

Depósitos con su valvulería y dispositivos de medida y seguridad
Equipo de trasvase (ET) 1

Equipo de vaporización (EV) 2

Equipo de regulación (ER) 3

Equipo de seguridad (ES) (4)

Instalaciones complementarias (5)

(1) Equipo de trasvase. Compuesto por bombas o compresores para poder trasvasar el GLP de un depósito a otro. * Llave de salida (Sa)
(2) Equipo de vaporización. Compuesto de vaporizador y elementos complementarios para producir la vaporización forzada del GLP
(3) Equipo de regulación. Compuesto por el/los regulador(es) y el elemento de seguridad contra sobrepresión
(4) Equipo de seguridad. Dispositivos destinados a la protección de las personas y las cosas, como las válvulas de seguridad por alivio de presión, protección contra la corrosión, contra el fuego, etc.
(5) Instalaciones complementarias. tales como carteles de prevención, vestimenta de protección, linternas, alarma, explosímetro, etc.

# CENTROS DE ALMACENAMIENTO

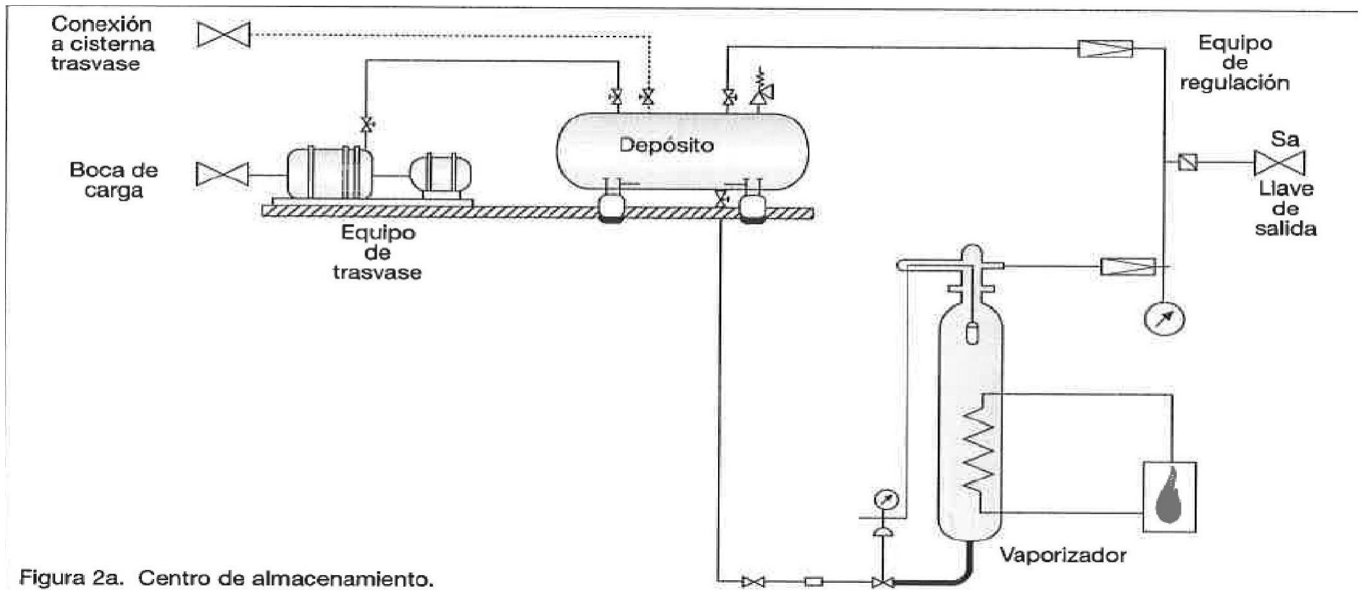
[picture p51: figure]

Figura: Figura 2a. Centro de almacenamiento.

Los depósitos son recipientes destinados a contener los GLP en estado (fase) líquido, bajo presión, para su almacenamiento y consumo.
Estos depósitos se llenan “in situ” mediante camión cisterna. La toma de gas para utilización se realiza a través de conducción fija.
Los depósitos pueden ubicarse aéreos, enterrados o semienterrados (Figura 2b):

Depósitos de superficie o aéreos son los situados al aire libre y cuya generatriz inferior queda a nivel superior del terreno.

# CENTROS DE ALMACENAMIENTO

Depósitos enterrados son los situados enteramente por debajo del terreno circundante. Su generatriz superior debe distar entre 30 y 50 cm del terreno. Una profundidad mayor dificultaría los trabajos de trasvase.

Depósito semienterrado es el depósito no situado enteramente por debajo del terreno circundante pero que, cumpliendo una serie de requisitos, es considerado como si estuviera enterrado.

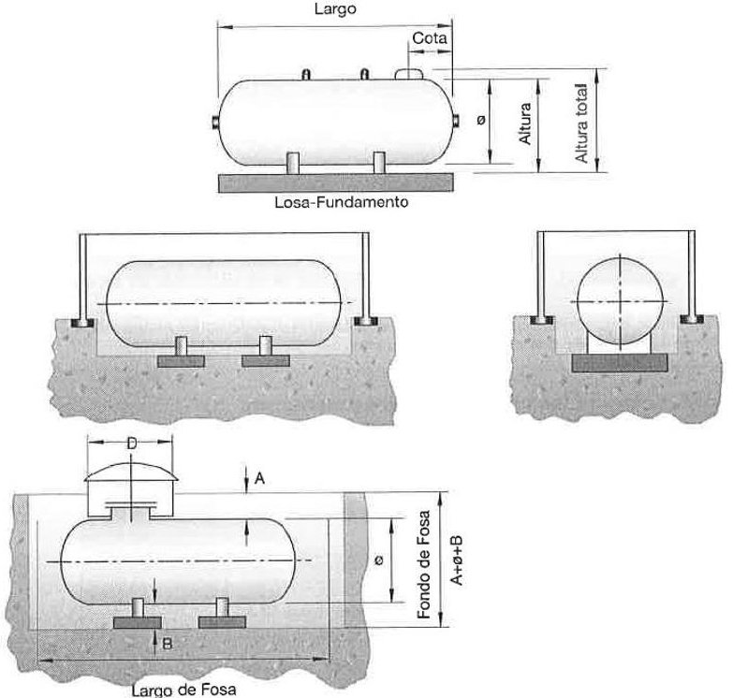
[picture p52: figure]

Figura: Figura 2b. Depósitos aéreos, enterrados y semienterrados.

# CENTROS DE ALMACENAMIENTO

Se considerarán depósitos pequeños a los de volumen hasta los 20 m³ y grandes los mayores.
El diseño de un depósito tiene en cuenta la presión máxima de trabajo (de timbre) correspondiente al GLP a contener. Dicha presión es la resultante de la temperatura de 60◦C. que es de unos 20 bar (se toma la del propano). La presión de prueba del depósito es un 30 % superior a dicha presión (26 bar).
Los depósitos cilíndricos se componen de una virola con sendos fondos en sus extremos que pueden ser casquetes semiesféricos o elípticos, a tener en cuenta al considerar las distancias de seguridad (Dp) desde las paredes del depósito. Las superficies externas de los depósitos se han de proteger contra la corrosión mediante revestimiento adecuado. Los depósitos de superficie se entregan con pintura protectora en blanco y los destinados a ser enterrados, con recubrimiento protector contra la corrosión y con arqueta para contener los accesorios.
Según la reglamentación vigente, los depósitos deberán llevar dos placas de datos:

Placa de diseño: a suministrar por el OTC, con indicación de la presión de diseño y máxima de servicio, número de registro del depósito y fecha de la primera y sucesivas pruebas de presión (retimbrados).
Placa de identificación, indicando fabricante, número de fabricación, volumen m³
), diámetro, Superficie exterior, etc.

Una vez en funcionamiento, los depósitos han de quedar protegidos contra los agentes y acciones externas según sea la ubicación del depósito:
Los aéreos hasta 20 m³
, cubiertos con una capota.

Los enterrados, en arqueta con tapa.

# CENTROS DE ALMACENAMIENTO

En ambos casos, protegidos con cerradura o quedando el depósito en recinto cercado.
Los elementos mínimos (ver punto T3: 2.8 “Equipo de control y maniobra”) a incorporar en los depósitos son: Boca de carga (puede ir desplazada por exigencias de distancia al aparcamiento o por existir equipo de trasvase), indicadores de nivel, de lectura continua y otro para máximo llenado (punto alto), manómetro de lectura directa, válvula de seguridad por alivio de presión, tomas de fase líquida y otra de fase gaseosa, con válvulas de exceso de flujo, drenaje y borna de toma de tierra.

El grado máximo de llenado será el 85 % en volumen, considerando la masa en volumen del gas a 20◦ C
Cuando puedan existir grandes diferencias de temperatura en un mismo día, en verano o en invierno, se recomienda no pasar del 80 % el grado de llenado. (pensar que en el propano, por cada grado que aumente su temperatura, el volumen aumenta un 0,324 %).
Criterios de selección de los depósitos
Los depósitos aéreos presentan, respecto a los enterrados, una mayor facilidad de inspección, limpieza y mantenimiento, mientras que los enterrados resultan más estéticos y con mejor protección mecánica contra agentes externos y requieren menor espacio utilizado ya que las distancias de seguridad a mantener son menores.
Los depósitos enterrados requieren una obra civil más costosa que los aéreos (se ha de pensar en las pruebas de presión reglamentarias). Por otro lado, su vaporización se ve disminuida en zonas normales.
Los depósitos semienterrados se elegirán cuando exista impedimento justificado como terreno rocoso, terreno con pendiente pronunciada o la capa freática sea alta.

# CLASIFICACION DE LOS CENTROS DE ALMACENAMIENTO ´

De acuerdo con la suma de volúmenes geométricos de todos los depósitos existentes en el centro de almacenamiento y de su ubicación, éstos se clasifican en los siguientes grupos:

AEREOS ´
Denominación | Volumen del Centro de almacenamiento
A-0 | Hasta 5m³
A-1 | Mayor de 5m³ , hasta 10m³
A-2 | Mayor de 10m³ , hasta 20m³
A-3 | Mayor de 20m³ , hasta 100m³
A-4 | Mayor de 100m³ , hasta 500m³
A-5 | Mayor de 500m³ , hasta 2000m³
ENTERRADOS O SEMIENTERRADOS
Denominación | Volumen del Centro de almacenamiento
E-0 | Hasta 5m³
E-1 | Mayor de 5m³ , hasta 10m³
E-2 | Mayor de 10m³ , hasta 100m³
E-3 | Mayor de 100m³ , hasta 500m³

Existe la posibilidad de que la clasificación cambie con la nueva normativa.
No se permite enterrar o semienterrar depósitos de más de 60 m³ de capacidad unitaria
Las dimensiones de los depósitos no se han normalizado oficialmente. En los centros de almacenamiento, se autorizan los aéreos hasta un volumen total máximo de 2 000 m³ y los enterrados o semienterrados, hasta 500 m³ (volumen unitario máximo de 60 m³).

# ESTACION DE GLP ´

Estación de GLP es la superficie de terreno limitada por las distancias de seguridad según la referencia 4 que figura en el cuadro de distancias (ver pag. 68) en función con la clasificación
Las distancias de seguridad (Do y Dp) son aquellas mínimas que se han de guardar entre el depósito y los diferentes puntos para los que el almacenamiento de GLP puede representar algún riesgo (inmuebles, vías, sótanos, alcantarillas, desagües, etc.) o desde los que pueden provenir algún riesgo (límite de propiedad, “puntos calientes”, vías públicas, etc.). Según la normativa, a partir de las distancias de seguridad, los riesgos de que se formen mezclas explosivas dentro de los límites de inflamabilidad, son de menor consideración.
Do Distancia medida desde los “orificios” del depósito. También designada por S.
Dp Distancia medida desde el perímetro del depósito. También designada por S1
Orificios son cualquier abertura de un depósito de GLP, no cerrada por medio de tapones roscados o bridas ciegas por donde, en su función normal, puede dar lugar a una eventual salida de gas. Son orificios, las válvulas de seguridad y las bocas de carga situadas en el depósito (no alejadas). Se considerará la más alta.

# ESTACION DE GLP ´

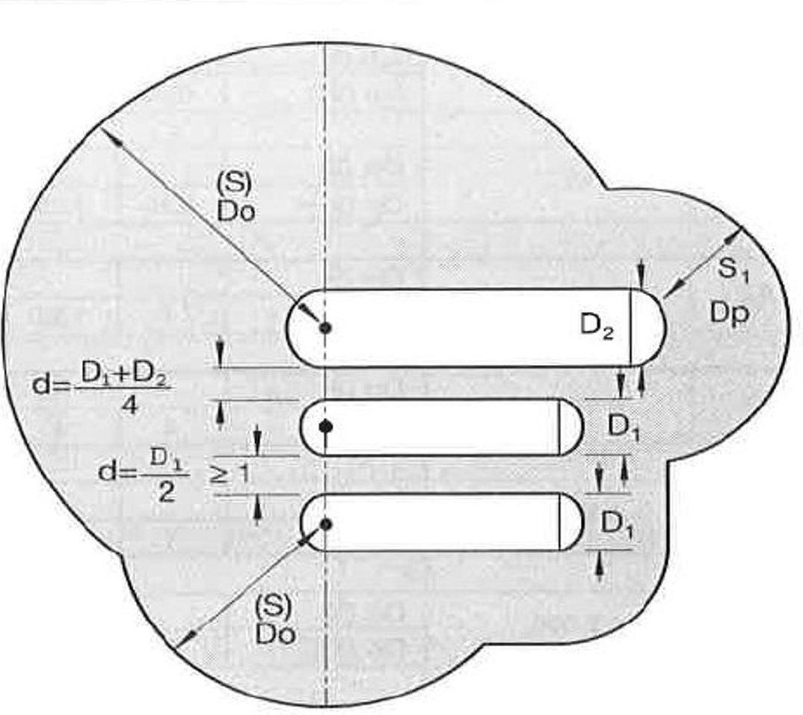
[picture p53: figure]

Figura: Figura 2.2. Estación de GLP formada por las distancias Do y Dp de la referencia 4.

Según estas distancias, no todo el Centro de almacenamiento queda en el interior de la Estación. Para obviarlo, sería necesario que el reglamento estableciera distancias de seguridad no solo alrededor del depósito, sino también alrededor del resto de los equipos.

Diseño constructivo del centro de almacenamiento de GLP
Al proyecto el Centro de almacenamiento se han de tener en cuenta las siguientes consideraciones:
Deberá estar cubierto mediante una solera de hormigón con cuantía mínima de 150 kg de cemento por m³ , y de al
menos de 10 cm de espesor

# ESTACION DE GLP ´

Los depósitos han de respetar las distancias de seguridad establecidas. Ver tabla de página siguiente.

Los depósitos cilíndricos se instalarán con su eje longitudinal sensiblemente horizontal, con una ligera inclinación hacia el orificio de drenaje en los de superficie.

La zona de ubicación de los depósitos será horizontal (referencia 1 del cuadro de distancias).

Cuando se instalen varios depósitos en un mismo Centro, ubicarlos de forma que no se pueda producir el sobrellenado de uno a costa de los otros, utilizando válvulas de retención o colocándolos con la generatriz superior al mismo nivel. Figura 2.3.1b.
Aparcamiento del camión cisterna. La maniobra necesaria para salir del Centro deberá resultar fácil. (El camión cisterna se deberá situar en posición de salida antes de comenzar la descarga).

Si no se puede ubicar el depósito a una distancia del aparcamiento destinado a la cisterna, inferior a la longitud de las mangueras (unos 30 m), se deberá situar la boca de carga a distancia. La longitud física de las mangueras alcanza los 40 m, pero la eficaz es unos metros menos.

Para volúmenes grandes se recomienda dividir la capacidad entre depósitos de menor volumen, según característica de la instalación. Disponer de dos depósitos ofrece ventajas en su mantenimiento y suministro, lo que resulta impres-cindible en instalaciones industriales.

A igualdad de volumen, elegir los de menor diámetro para conseguir una mayor superficie mojada y una mayor vaporización.

Cuando los depósitos, en función de su capacidad, lleven apoyos de hormigón en lugar de patas —con zapatas—, se intercalará entre el depósito y estos apoyos juntas de neopreno para evitar un contacto directo.

# CUADRO DE DISTANCIAS DE SEGURIDAD

TABLA DE DISTANCIAS DE SEGURIDAD
Instalación | Grupo | Volumen m³ | Distancia | Referencias
1 | 2 | 3 | 4A | 4B | 5 | 6
Aérea | A0 | ≤ 5 | Do (S) | | | | 3 | 3 | 6 | 3
| | | Dp (S1) | 0,60 | 1,25 | 0,60 | 2 | 2 | | 3
| A1 | ≤ 10 | Do (S) | | | | 5 | 5 | 10 | 3
| | | Dp (S1) | 0,60 | 1,25 | 0,60 | 3 | 3 | | 3
| A2 | ≤ 20 | Do (S) | | | | 7,5 | 7,5 | 15 | 3
| | | Dp (S1) | 1 | 1,25 | 1 | 5 | 5 | | 3
| A3 | ≤ 100 | Do (S) | | | | 10 | 10 | 20 | 3
| | | Dp (S1) | 1 | 3 | 5 | 7,5 | 7,5 | | 3
| A4 | ≤ 500 | Do (S) | | | | 15 | 15 | 30 | 3
| | | Dp (S1) | 1 | 5 | 5 | 10 | 10 | | 3
| A5 | ≤ 2000 | Do (S) | | | | 30 | 30 | 60 | 3
| | | Dp (S1) | 2 | 10 | 7,5 | 20 | 20 | | 3
Resto | E0 | ≤ 5 | Do (S) | 0,8 | 1,5 | 0,8 | 3 | 3 | 6 | 3
| E1 | ≤ 10 | Do (S) | 0,8 | 2 | 1 | 4 | 4 | 8 | 3
| E2 | ≤ 100 | Do (S) | 0,8 | 3 | 2 | 5 | 5 | 10 | 3
| E3 | ≤ 500 | Do (S) | 0,8 | 5 | 3 | 10 | 10 | 20 | 3

Referencia 1: Espacio libre alrededor de la proyección sobre el terreno del depósito. Quedará horizontal para facilitar el desplazamiento del equipo de extinción de incendios.
Referencia 2: Distancia al cerramiento. El recinto no podrá contener elementos ajenos al servicio.
Referencia 3: Distancia a muros o paredes ciegas (R-120 como mínimo).
Referencia 4A: Distancia a límite de propiedad, proyección de línea aéreas de alta tensión.
Referencia 4B: Distancia a aberturas de inmuebles, aberturas de sótanos, aberturas de alcantarillas, focos fijos de inflamación, motores fijos de explosión, vías públicas, férreas o fluviales navegables equipos eléctricos no protegidos, y desagües. Determina la Estación de GLP.
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
